Cyberspecies/Synth-Head/Software/Testing_N_Experimentation/Alpha_Release_Stack/IMPLEMENTATION_SUMMARY.md

# Project Implementation Summary

## Files Created

### Core Application Files

1. **main_new.cpp**
   - Main application entry point
   - Initializes UART and LED controllers
   - Handles data reception and LED updates
   - Manages button state transmission
   - Includes debug output

2. **include/UartController.h**
   - UART controller class header
   - Defines data structures for 196-byte LED frames
   - Button management (GPIO 5, 6, 7, 10)
   - UART configuration (GPIO 11 RX, GPIO 12 TX, 1Mbps)

3. **include/UartController.impl.hpp**
   - UART controller implementation
   - Receive buffer management for (13+13+9+14)×4 = 196 bytes
   - Button reading with debouncing
   - Button state transmission (4 bytes)
   - Data parsing by LED section

4. **LedController_new.h**
   - LED controller class header
   - Manages 4 separate LED strips (RGBW SK6812)
   - Supports 49 total LEDs (13+13+9+14)
   - Individual strip control methods

5. **LedController_new.impl.hpp**
   - LED controller implementation
   - NeoPixel strip initialization
   - RGBW data parsing and application
   - Test patterns and effects

6. **UART_LED_README.md**
   - Comprehensive documentation
   - Data protocol specification
   - Sender implementation examples (Python & Arduino)
   - Troubleshooting guide
   - Power considerations

## System Architecture

### Data Flow

```
Sender Device                     Receiver Device (This ESP32)
     |                                      |
     |  196 bytes LED data (RGBW)          |
     |------------------------------------>|
     |        UART @ 1Mbps                 |
     |                                      |
     |    4 bytes button state             |
     |<------------------------------------|
     |                                      |
```

### LED Data Structure (196 bytes total)

| Section | LEDs | Start Byte | End Byte | GPIO Pin |
|---|---|---|---|---|
| Left Fin | 13 | 0 | 51 | 18 |
| Right Fin  | 13 | 52 | 103 | 38 |
| Tongue | 9 | 104 | 139 | 8 |
| Scale | 14 | 140 | 195 | 37 |

Each LED = 4 bytes [R, G, B, W]

### Button Configuration

| Button | GPIO | Array Index |
|---|---|---|
| A | 5 | 0 |
| B | 6 | 1 |
| C | 7 | 2 |
| D | 10 | 3 |

## Coding Style Compliance

All code follows ARCOS coding style guidelines:
- ✅ 2-space indentation
- ✅ Tight brace style (no space before `{`)
- ✅ snake_case for variables
- ✅ camelCase for methods
- ✅ PascalCase for classes
- ✅ ALL_CAPS for constants
- ✅ Pointer/reference attached to type (`uint8_t*`)

## Next Steps

### To Use This Code:

1. **Rename/Replace Main File:**
   ```bash
   # Backup old main
   mv main.cpp main_old.cpp
   # Use new main
   mv main_new.cpp main.cpp
   ```

2. **Compile and Upload:**
   ```bash
   pio run --target upload
   ```

3. **Create Sender:**
   - Use Python example in UART_LED_README.md
   - Or use Arduino/ESP32 sender example
   - Connect UART pins (TX ↔ RX crossover)

4. **Test:**
   - Open serial monitor at 115200 baud
   - Send LED data from sender
   - Press buttons and verify transmission
   - Check debug output

## Key Features

- ✅ High-speed UART (1Mbps) for smooth animations
- ✅ 49 RGBW LEDs support (196 bytes/frame)
- ✅ 4-button input with state transmission
- ✅ Modular design (separate UART and LED controllers)
- ✅ Comprehensive error handling
- ✅ Debug output for monitoring
- ✅ Test patterns included

## Performance

- **Update Rate:** Up to 100 FPS theoretical (limited by UART bandwidth)
- **Recommended:** 30-60 FPS for stable operation
- **Button Polling:** 20 Hz (50ms intervals)
- **UART Bandwidth:** 1Mbps = 125 KB/s = 637 frames/second max

## Hardware Requirements

- ESP32-S3 (or compatible)
- 4× SK6812 RGBW LED strips
- 4× Push buttons
- 5V power supply (≥5A recommended)
- UART connection to sender device

---

**Status:** ✅ Ready for testing
**Date:** October 22, 2025
**ARCOS Alpha Release Stack**
