Cyberspecies/Synth-Head/Software/Testing_N_Experimentation/Alpha_Release_Stack/partitions_16mb.csv

# ESP32-S3-WROOM-1U-N16 Partition Table (16MB Flash)
# Name | Type | SubType | Offset | Size | Flags
nvs | data | nvs | 0x9000 | 0x5000
otadata | data | ota | 0xe000 | 0x2000
app0 | app | ota_0 | 0x10000 | 0x600000
app1 | app | ota_1 | 0x610000 | 0x600000
spiffs | data | spiffs | 0xC10000 | 0x3F0000
