Cyberspecies/Synth-Head/Embedded/Condensed/Substructure Power Distribution/Substructure Power Distribution.kicad_pcb

## KiCad design Embedded/Condensed/Substructure Power Distribution/Substructure Power Distribution.kicad_pcb (2025-07-12)

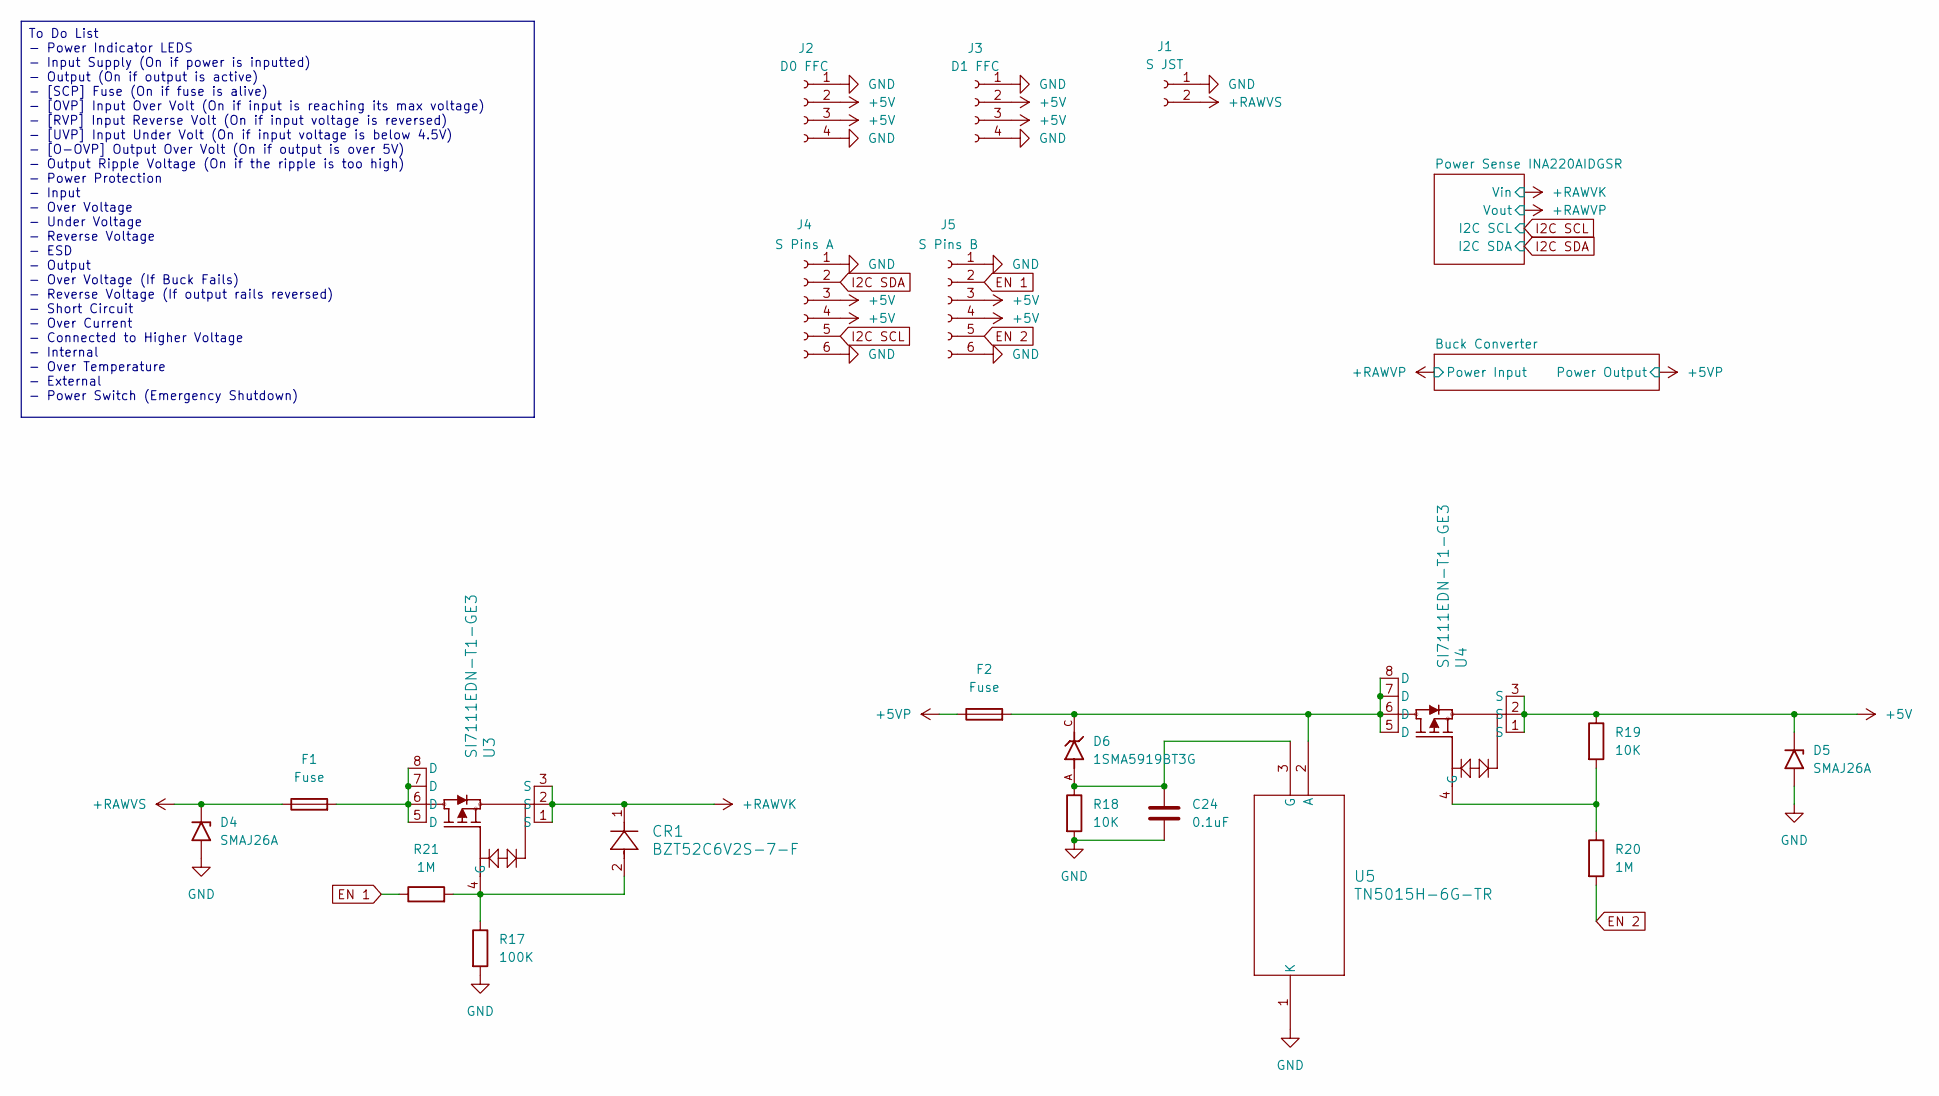
[picture p35: schematic Substructure Power Distribution.kicad_sch]

Parts:
C24: 0.1uF; C_0603_1608Metric_Pad1.08x0.95mm_HandSolder
CR1: BZT52C6V2S-7-F; SOD323_DIO
D4, D5: SMAJ26A; D_SMA
D6: 1SMA5919BT3G; DIOM5226X220N; PARTREV 10
F1, F2: Fuse; Fuse_1206_3216Metric_Pad1.42x1.75mm_HandSolder; LCSC C126815
J1: S JST; AMASS_XT30PW-M_1x02_P2.50mm_Horizontal
J2: D0 FFC; JST_XH_B4B-XH-A_1x04_P2.50mm_Vertical
J3: D1 FFC; JST_XH_B4B-XH-A_1x04_P2.50mm_Vertical
J4: S Pins A; PinHeader_1x06_P2.54mm_Vertical
J5: S Pins B; PinHeader_1x06_P2.54mm_Vertical
R17: 100K; R_0603_1608Metric_Pad0.98x0.95mm_HandSolder
R18, R19: 10K; R_0603_1608Metric_Pad0.98x0.95mm_HandSolder
R20, R21: 1M; R_0603_1608Metric_Pad0.98x0.95mm_HandSolder
U3, U4: SI7111EDN-T1-GE3; MOSFET_0DN-T1-GE3_VIS
U5: TN5015H-6G-TR; D2PAK_T2550_STM-M

Connections:
+5V: D5.1 (A1), J2.2, J2.3, J3.2, J3.3, J4.3, J4.4, J5.3, J5.4, R19.1, U4.1 (S), U4.2 (S), U4.3 (S)
+5VP: F2.1; also elsewhere on the board
+RAWVK: CR1.1, U3.1 (S), U3.2 (S), U3.3 (S); also elsewhere on the board
+RAWVS: D4.1 (A1), F1.1, J1.2
EN 1: J5.2, R21.1
EN 2: J5.5, R20.2
GND: C24.2, D4.2 (A2), D5.2 (A2), J1.1, J2.1, J2.4, J3.1, J3.4, J4.1, J4.6, J5.1, J5.6, R17.2, R18.2, U5.1 (K); also elsewhere on the board
I2C SCL: J4.5; also elsewhere on the board
I2C SDA: J4.2; also elsewhere on the board
unnamed: F1.2, U3.5 (D), U3.6 (D), U3.7 (D), U3.8 (D)
unnamed: CR1.2, R17.1, R21.2, U3.4 (G)
unnamed: R19.2, R20.1, U4.4 (G)
unnamed: D6.C, F2.2, U4.5 (D), U4.6 (D), U4.7 (D), U4.8 (D), U5.2 (A)
unnamed: C24.1, D6.A, R18.1, U5.3 (G)

Notes on the sheet:
To Do List - Power Indicator LEDS - Input Supply (On if power is inputted) - Output (On if output is active) - [SCP] Fuse (On if fuse is alive) - [OVP] Input Over Volt (On if input is reaching its max voltage) - [RVP] Input Reverse Volt (On if input voltage is reversed) - [UVP] Input Under Volt (On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

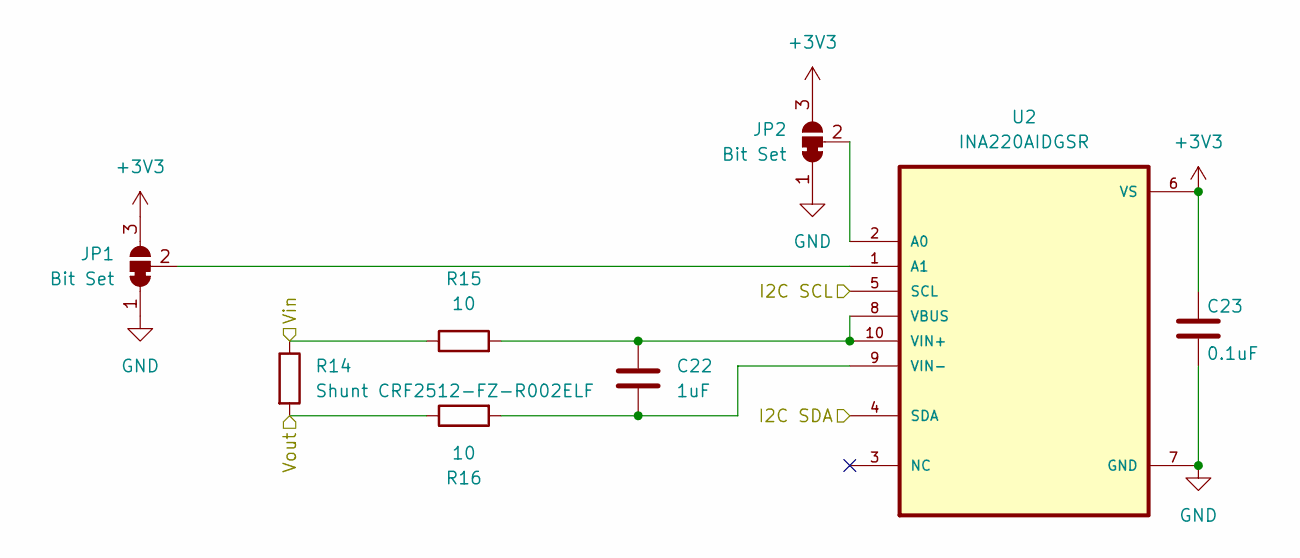
[picture p36: schematic PowerSense.kicad_sch]

Parts:
C22: 1uF; C_0402_1005Metric_Pad0.74x0.62mm_HandSolder
C23: 0.1uF; C_0402_1005Metric_Pad0.74x0.62mm_HandSolder
JP1, JP2: Bit Set; SolderJumper-3_P1.3mm_Bridged2Bar12_RoundedPad1.0x1.5mm
R14: Shunt CRF2512-FZ-R002ELF; R_2512_6332Metric_Pad1.40x3.35mm_HandSolder
R15, R16: 10; R_0402_1005Metric_Pad0.72x0.64mm_HandSolder
U2: INA220AIDGSR; SOP50P490X110-10N

Connections:
+3V3: C23.1, JP1.3 (B), JP2.3 (B), U2.6 (VS)
+RAWVK: R14.1, R15.1; also elsewhere on the board
+RAWVP: R14.2, R16.1; also elsewhere on the board
GND: C23.2, JP1.1 (A), JP2.1 (A), U2.7 (GND); also elsewhere on the board
I2C SCL: U2.5 (SCL); also elsewhere on the board
I2C SDA: U2.4 (SDA); also elsewhere on the board
unnamed: JP1.2 (C), U2.1 (A1)
unnamed: JP2.2 (C), U2.2 (A0)
unnamed: C22.1, R15.2, U2.8 (VBUS), U2.10 (VIN+)
unnamed: C22.2, R16.2, U2.9 (VIN-)

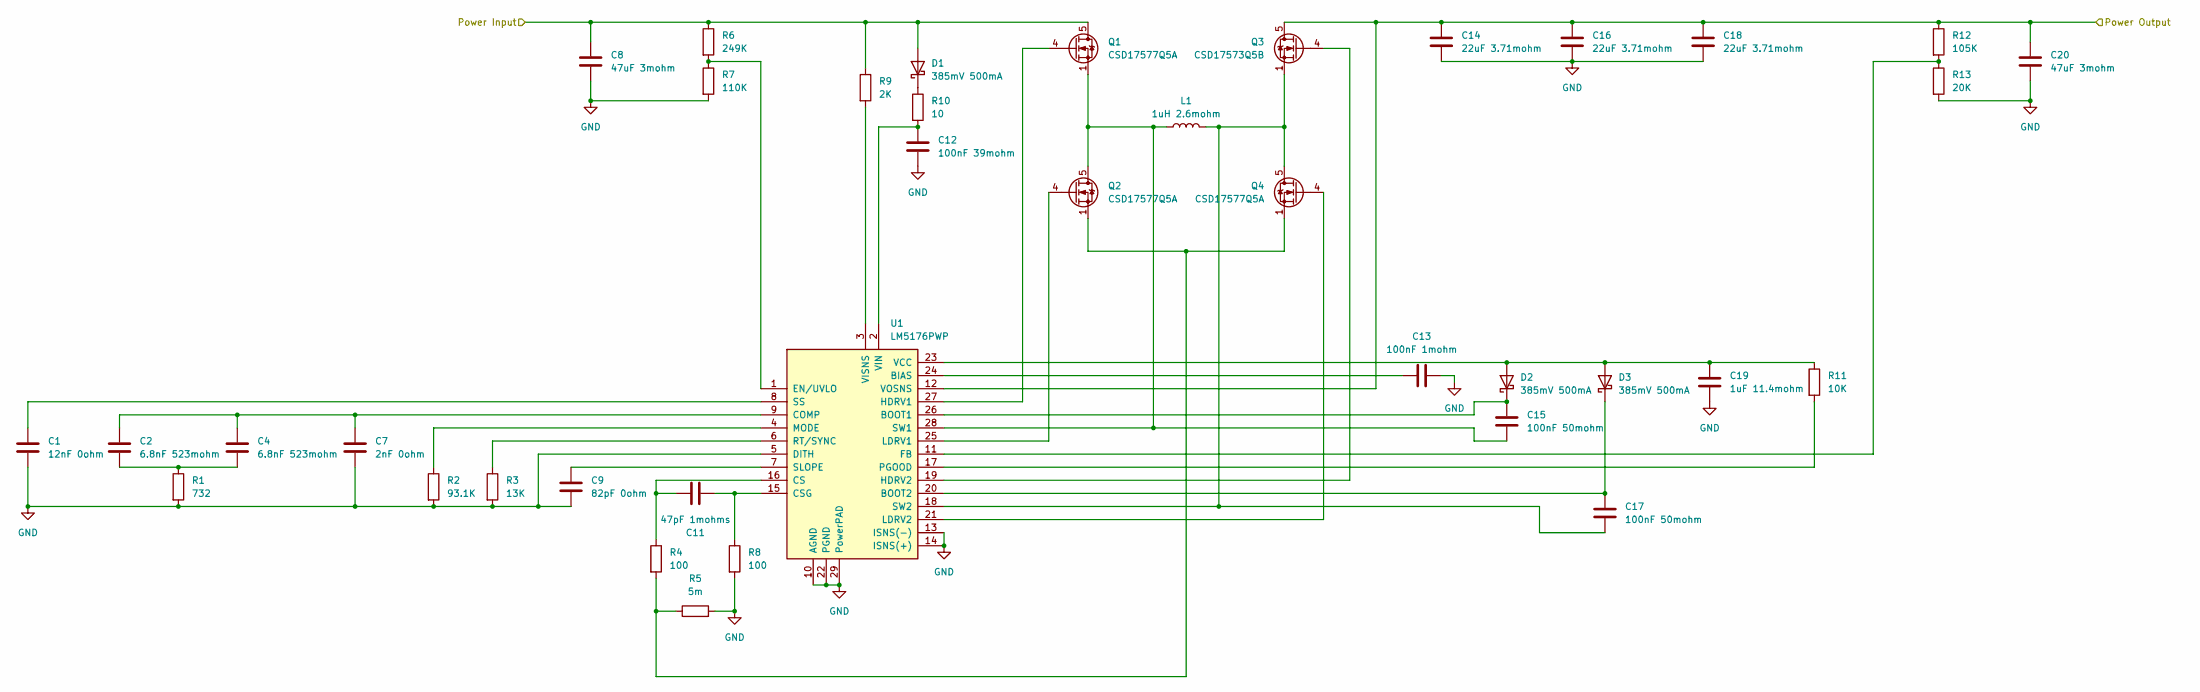
[picture p37: schematic buckconverter.kicad_sch]

Parts:
C1: 12nF 0ohm; C_0603_1608Metric_Pad1.08x0.95mm_HandSolder; LCSC C519540
C2, C4: 6.8nF 523mohm; C_0402_1005Metric_Pad0.74x0.62mm_HandSolder; LCSC C3840335
C7: 2nF 0ohm; C_0402_1005Metric_Pad0.74x0.62mm_HandSolder; LCSC C1845704
C8, C20: 47uF 3mohm; C_1210_3225Metric_Pad1.33x2.70mm_HandSolder; LCSC C77101
C9: 82pF 0ohm; C_0402_1005Metric_Pad0.74x0.62mm_HandSolder; LCSC C650992
C11: 47pF 1mohms; C_0402_1005Metric_Pad0.74x0.62mm_HandSolder; LCSC C76970
C12: 100nF 39mohm; R_0402_1005Metric_Pad0.72x0.64mm_HandSolder; LCSC C2181865
C13: 100nF 1mohm; C_0402_1005Metric_Pad0.74x0.62mm_HandSolder; LCSC C133086
C14, C16, C18: 22uF 3.71mohm; C_0603_1608Metric_Pad1.08x0.95mm_HandSolder; LCSC C86295
C15, C17: 100nF 50mohm; C_0603_1608Metric_Pad1.08x0.95mm_HandSolder; LCSC C92490
C19: 1uF 11.4mohm; C_0402_1005Metric_Pad0.74x0.62mm_HandSolder; LCSC C181015
D1: 385mV 500mA; D_SOD-123; LCSC C155367
D2, D3: 385mV 500mA; D_SOD-123; LCSC C398783
L1: 1uH 2.6mohm; XAL7070-102ME; LCSC C6609502
Q1, Q2, Q4: CSD17577Q5A; TDSON-8-1; LCSC C475504
Q3: CSD17573Q5B; TDSON-8-1; LCSC C202231
R1: 732; R_0402_1005Metric_Pad0.72x0.64mm_HandSolder; LCSC C2085222
R2: 93.1K; R_0402_1005Metric_Pad0.72x0.64mm_HandSolder; LCSC C2085865
R3: 13K; R_0402_1005Metric_Pad0.72x0.64mm_HandSolder; LCSC C294438
R4, R8: 100; R_0402_1005Metric_Pad0.72x0.64mm_HandSolder; LCSC C844713
R5: 5m; R_2512_6332Metric_Pad1.40x3.35mm_HandSolder; LCSC C22468851
R6: 249K; C_0402_1005Metric_Pad0.74x0.62mm_HandSolder; LCSC C482111
R7: 110K; C_0402_1005Metric_Pad0.74x0.62mm_HandSolder; LCSC C481928
R9: 2K; C_0402_1005Metric_Pad0.74x0.62mm_HandSolder; LCSC C482125
R10: 10; R_0402_1005Metric_Pad0.72x0.64mm_HandSolder; LCSC C481926
R11: 10K; R_0402_1005Metric_Pad0.72x0.64mm_HandSolder; LCSC C71617
R12: 105K; R_0603_1608Metric_Pad0.98x0.95mm_HandSolder; LCSC C227540
R13: 20K; R_0603_1608Metric_Pad0.98x0.95mm_HandSolder; LCSC C105575
U1: LM5176PWP; HTSSOP-28-1EP_4.4x9.7mm_P0.65mm_EP3.4x9.5mm_ThermalVias

Connections:
+5VP: C14.1, C16.1, C18.1, C20.1, Q3.5 (D), R12.1, U1.12 (VOSNS); also elsewhere on the board
+RAWVP: C8.1, D1.2 (A), Q1.5 (D), R6.1, R9.1; also elsewhere on the board
GND: C1.2, C7.2, C8.2, C9.2, C12.2, C13.2, C14.2, C16.2, C18.2, C19.2, C20.2, R1.2, R2.2, R3.2, R5.2, R7.2, R8.2, R13.2, U1.5 (DITH), U1.10 (AGND), U1.13 (ISNS(-)), U1.14 (ISNS(+)), U1.22 (PGND), U1.29 (PowerPAD); also elsewhere on the board
unnamed: C2.2, C4.2, R1.1
unnamed: D1.1 (K), R10.1
unnamed: C19.1, D2.2 (A), D3.2 (A), R11.1, U1.23 (VCC)
unnamed: C15.1, D2.1 (K), U1.26 (BOOT1)
unnamed: C17.1, D3.1 (K), U1.20 (BOOT2)
unnamed: Q1.4 (G), U1.27 (HDRV1)
unnamed: C15.2, L1.1, Q1.1 (S), Q1.2 (S), Q1.3 (S), Q2.5 (D), U1.28 (SW1)
unnamed: Q2.4 (G), U1.25 (LDRV1)
unnamed: Q2.1 (S), Q2.2 (S), Q2.3 (S), Q4.1 (S), Q4.2 (S), Q4.3 (S), R4.2, R5.1
unnamed: Q3.4 (G), U1.19 (HDRV2)
unnamed: C17.2, L1.2, Q3.1 (S), Q3.2 (S), Q3.3 (S), Q4.5 (D), U1.18 (SW2)
unnamed: Q4.4 (G), U1.21 (LDRV2)
unnamed: C13.1, U1.24 (BIAS)
unnamed: C2.1, C4.1, C7.1, U1.9 (COMP)
unnamed: C11.1, R4.1, U1.16 (CS)
unnamed: C11.2, R8.1, U1.15 (CSG)
unnamed: R6.2, R7.1, U1.1 (EN/UVLO)
unnamed: R12.2, R13.1, U1.11 (FB)
unnamed: R2.1, U1.4 (MODE)
unnamed: R11.2, U1.17 (PGOOD)
unnamed: R3.1, U1.6 (RT/SYNC)
unnamed: C9.1, U1.7 (SLOPE)
unnamed: C1.1, U1.8 (SS)
unnamed: C12.1, R10.2, U1.2 (VIN)
unnamed: R9.2, U1.3 (VISNS)

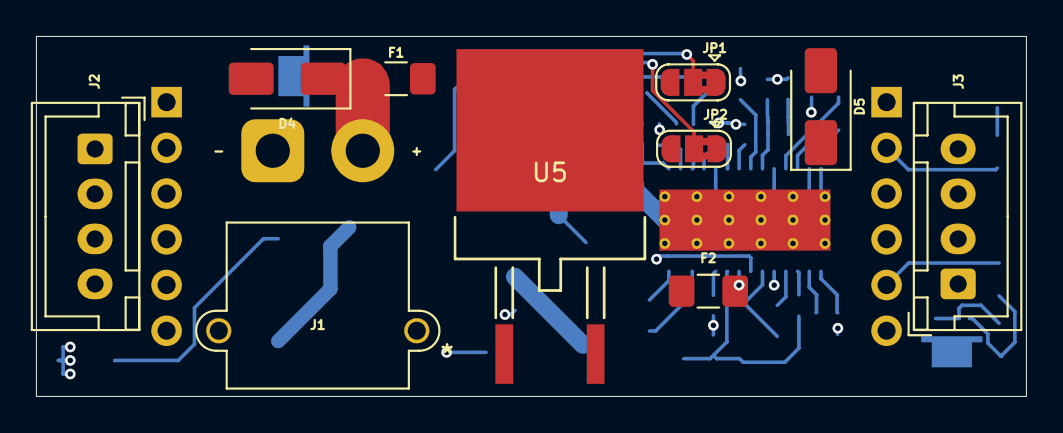
[picture p38: board Embedded/Condensed/Substructure Power Distribution/Substructure Power… from above]

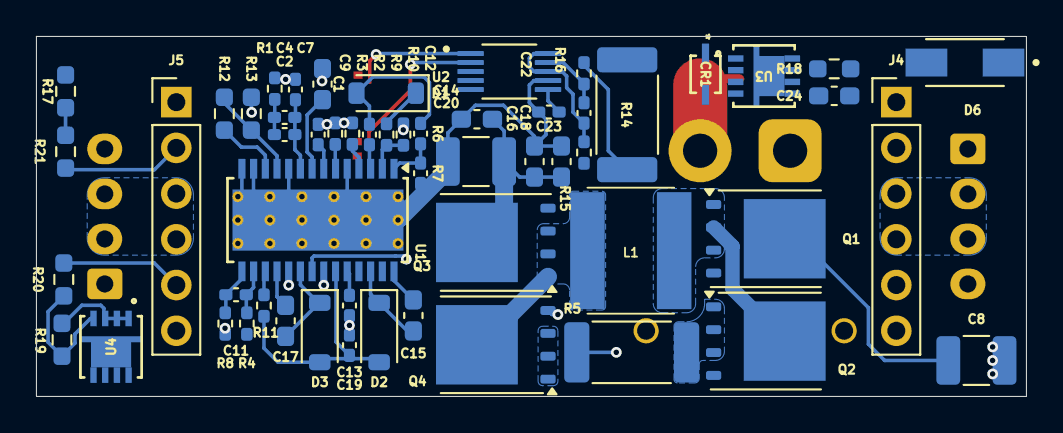
[picture p39: board Embedded/Condensed/Substructure Power Distribution/Substructure Power… from below]

Board: 4 copper layers, 55.0 x 20.0 mm, 66 parts (56 on the bottom side), 45 nets.
