Cyberspecies/Synth-Head/Embedded/Recondensed/Main Buttons/Main Buttons.kicad_pcb

## KiCad design Embedded/Recondensed/Main Buttons/Main Buttons.kicad_pcb (2025-07-26)

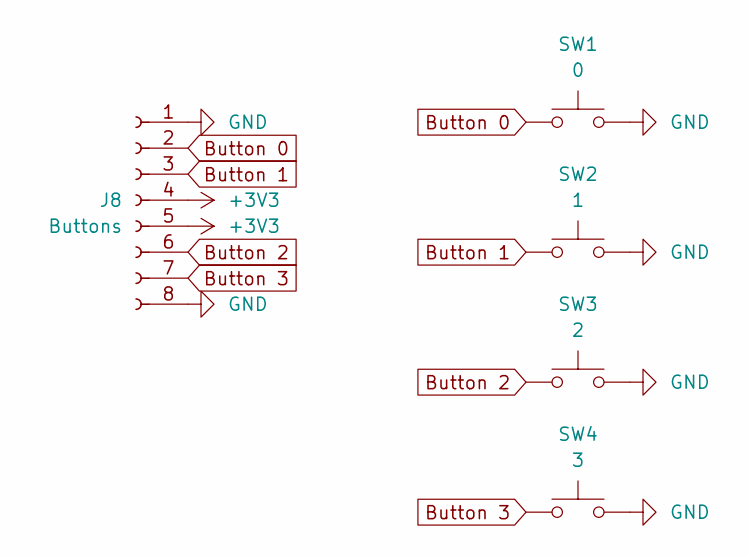
[picture p40: schematic Main Buttons.kicad_sch]

Parts:
J8: Buttons; JST_GH_SM08B-GHS-TB_1x08-1MP_P1.25mm_Horizontal
SW1: 0; SW_PUSH_6mm_H5mm
SW2: 1; SW_PUSH_6mm_H5mm
SW3: 2; SW_PUSH_6mm_H5mm
SW4: 3; SW_PUSH_6mm_H5mm

Connections:
+3V3: J8.4, J8.5
Button 0: J8.2, SW1.1
Button 1: J8.3, SW2.1
Button 2: J8.6, SW3.1
Button 3: J8.7, SW4.1
GND: J8.1, J8.8, SW1.2, SW2.2, SW3.2, SW4.2

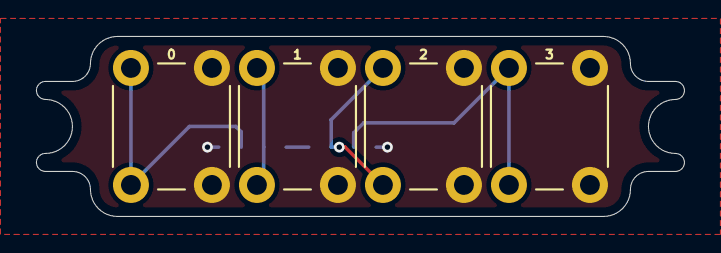
[picture p41: board Main Buttons.kicad_pcb from above]

Board: 2 copper layers, 36.0 x 10.0 mm, 5 parts (1 on the bottom side), 6 nets.
