Cyberspecies/Synth-Head/Embedded/HUB75 Display Adapter/HUB75 Display Adapter.kicad_pcb

## KiCad design Embedded/OBSOLETE DESIGNS (DO NOT USE)/Old 1/HUB75 Display Adapter/HUB75 Display Adapter.kicad_pcb (2024-12-31, an earlier design)

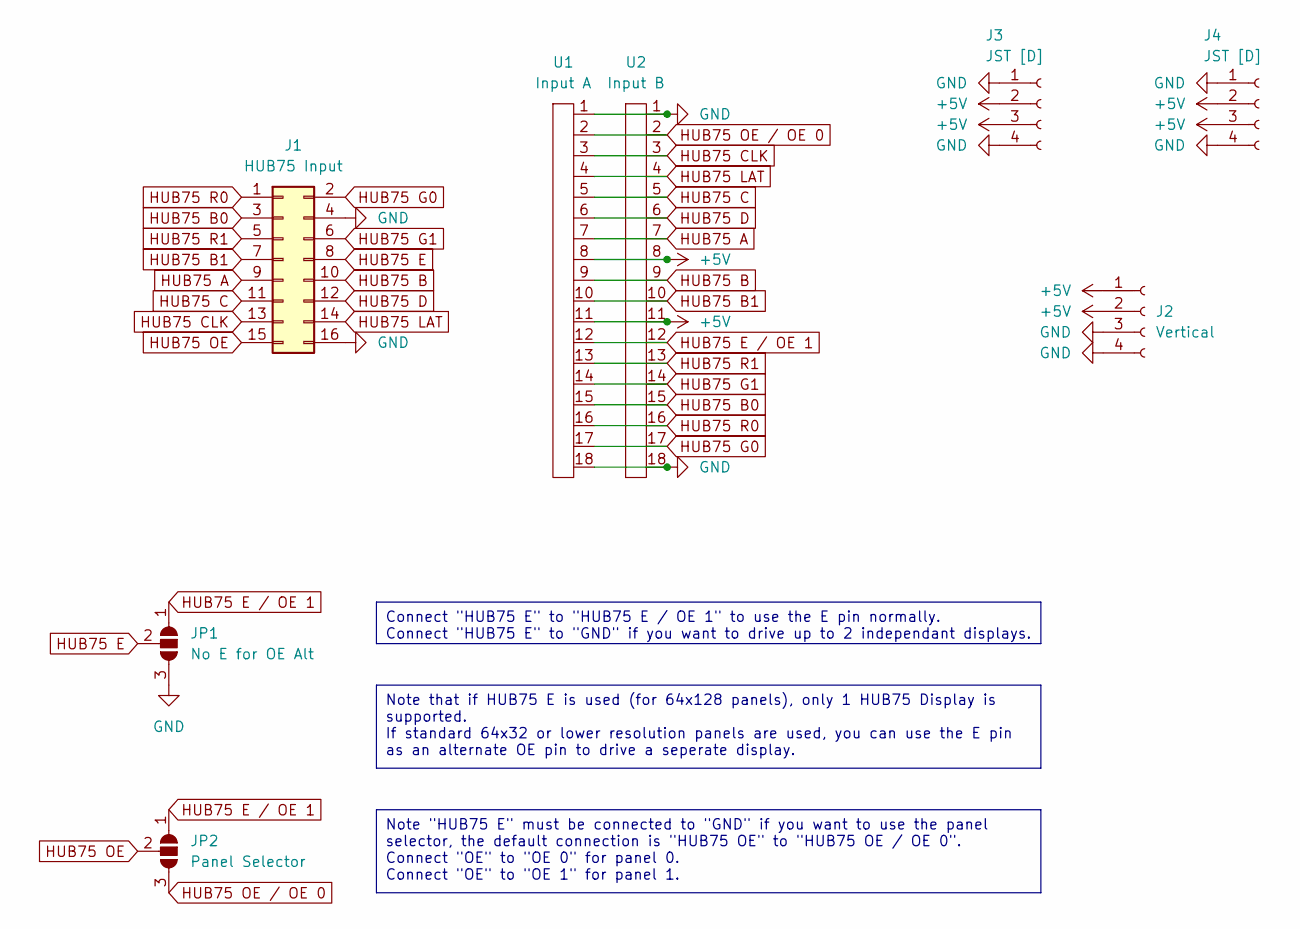
[picture p42: schematic HUB75 Display Adapter.kicad_sch]

Parts:
J1: HUB75 Input; PinHeader_2x08_P2.54mm_Vertical
J2: Vertical; Molex_KK-396_5273-04A_1x04_P3.96mm_Vertical
J3, J4: JST [D]; Molex_PicoBlade_53048-0410_1x04_P1.25mm_Horizontal
JP1: No E for OE Alt; SolderJumper-3_P1.3mm_Open_RoundedPad1.0x1.5mm_NumberLabels
JP2: Panel Selector; SolderJumper-3_P1.3mm_Open_RoundedPad1.0x1.5mm_NumberLabels
U1: Input A; FFC Aliexpress 0.5mm 18P
U2: Input B; FFC Aliexpress 0.5mm 18P

Connections:
+5V: J2.1, J2.2, J3.2, J3.3, J4.2, J4.3, U1.8, U1.11, U2.8, U2.11
GND: J1.4, J1.16, J2.3, J2.4, J3.1, J3.4, J4.1, J4.4, JP1.3 (B), U1.1, U1.18, U2.1, U2.18
HUB75 A: J1.9, U1.7, U2.7
HUB75 B: J1.10, U1.9, U2.9
HUB75 B0: J1.3, U1.15, U2.15
HUB75 B1: J1.7, U1.10, U2.10
HUB75 C: J1.11, U1.5, U2.5
HUB75 CLK: J1.13, U1.3, U2.3
HUB75 D: J1.12, U1.6, U2.6
HUB75 E: J1.8, JP1.2 (C)
HUB75 E / OE 1: JP1.1 (A), JP2.1 (A), U1.12, U2.12
HUB75 G0: J1.2, U1.17, U2.17
HUB75 G1: J1.6, U1.14, U2.14
HUB75 LAT: J1.14, U1.4, U2.4
HUB75 OE: J1.15, JP2.2 (C)
HUB75 OE / OE 0: JP2.3 (B), U1.2, U2.2
HUB75 R0: J1.1, U1.16, U2.16
HUB75 R1: J1.5, U1.13, U2.13

Notes on the sheet:
Note that if HUB75 E is used (for 64x128 panels), only 1 HUB75 Display is supported. If standard 64x32 or lower resolution panels are used, you can use the E pin as an alternate OE pin to drive a seperate display.
Connect "HUB75 E" to "HUB75 E / OE 1" to use the E pin normally. Connect "HUB75 E" to "GND" if you want to drive up to 2 independant displays.
Note "HUB75 E" must be connected to "GND" if you want to use the panel selector, the default connection is "HUB75 OE" to "HUB75 OE / OE 0". Connect "OE" to "OE 0" for panel 0. Connect "OE" to "OE 1" for panel 1.

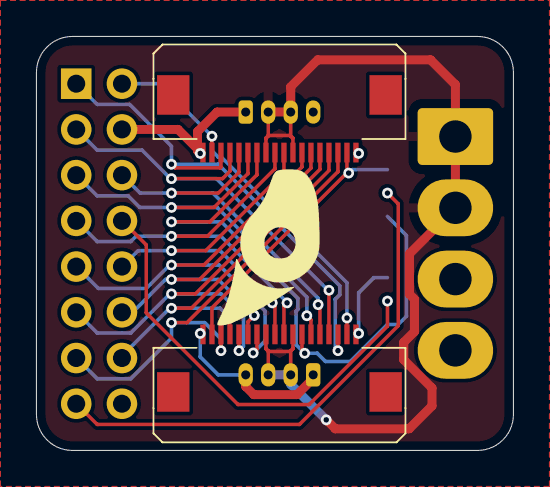
[picture p43: board HUB75 Display Adapter.kicad_pcb from above]

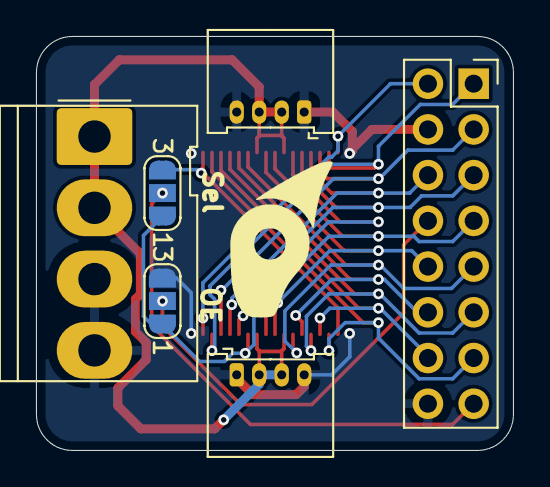
[picture p44: board HUB75 Display Adapter.kicad_pcb from below]

Board: 2 copper layers, 26.5 x 23.0 mm, 8 parts (6 on the bottom side), 18 nets.
