Cyberspecies/Synth-Head/Embedded/OBSOLETE DESIGNS (DO NOT USE)/Old 1/UI Display/UI Display.kicad_pcb

## KiCad design Embedded/OBSOLETE DESIGNS (DO NOT USE)/Old 1/UI Display/UI Display.kicad_pcb (2024-12-31, an earlier design)

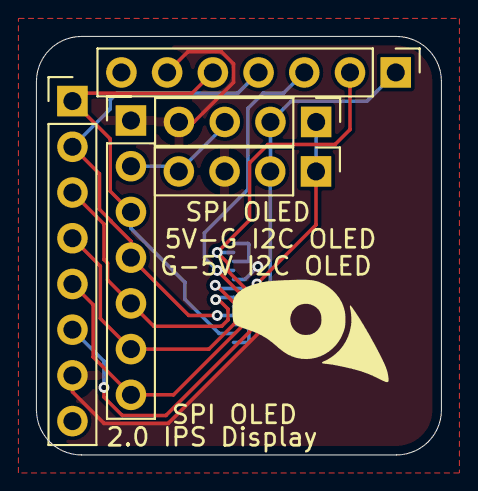
[picture p45: board UI Display.kicad_pcb from above]

Board: 2 copper layers, 22.5 x 23.2 mm, 6 parts (1 on the bottom side), 8 nets.

Parts:
J1: 2.0 IPS Display; PinHeader_1x08_P2.54mm_Vertical
J2, J5: SPI OLED; PinHeader_1x07_P2.54mm_Vertical
J3: 5V-G I2C OLED; PinHeader_1x04_P2.54mm_Vertical
J4: G-5V I2C OLED; PinHeader_1x04_P2.54mm_Vertical
U2: FFC [U]; FFC Aliexpress 0.5mm 12P

Connections:
+5V: J1.7, J2.1, J3.4, J4.3, J5.6, U2.5, U2.8
GND: J1.8, J2.2, J3.3, J4.4, J5.7, U2.1, U2.3, U2.10, U2.12
UI 0: J1.1, J2.3, J5.5, U2.2
UI 1: J1.2, J2.4, J5.4, U2.4
UI 2: J1.5, J2.7, J5.3, U2.9
UI 3: J1.6, J5.2, U2.11
UI IO 0: J1.3, J2.5, J3.2, J4.2, J5.1, U2.6
UI IO 1: J1.4, J2.6, J3.1, J4.1, U2.7
