Cyberspecies/Synth-Head/Embedded/OBSOLETE DESIGNS (DO NOT USE)/Old 1/Substructure/Substructure.kicad_pcb

## KiCad design Embedded/OBSOLETE DESIGNS (DO NOT USE)/Old 1/Substructure/Substructure.kicad_pcb (2024-12-29, an earlier design)

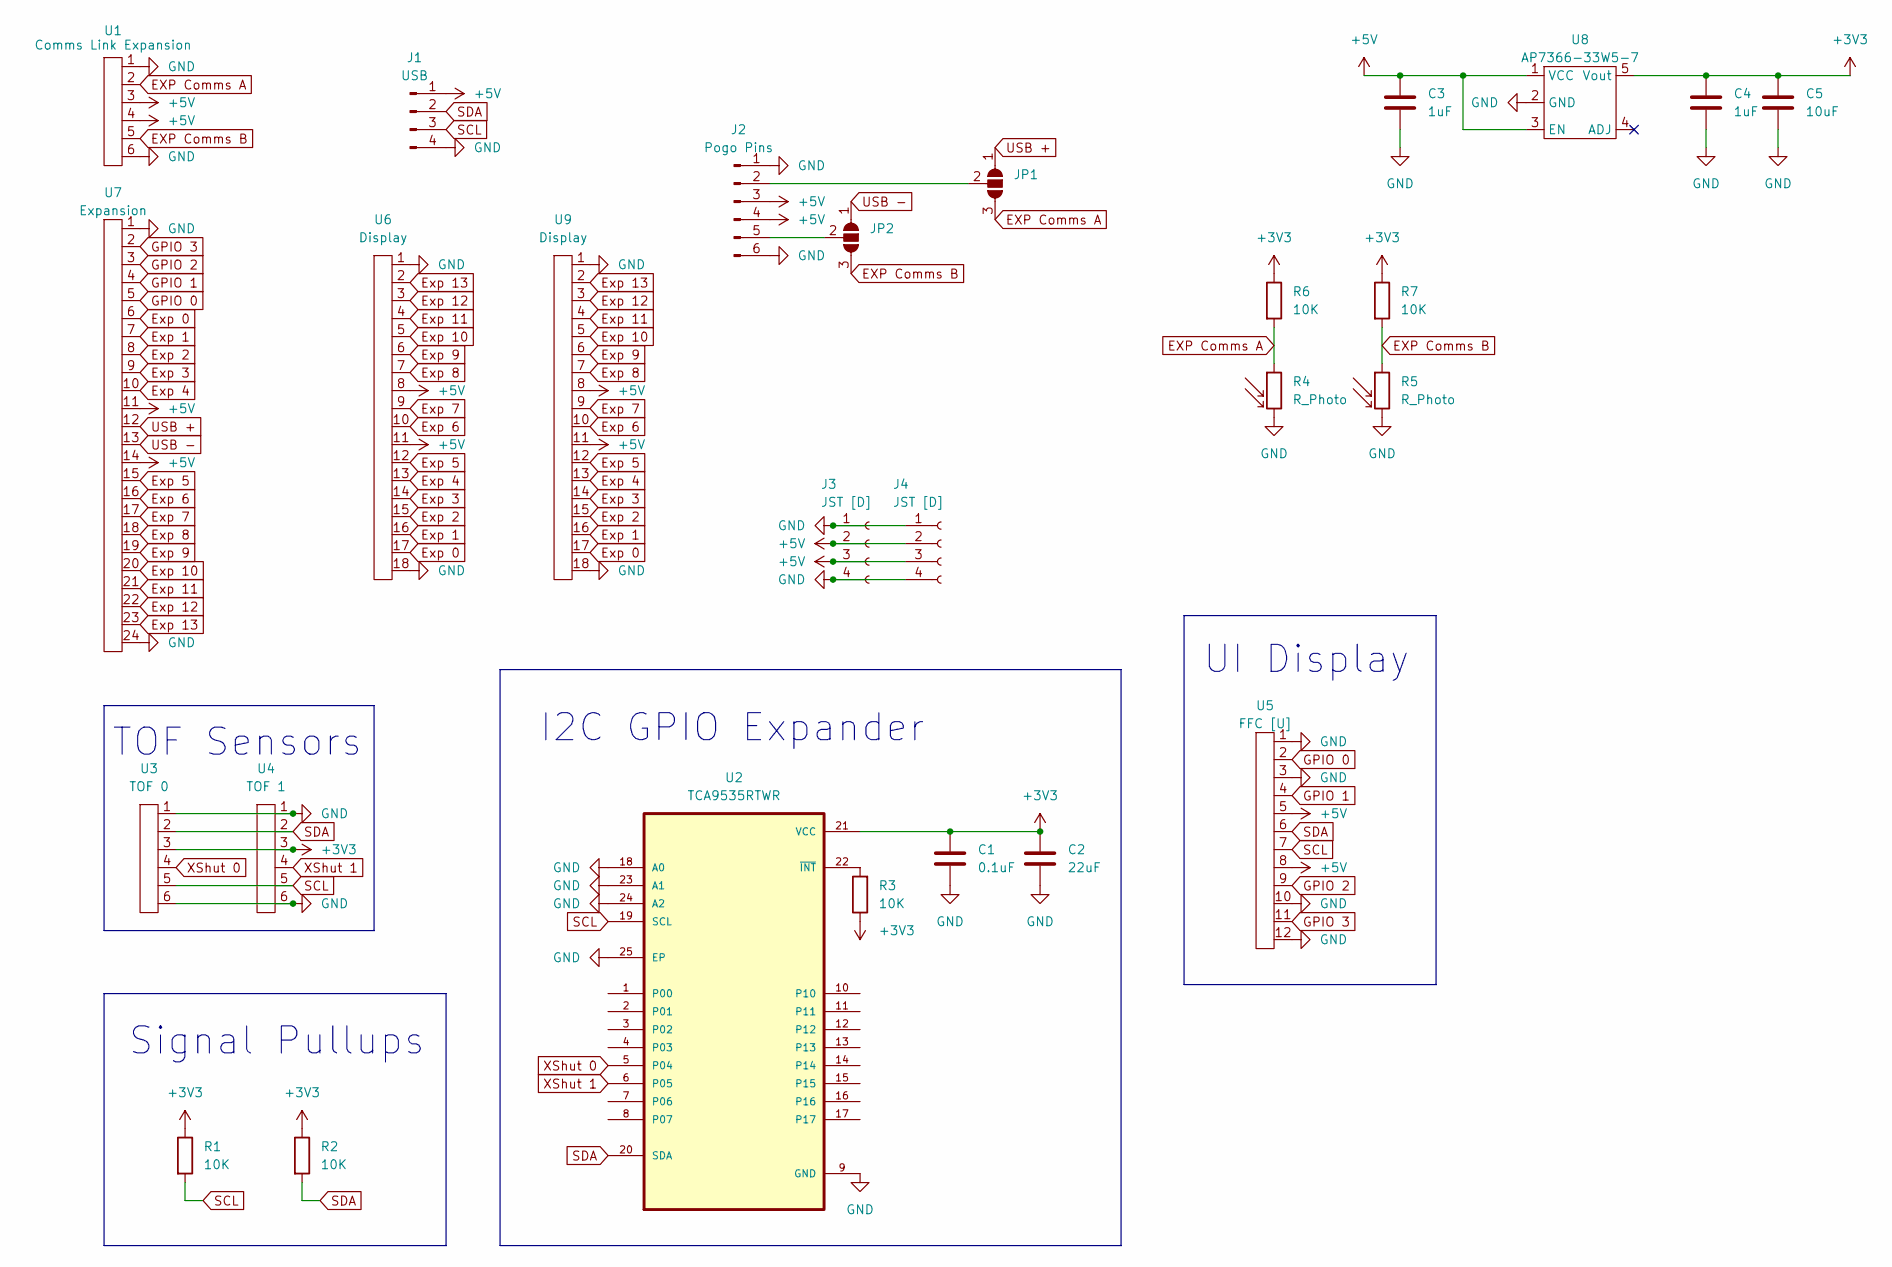
[picture p46: schematic Substructure.kicad_sch]

Parts:
C1: 0.1uF; C_0603_1608Metric
C2: 22uF; C_0603_1608Metric_Pad1.08x0.95mm_HandSolder
C3, C4: 1uF; R_0603_1608Metric
C5: 10uF; C_0603_1608Metric
J1: USB; Hirose_DF13-04P-1.25DS_1x04_P1.25mm_Horizontal
J2: Pogo Pins; PinHeader_1x06_P2.54mm_Vertical
J3, J4: JST [D]; Molex_PicoBlade_53048-0410_1x04_P1.25mm_Horizontal
JP1, JP2: SolderJumper_3_Open; SolderJumper-3_P1.3mm_Open_RoundedPad1.0x1.5mm
R1, R2, R6, R7: 10K; R_0603_1608Metric_Pad0.98x0.95mm_HandSolder
R3: 10K; R_0603_1608Metric
R4, R5: R_Photo; Photoresistor Aliexpress
U1: Comms Link Expansion; FFC Aliexpress 0.5mm 6P
U2: TCA9535RTWR; QFN50P400X400X80-25N
U3: TOF 0; Hirose_DF13-06P-1.25DS_1x06_P1.25mm_Horizontal
U4: TOF 1; Hirose_DF13-06P-1.25DS_1x06_P1.25mm_Horizontal
U5: FFC [U]; FFC Aliexpress 0.5mm 12P
U6, U9: Display; FFC Aliexpress 0.5mm 18P
U7: Expansion; FFC Aliexpress 0.5mm 24P
U8: AP7366-33W5-7; AP7366

Connections:
+3V3: C1.1, C2.1, C4.1, C5.1, R1.1, R2.1, R3.1, R6.1, R7.1, U2.21 (VCC), U3.3, U4.3, U8.5 (Vout)
+5V: C3.1, J1.1, J2.3, J2.4, J3.2, J3.3, J4.2, J4.3, U1.3, U1.4, U5.5, U5.8, U6.8, U6.11, U7.11, U7.14, U8.1 (VCC), U8.3 (EN), U9.8, U9.11
EXP Comms A: JP1.3 (B), R4.1, R6.2, U1.2
EXP Comms B: JP2.3 (B), R5.1, R7.2, U1.5
Exp 0: U6.17, U7.6, U9.17
Exp 1: U6.16, U7.7, U9.16
Exp 2: U6.15, U7.8, U9.15
Exp 3: U6.14, U7.9, U9.14
Exp 4: U6.13, U7.10, U9.13
Exp 5: U6.12, U7.15, U9.12
Exp 6: U6.10, U7.16, U9.10
Exp 7: U6.9, U7.17, U9.9
Exp 8: U6.7, U7.18, U9.7
Exp 9: U6.6, U7.19, U9.6
Exp 10: U6.5, U7.20, U9.5
Exp 11: U6.4, U7.21, U9.4
Exp 12: U6.3, U7.22, U9.3
Exp 13: U6.2, U7.23, U9.2
GND: C1.2, C2.2, C3.2, C4.2, C5.2, J1.4, J2.1, J2.6, J3.1, J3.4, J4.1, J4.4, R4.2, R5.2, U1.1, U1.6, U2.9 (GND), U2.18 (A0), U2.23 (A1), U2.24 (A2), U2.25 (EP), U3.1, U3.6, U4.1, U4.6, U5.1, U5.3, U5.10, U5.12, U6.1, U6.18, U7.1, U7.24, U8.2 (GND), U9.1, U9.18
GPIO 0: U5.2, U7.5
GPIO 1: U5.4, U7.4
GPIO 2: U5.9, U7.3
GPIO 3: U5.11, U7.2
unnamed: J2.2, JP1.2 (C)
unnamed: J2.5, JP2.2 (C)
unnamed: R3.2, U2.22 (~INT)
SCL: J1.3, R1.2, U2.19 (SCL), U3.5, U4.5, U5.7
SDA: J1.2, R2.2, U2.20 (SDA), U3.2, U4.2, U5.6
USB +: JP1.1 (A), U7.12
USB -: JP2.1 (A), U7.13
XShut 0: U2.5 (P04), U3.4
XShut 1: U2.6 (P05), U4.4

Notes on the sheet:
Signal Pullups
UI Display
I2C GPIO Expander
TOF Sensors

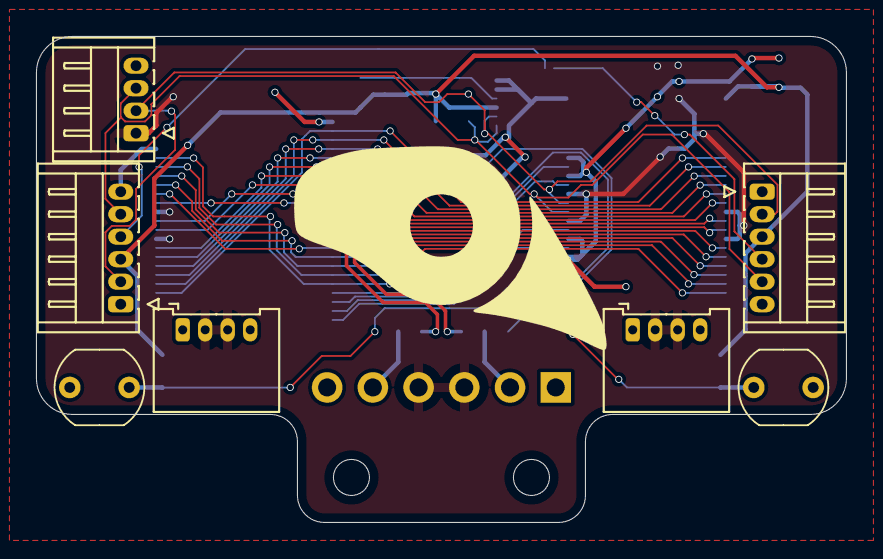
[picture p47: board Substructure.kicad_pcb from above]

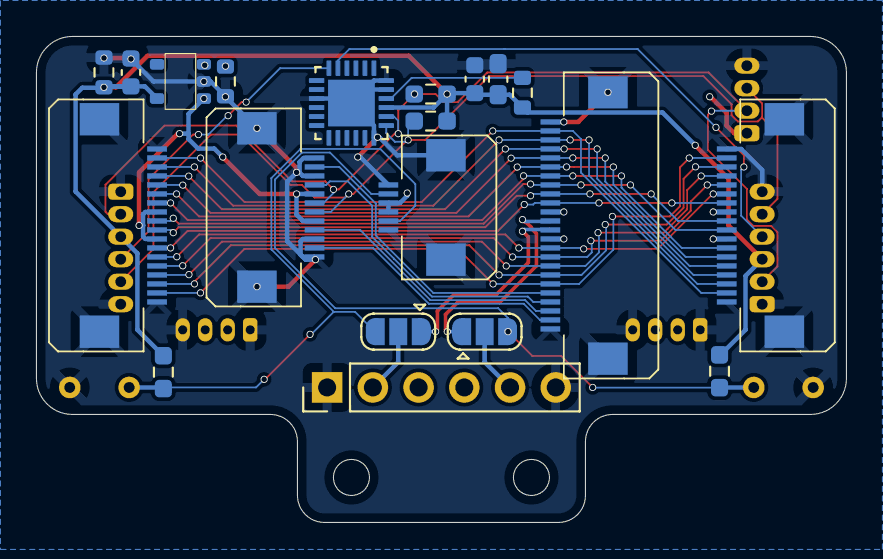
[picture p48: board Substructure.kicad_pcb from below]

Board: 2 copper layers, 45.0 x 27.0 mm, 27 parts (20 on the bottom side), 32 nets.
