Cyberspecies/Synth-Head/Embedded/OBSOLETE DESIGNS (DO NOT USE)/Old 0/Misc Circuits & Adapters/Misc Circuits & Adapters.kicad_pcb

## KiCad design Embedded/OBSOLETE DESIGNS (DO NOT USE)/Old 0/Misc Circuits & Adapters/Misc Circuits & Adapters.kicad_pcb (2024-12-26, an earlier design)

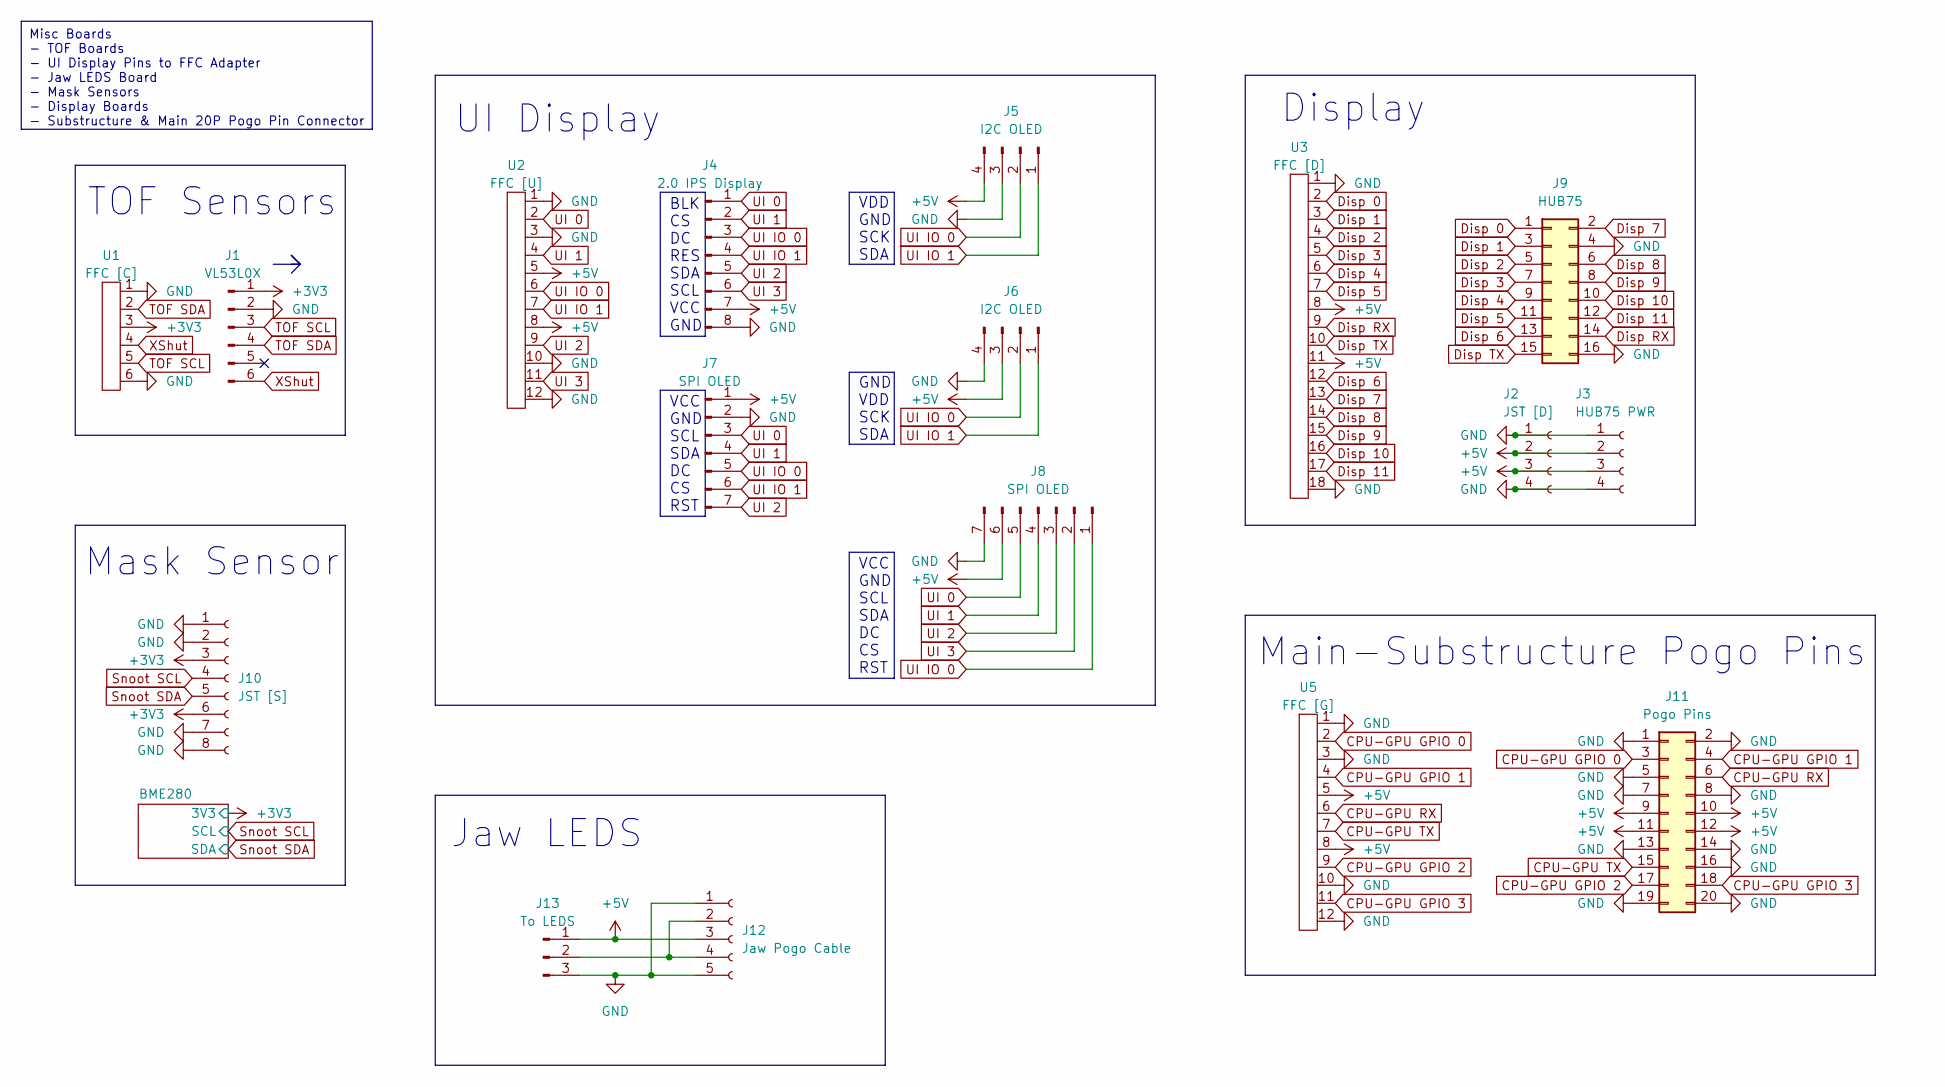
[picture p49: schematic Misc Circuits & Adapters.kicad_sch]

Parts:
J1: VL53L0X; PinHeader_1x06_P2.54mm_Vertical
J2: JST [D]; Molex_PicoBlade_53048-0410_1x04_P1.25mm_Horizontal
J3: HUB75 PWR; Molex_KK-396_A-41791-0004_1x04_P3.96mm_Vertical
J4: 2.0 IPS Display; PinHeader_1x08_P2.54mm_Vertical
J5, J6: I2C OLED; PinHeader_1x04_P2.54mm_Vertical
J7, J8: SPI OLED; PinHeader_1x07_P2.54mm_Vertical
J9: HUB75; PinHeader_2x08_P2.54mm_Vertical
J10: JST [S]; Molex_PicoBlade_53047-0810_1x08_P1.25mm_Vertical
J11: Pogo Pins; 2.2mm 20P
J12: Jaw Pogo Cable; PinHeader_1x05_P2.54mm_Vertical
J13: To LEDS; PinHeader_1x03_P2.54mm_Vertical
U1: FFC [C]; FFC Aliexpress 0.5mm 6P
U2: FFC [U]; FFC Aliexpress 0.5mm 12P
U3: FFC [D]; FFC Aliexpress 0.5mm 18P
U5: FFC [G]; FFC Aliexpress 0.5mm 12P

Connections:
+3V3: J1.1, J10.3, J10.6, U1.3; also elsewhere on the board
+5V: J2.2, J2.3, J3.2, J3.3, J4.7, J5.4, J6.3, J7.1, J8.6, J11.9, J11.10, J11.11, J11.12, J12.3, J13.1, U2.5, U2.8, U3.8, U3.11, U5.5, U5.8
CPU-GPU GPIO 0: J11.3, U5.2
CPU-GPU GPIO 1: J11.4, U5.4
CPU-GPU GPIO 2: J11.17, U5.9
CPU-GPU GPIO 3: J11.18, U5.11
CPU-GPU RX: J11.6, U5.6
CPU-GPU TX: J11.15, U5.7
Disp 0: J9.1, U3.2
Disp 1: J9.3, U3.3
Disp 2: J9.5, U3.4
Disp 3: J9.7, U3.5
Disp 4: J9.9, U3.6
Disp 5: J9.11, U3.7
Disp 6: J9.13, U3.12
Disp 7: J9.2, U3.13
Disp 8: J9.6, U3.14
Disp 9: J9.8, U3.15
Disp 10: J9.10, U3.16
Disp 11: J9.12, U3.17
Disp RX: J9.14, U3.9
Disp TX: J9.15, U3.10
GND: J1.2, J2.1, J2.4, J3.1, J3.4, J4.8, J5.3, J6.4, J7.2, J8.7, J9.4, J9.16, J10.1, J10.2, J10.7, J10.8, J11.1, J11.2, J11.5, J11.7, J11.8, J11.13, J11.14, J11.16, J11.19, J11.20, J12.1, J12.5, J13.3, U1.1, U1.6, U2.1, U2.3, U2.10, U2.12, U3.1, U3.18, U5.1, U5.3, U5.10, U5.12; also elsewhere on the board
unnamed: J12.2, J12.4, J13.2
Snoot SCL: J10.4; also elsewhere on the board
Snoot SDA: J10.5; also elsewhere on the board
TOF SCL: J1.3, U1.5
TOF SDA: J1.4, U1.2
UI 0: J4.1, J7.3, J8.5, U2.2
UI 1: J4.2, J7.4, J8.4, U2.4
UI 2: J4.5, J7.7, J8.3, U2.9
UI 3: J4.6, J8.2, U2.11
UI IO 0: J4.3, J5.2, J6.2, J7.5, J8.1, U2.6
UI IO 1: J4.4, J5.1, J6.1, J7.6, U2.7
XShut: J1.6, U1.4

Notes on the sheet:
VDD GND SCK SDA
VCC GND SCL SDA DC CS RST
BLK CS DC RES SDA SCL VCC GND
GND VDD SCK SDA
Misc Boards - TOF Boards - UI Display Pins to FFC Adapter - Jaw LEDS Board - Mask Sensors - Display Boards - Substructure & Main 20P Pogo Pin Connector
Display
Main-Substructure Pogo Pins
UI Display
TOF Sensors
Mask Sensor
Jaw LEDS

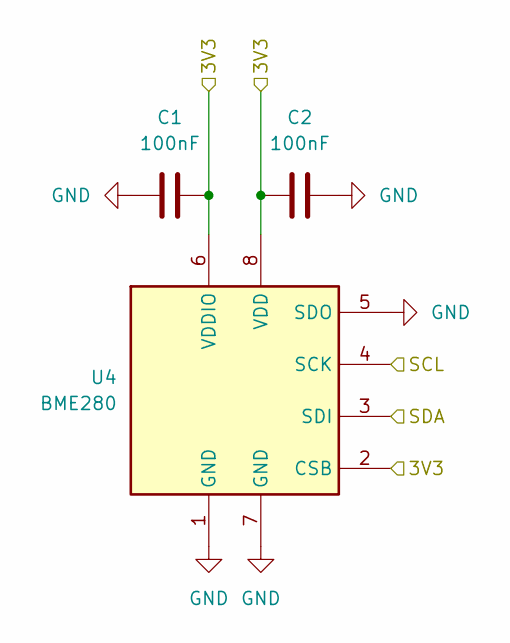
[picture p50: schematic BME280.kicad_sch]

Parts:
C1, C2: 100nF; C_0603_1608Metric_Pad1.08x0.95mm_HandSolder
U4: BME280; Bosch_LGA-8_2.5x2.5mm_P0.65mm_ClockwisePinNumbering

Connections:
+3V3: C1.2, C2.1, U4.2 (CSB), U4.6 (VDDIO), U4.8 (VDD); also elsewhere on the board
GND: C1.1, C2.2, U4.1 (GND), U4.5 (SDO), U4.7 (GND); also elsewhere on the board
Snoot SCL: U4.4 (SCK); also elsewhere on the board
Snoot SDA: U4.3 (SDI); also elsewhere on the board

Board: 2 copper layers, 20 parts (0 on the bottom side), 35 nets, no tracks yet.
