Cyberspecies/Synth-Head/Embedded/OBSOLETE DESIGNS (DO NOT USE)/Old 0/Synth Head Mask/Synth Head Mask.kicad_pcb

## KiCad design Embedded/OBSOLETE DESIGNS (DO NOT USE)/Old 0/Synth Head Mask/Synth Head Mask.kicad_pcb (2024-12-26, an earlier design)

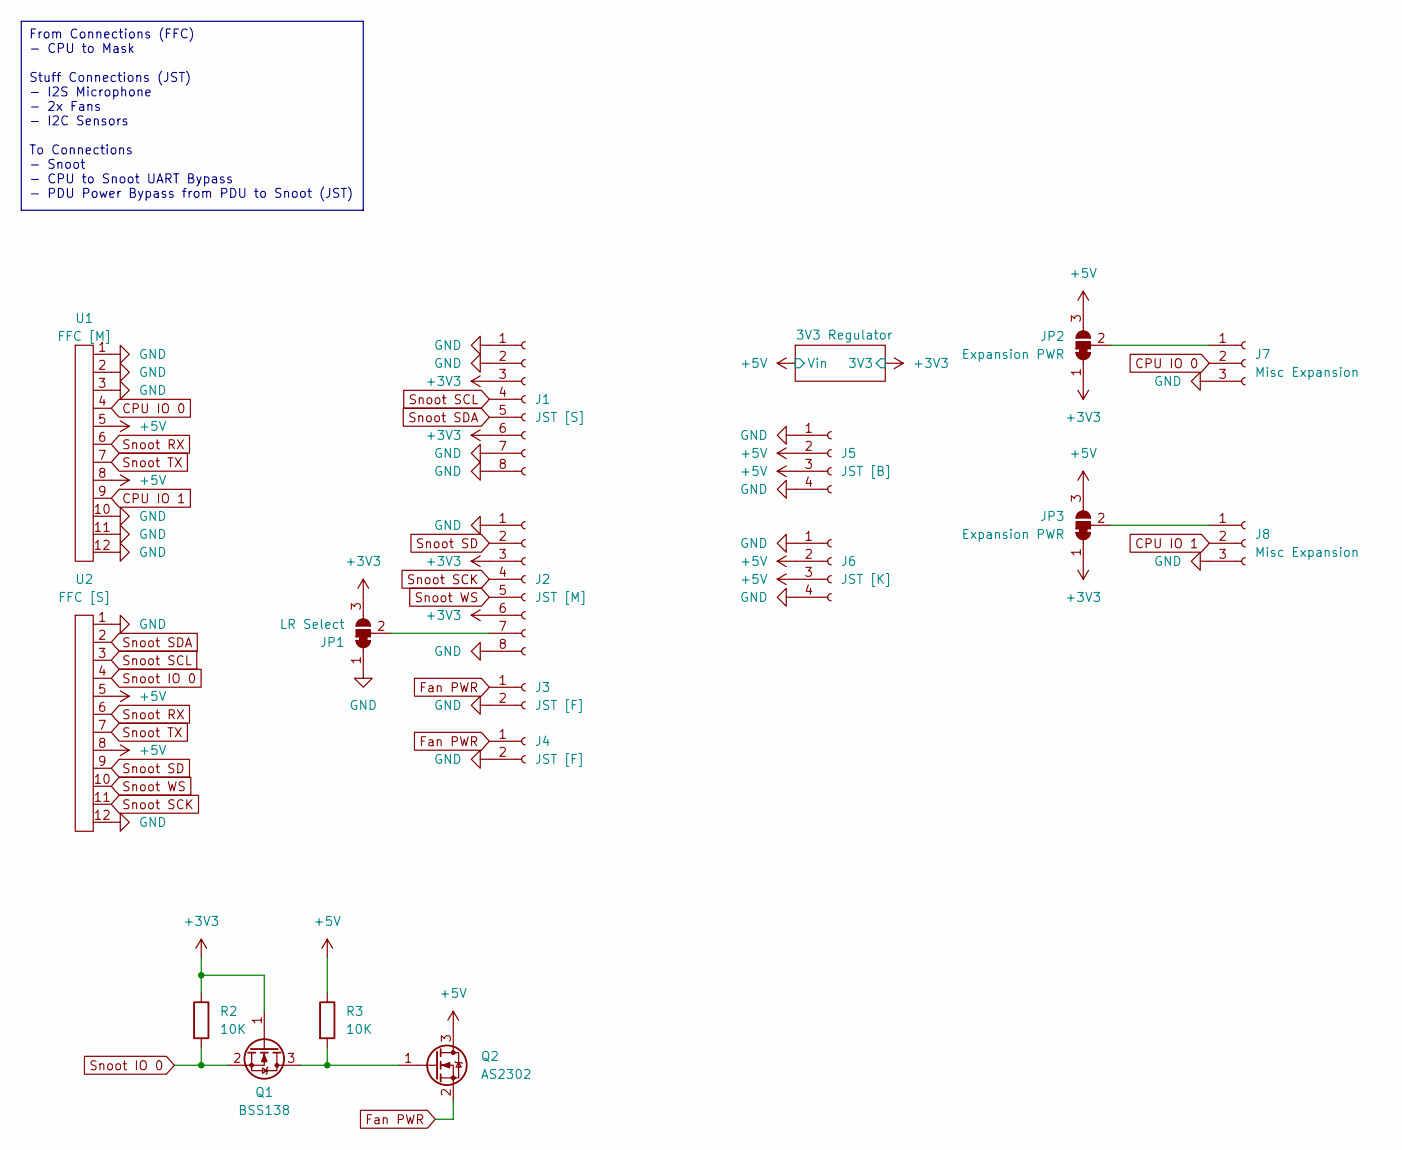
[picture p51: schematic Synth Head Mask.kicad_sch]

Parts:
J1: JST [S]; Molex_PicoBlade_53047-0810_1x08_P1.25mm_Vertical
J2: JST [M]; Molex_PicoBlade_53047-0810_1x08_P1.25mm_Vertical
J3, J4: JST [F]; Molex_PicoBlade_53047-0210_1x02_P1.25mm_Vertical
J5: JST [B]; Molex_PicoBlade_53047-0410_1x04_P1.25mm_Vertical
J6: JST [K]; Molex_PicoBlade_53047-0410_1x04_P1.25mm_Vertical
J7, J8: Misc Expansion; PinHeader_1x03_P2.54mm_Vertical
JP1: LR Select; SolderJumper-3_P1.3mm_Bridged12_RoundedPad1.0x1.5mm
JP2, JP3: Expansion PWR; SolderJumper-3_P1.3mm_Bridged2Bar12_Pad1.0x1.5mm
Q1: BSS138; SOT-23
Q2: AS2302; SOT-23
R2, R3: 10K; R_0603_1608Metric_Pad0.98x0.95mm_HandSolder
U1: FFC [M]; FFC Aliexpress 0.5mm 12P
U2: FFC [S]; FFC Aliexpress 0.5mm 12P

Connections:
+3V3: J1.3, J1.6, J2.3, J2.6, JP1.3 (B), JP2.1 (A), JP3.1 (A), Q1.1 (G), R2.1; also elsewhere on the board
+5V: J5.2, J5.3, J6.2, J6.3, JP2.3 (B), JP3.3 (B), Q2.3 (D), R3.1, U1.5, U1.8, U2.5, U2.8; also elsewhere on the board
CPU IO 0: J7.2, U1.4
CPU IO 1: J8.2, U1.9
Fan PWR: J3.1, J4.1, Q2.2 (S)
GND: J1.1, J1.2, J1.7, J1.8, J2.1, J2.8, J3.2, J4.2, J5.1, J5.4, J6.1, J6.4, J7.3, J8.3, JP1.1 (A), U1.1, U1.2, U1.3, U1.10, U1.11, U1.12, U2.1, U2.12; also elsewhere on the board
unnamed: J2.7, JP1.2 (C)
unnamed: J7.1, JP2.2 (C)
unnamed: J8.1, JP3.2 (C)
unnamed: Q1.3 (D), Q2.1 (G), R3.2
Snoot IO 0: Q1.2 (S), R2.2, U2.4
Snoot RX: U1.6, U2.6
Snoot SCK: J2.4, U2.11
Snoot SCL: J1.4, U2.3
Snoot SD: J2.2, U2.9
Snoot SDA: J1.5, U2.2
Snoot TX: U1.7, U2.7
Snoot WS: J2.5, U2.10

Notes on the sheet:
From Connections (FFC) - CPU to Mask Stuff Connections (JST) - I2S Microphone - 2x Fans - I2C Sensors To Connections - Snoot - CPU to Snoot UART Bypass - PDU Power Bypass from PDU to Snoot (JST)

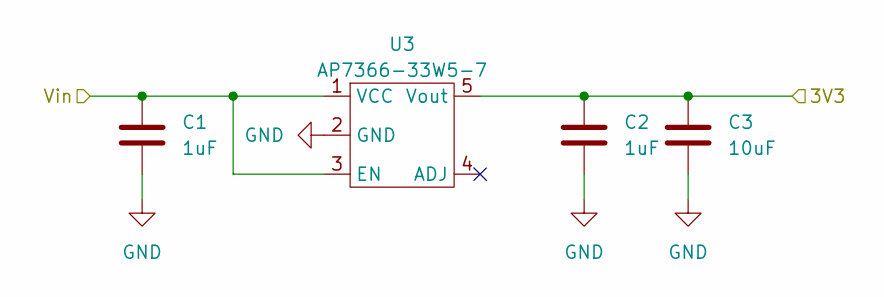
[picture p52: schematic 3V3 Reg.kicad_sch]

Parts:
C1, C2: 1uF; R_0603_1608Metric
C3: 10uF; C_0603_1608Metric
U3: AP7366-33W5-7; AP7366

Connections:
+3V3: C2.1, C3.1, U3.5 (Vout); also elsewhere on the board
+5V: C1.1, U3.1 (VCC), U3.3 (EN); also elsewhere on the board
GND: C1.2, C2.2, C3.2, U3.2 (GND); also elsewhere on the board

Board: 2 copper layers, 21 parts (0 on the bottom side), 18 nets, no tracks yet.
