Cyberspecies/Synth-Head/Embedded/OBSOLETE DESIGNS (DO NOT USE)/Old 0/Synth Head Snoot/Synth Head Snoot.kicad_pcb

## KiCad design Embedded/OBSOLETE DESIGNS (DO NOT USE)/Old 0/Synth Head Snoot/Synth Head Snoot.kicad_pcb (2024-12-26, an earlier design)

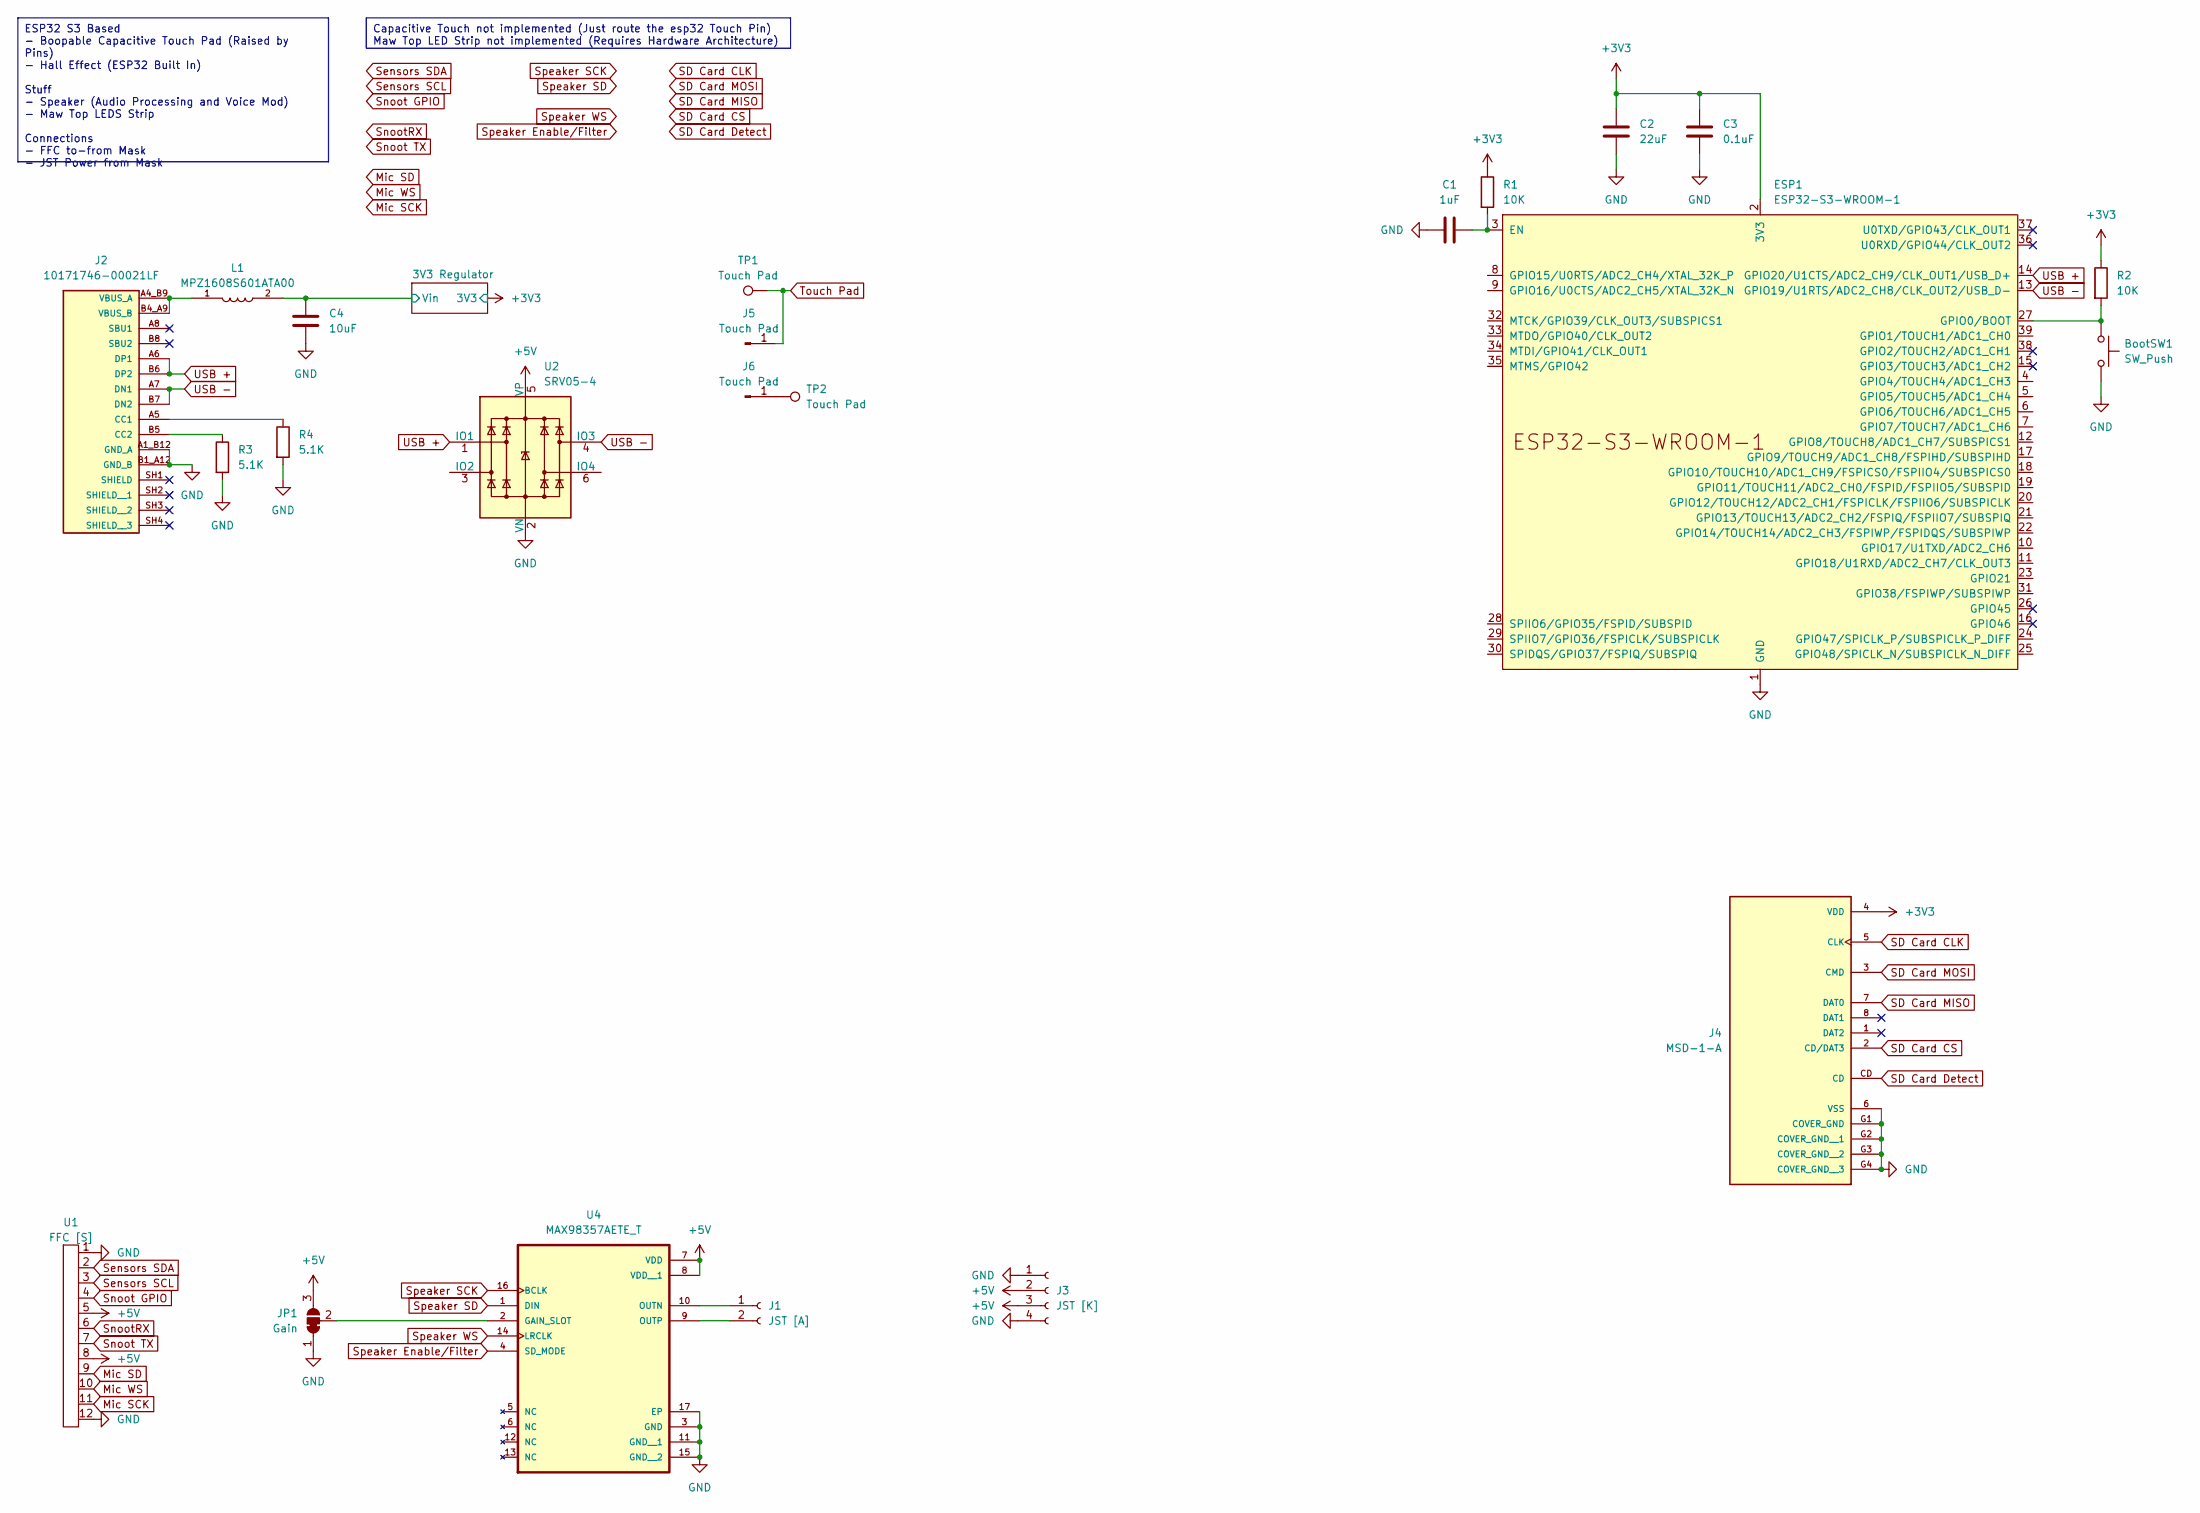
[picture p53: schematic Synth Head Snoot.kicad_sch]

Parts:
BootSW1: SW_Push; Button-R-667843
C1: 1uF; C_0603_1608Metric
C2: 22uF; C_0603_1608Metric_Pad1.08x0.95mm_HandSolder
C3: 0.1uF; C_0603_1608Metric_Pad1.08x0.95mm_HandSolder
C4: 10uF; C_0603_1608Metric
ESP1: ESP32-S3-WROOM-1; ESP32-S3-WROOM-1U
J1: JST [A]; Molex_PicoBlade_53048-0210_1x02_P1.25mm_Horizontal
J2: 10171746-00021LF; AMPHENOL_10171746-00021LF; PARTREV A
J3: JST [K]; Molex_PicoBlade_53048-0410_1x04_P1.25mm_Horizontal
J4: MSD-1-A; CUI_MSD-1-A; PARTREV 1.0
J5, J6: Touch Pad; PinHeader_1x01_P2.54mm_Vertical
JP1: Gain; SolderJumper-3_P1.3mm_Bridged12_Pad1.0x1.5mm_NumberLabels
L1: MPZ1608S601ATA00; INDC1608X95N
R1, R2: 10K; R_0603_1608Metric
R3, R4: 5.1K; R_0603_1608Metric
TP1, TP2: Touch Pad; TestPoint_Pad_D2.0mm
U1: FFC [S]; FFC Aliexpress 0.5mm 12P
U2: SRV05-4; SOT-23-6
U4: MAX98357AETE_T; QFN50P300X300X80-17N

Connections:
+3V3: C2.1, C3.1, ESP1.2 (3V3), J4.4 (VDD), R1.1, R2.1; also elsewhere on the board
+5V: J3.2, J3.3, JP1.3 (B), U1.5, U1.8, U2.5 (VP), U4.7 (VDD), U4.8 (VDD__1)
/3V3 Regulator/Vin: C4.1, L1.2; also elsewhere on the board
GND: BootSW1.2, C1.1, C2.2, C3.2, C4.2, ESP1.1 (GND), ESP1.40 (GND), ESP1.41 (GND), J2.A1_B12 (GND_A), J2.B1_A12 (GND_B), J3.1, J3.4, J4.6 (VSS), J4.G1 (COVER_GND), J4.G2 (COVER_GND__1), J4.G3 (COVER_GND__2), J4.G4 (COVER_GND__3), JP1.1 (A), R3.2, R4.2, U1.1, U1.12, U2.2 (VN), U4.3 (GND), U4.11 (GND__1), U4.15 (GND__2), U4.17 (EP); also elsewhere on the board
Mic SCK: U1.11
Mic SD: U1.9
Mic WS: U1.10
unnamed: C1.2, ESP1.3 (EN), R1.2
unnamed: BootSW1.1, ESP1.27 (GPIO0/BOOT), R2.2
unnamed: J1.1, U4.10 (OUTN)
unnamed: J1.2, U4.9 (OUTP)
unnamed: J2.A5 (CC1), R4.1
unnamed: J2.B5 (CC2), R3.1
unnamed: J2.A4_B9 (VBUS_A), J2.B4_A9 (VBUS_B), L1.1
unnamed: J6.1, TP2.1
unnamed: JP1.2 (C), U4.2 (GAIN_SLOT)
SD Card CLK: J4.5 (CLK)
SD Card CS: J4.2 (CD/DAT3)
SD Card Detect: J4.CD
SD Card MISO: J4.7 (DAT0)
SD Card MOSI: J4.3 (CMD)
Sensors SCL: U1.3
Sensors SDA: U1.2
Snoot GPIO: U1.4
Snoot TX: U1.7
SnootRX: U1.6
Speaker Enable/Filter: U4.4 (SD_MODE)
Speaker SCK: U4.16 (BCLK)
Speaker SD: U4.1 (DIN)
Speaker WS: U4.14 (LRCLK)
Touch Pad: J5.1, TP1.1
USB +: ESP1.14 (GPIO20/U1CTS/ADC2_CH9/CLK_OUT1/USB_D+), J2.A6 (DP1), J2.B6 (DP2), U2.1 (IO1)
USB -: ESP1.13 (GPIO19/U1RTS/ADC2_CH8/CLK_OUT2/USB_D-), J2.A7 (DN1), J2.B7 (DN2), U2.4 (IO3)

Notes on the sheet:
Capacitive Touch not implemented (Just route the esp32 Touch Pin) Maw Top LED Strip not implemented (Requires Hardware Architecture)
ESP32 S3 Based - Boopable Capacitive Touch Pad (Raised by Pins) - Hall Effect (ESP32 Built In) Stuff - Speaker (Audio Processing and Voice Mod) - Maw Top LEDS Strip Connections - FFC to-from Mask - JST Power from Mask

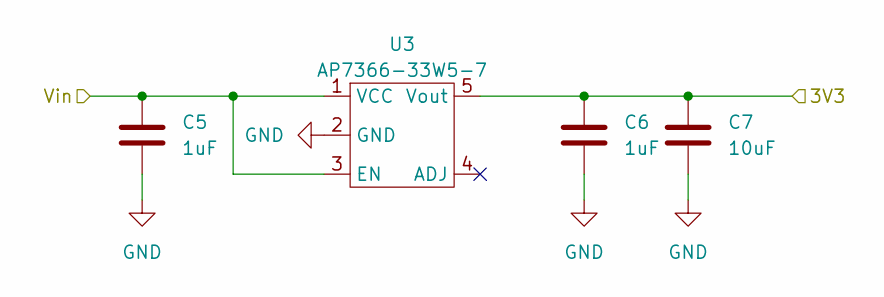
[picture p54: schematic 3V3 Reg.kicad_sch]

Parts:
C5, C6: 1uF; R_0603_1608Metric
C7: 10uF; C_0603_1608Metric
U3: AP7366-33W5-7; AP7366

Connections:
+3V3: C6.1, C7.1, U3.5 (Vout); also elsewhere on the board
/3V3 Regulator/Vin: C5.1, U3.1 (VCC), U3.3 (EN); also elsewhere on the board
GND: C5.2, C6.2, C7.2, U3.2 (GND); also elsewhere on the board

Board: 2 copper layers, 27 parts (3 on the bottom side), 16 nets, no tracks yet.
