Cyberspecies/Synth-Head/Embedded/OBSOLETE DESIGNS (DO NOT USE)/Old 0/Synth Head PDU/Synth Head PDU.kicad_pcb

## KiCad design Embedded/OBSOLETE DESIGNS (DO NOT USE)/Old 0/Synth Head PDU/Synth Head PDU.kicad_pcb (2024-12-26, an earlier design)

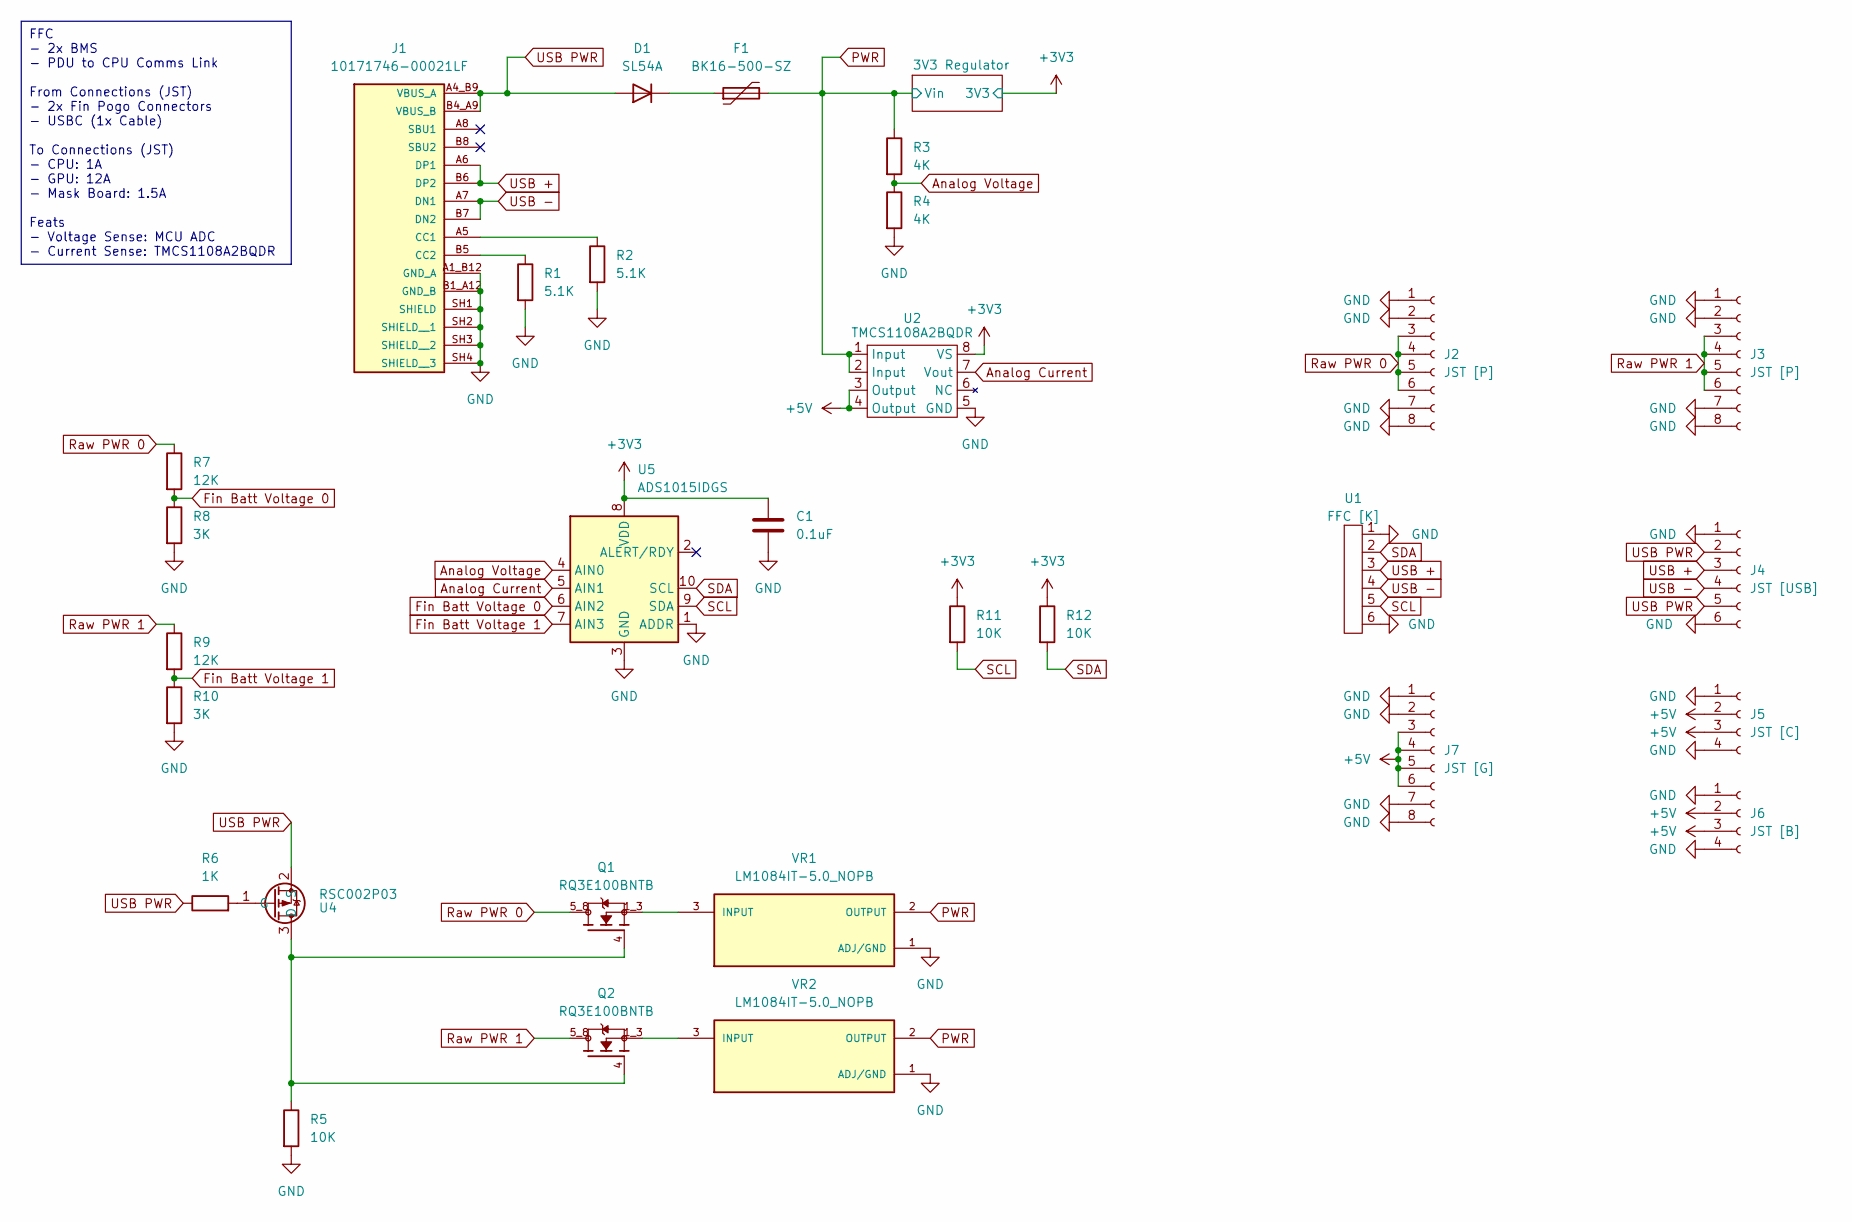
[picture p55: schematic Synth Head PDU.kicad_sch]

Parts:
C1: 0.1uF; C_0603_1608Metric_Pad1.08x0.95mm_HandSolder
D1: SL54A; D_SMA-SMB_Universal_Handsoldering
F1: BK16-500-SZ; Fuse_Bourns_MF-RHT500
J1: 10171746-00021LF; AMPHENOL_10171746-00021LF; PARTREV A
J2, J3: JST [P]; PinHeader_1x08_P2.54mm_Vertical
J4: JST [USB]; PinHeader_1x06_P1.27mm_Vertical
J5: JST [C]; Molex_PicoBlade_53048-0410_1x04_P1.25mm_Horizontal
J6: JST [B]; Molex_PicoBlade_53048-0410_1x04_P1.25mm_Horizontal
J7: JST [G]; PinHeader_1x08_P2.54mm_Vertical
Q1, Q2: RQ3E100BNTB; TRANS_RQ3E100BNTB; PARTREV B
R1, R2: 5.1K; R_0603_1608Metric
R3, R4: 4K; R_0603_1608Metric_Pad0.98x0.95mm_HandSolder
R5: 10K; R_0603_1608Metric
R6: 1K; R_0603_1608Metric_Pad0.98x0.95mm_HandSolder
R7, R9: 12K; C_0603_1608Metric_Pad1.08x0.95mm_HandSolder
R8, R10: 3K; C_0603_1608Metric_Pad1.08x0.95mm_HandSolder
R11, R12: 10K; R_0603_1608Metric_Pad0.98x0.95mm_HandSolder
U1: FFC [K]; FFC Aliexpress 0.5mm 6P
U2: TMCS1108A2BQDR; SOIC-8_3.9x4.9mm_P1.27mm
U4: RSC002P03
U5: ADS1015IDGS; TSSOP-10_3x3mm_P0.5mm
VR1, VR2: LM1084IT-5.0_NOPB; TO254P1054X470X1955-3; PARTREV G

Connections:
+3V3: C1.1, R11.1, R12.1, U2.8 (VS), U5.8 (VDD); also elsewhere on the board
+5V: J5.2, J5.3, J6.2, J6.3, J7.3, J7.4, J7.5, J7.6, U2.3 (Output), U2.4 (Output)
Analog Current: U2.7 (Vout), U5.5 (AIN1)
Analog Voltage: R3.2, R4.1, U5.4 (AIN0)
Fin Batt Voltage 0: R7.2, R8.1, U5.6 (AIN2)
Fin Batt Voltage 1: R9.2, R10.1, U5.7 (AIN3)
GND: C1.2, J1.A1_B12 (GND_A), J1.B1_A12 (GND_B), J1.SH1 (SHIELD), J1.SH2 (SHIELD__1), J1.SH3 (SHIELD__2), J1.SH4 (SHIELD__3), J2.1, J2.2, J2.7, J2.8, J3.1, J3.2, J3.7, J3.8, J4.1, J4.6, J5.1, J5.4, J6.1, J6.4, J7.1, J7.2, J7.7, J7.8, R1.2, R2.2, R4.2, R5.2, R8.2, R10.2, U1.1, U1.6, U2.5 (GND), U5.1 (ADDR), U5.3 (GND), VR1.1 (ADJ/GND), VR2.1 (ADJ/GND); also elsewhere on the board
unnamed: D1.1 (K), F1.1
unnamed: J1.A5 (CC1), R2.1
unnamed: J1.B5 (CC2), R1.1
unnamed: Q1.4, Q2.4, R5.1, U4.3 (D)
unnamed: R6.2, U4.1 (G)
unnamed: Q1.1_3, VR1.3 (INPUT)
unnamed: Q2.1_3, VR2.3 (INPUT)
PWR: F1.2, R3.1, U2.1 (Input), U2.2 (Input), VR1.2 (OUTPUT), VR2.2 (OUTPUT); also elsewhere on the board
Raw PWR 0: J2.3, J2.4, J2.5, J2.6, Q1.5_8, R7.1
Raw PWR 1: J3.3, J3.4, J3.5, J3.6, Q2.5_8, R9.1
SCL: R11.2, U1.5, U5.9 (SDA)
SDA: R12.2, U1.2, U5.10 (SCL)
USB +: J1.A6 (DP1), J1.B6 (DP2), J4.3, U1.3
USB -: J1.A7 (DN1), J1.B7 (DN2), J4.4, U1.4
USB PWR: D1.2 (A), J1.A4_B9 (VBUS_A), J1.B4_A9 (VBUS_B), J4.2, J4.5, R6.1, U4.2 (S)

Notes on the sheet:
FFC - 2x BMS - PDU to CPU Comms Link From Connections (JST) - 2x Fin Pogo Connectors - USBC (1x Cable) To Connections (JST) - CPU: 1A - GPU: 12A - Mask Board: 1.5A Feats - Voltage Sense: MCU ADC - Current Sense: TMCS1108A2BQDR

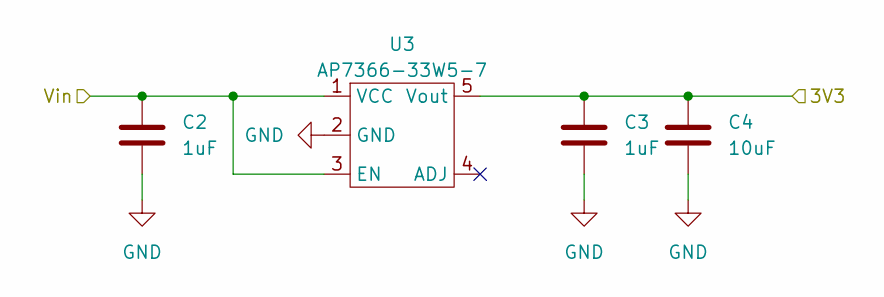
[picture p56: schematic 3V3 Reg.kicad_sch]

Parts:
C2, C3: 1uF; R_0603_1608Metric
C4: 10uF; C_0603_1608Metric
U3: AP7366-33W5-7; AP7366

Connections:
+3V3: C3.1, C4.1, U3.5 (Vout); also elsewhere on the board
GND: C2.2, C3.2, C4.2, U3.2 (GND); also elsewhere on the board
PWR: C2.1, U3.1 (VCC), U3.3 (EN); also elsewhere on the board

Board: 2 copper layers, 34 parts (4 on the bottom side), 22 nets, no tracks yet.
