Cyberspecies/Synth-Head/Embedded/OBSOLETE DESIGNS (DO NOT USE)/Old 0/Synth Head CPU/Synth Head CPU.kicad_pcb

## KiCad design Embedded/OBSOLETE DESIGNS (DO NOT USE)/Old 0/Synth Head CPU/Synth Head CPU.kicad_pcb (2024-12-26, an earlier design)

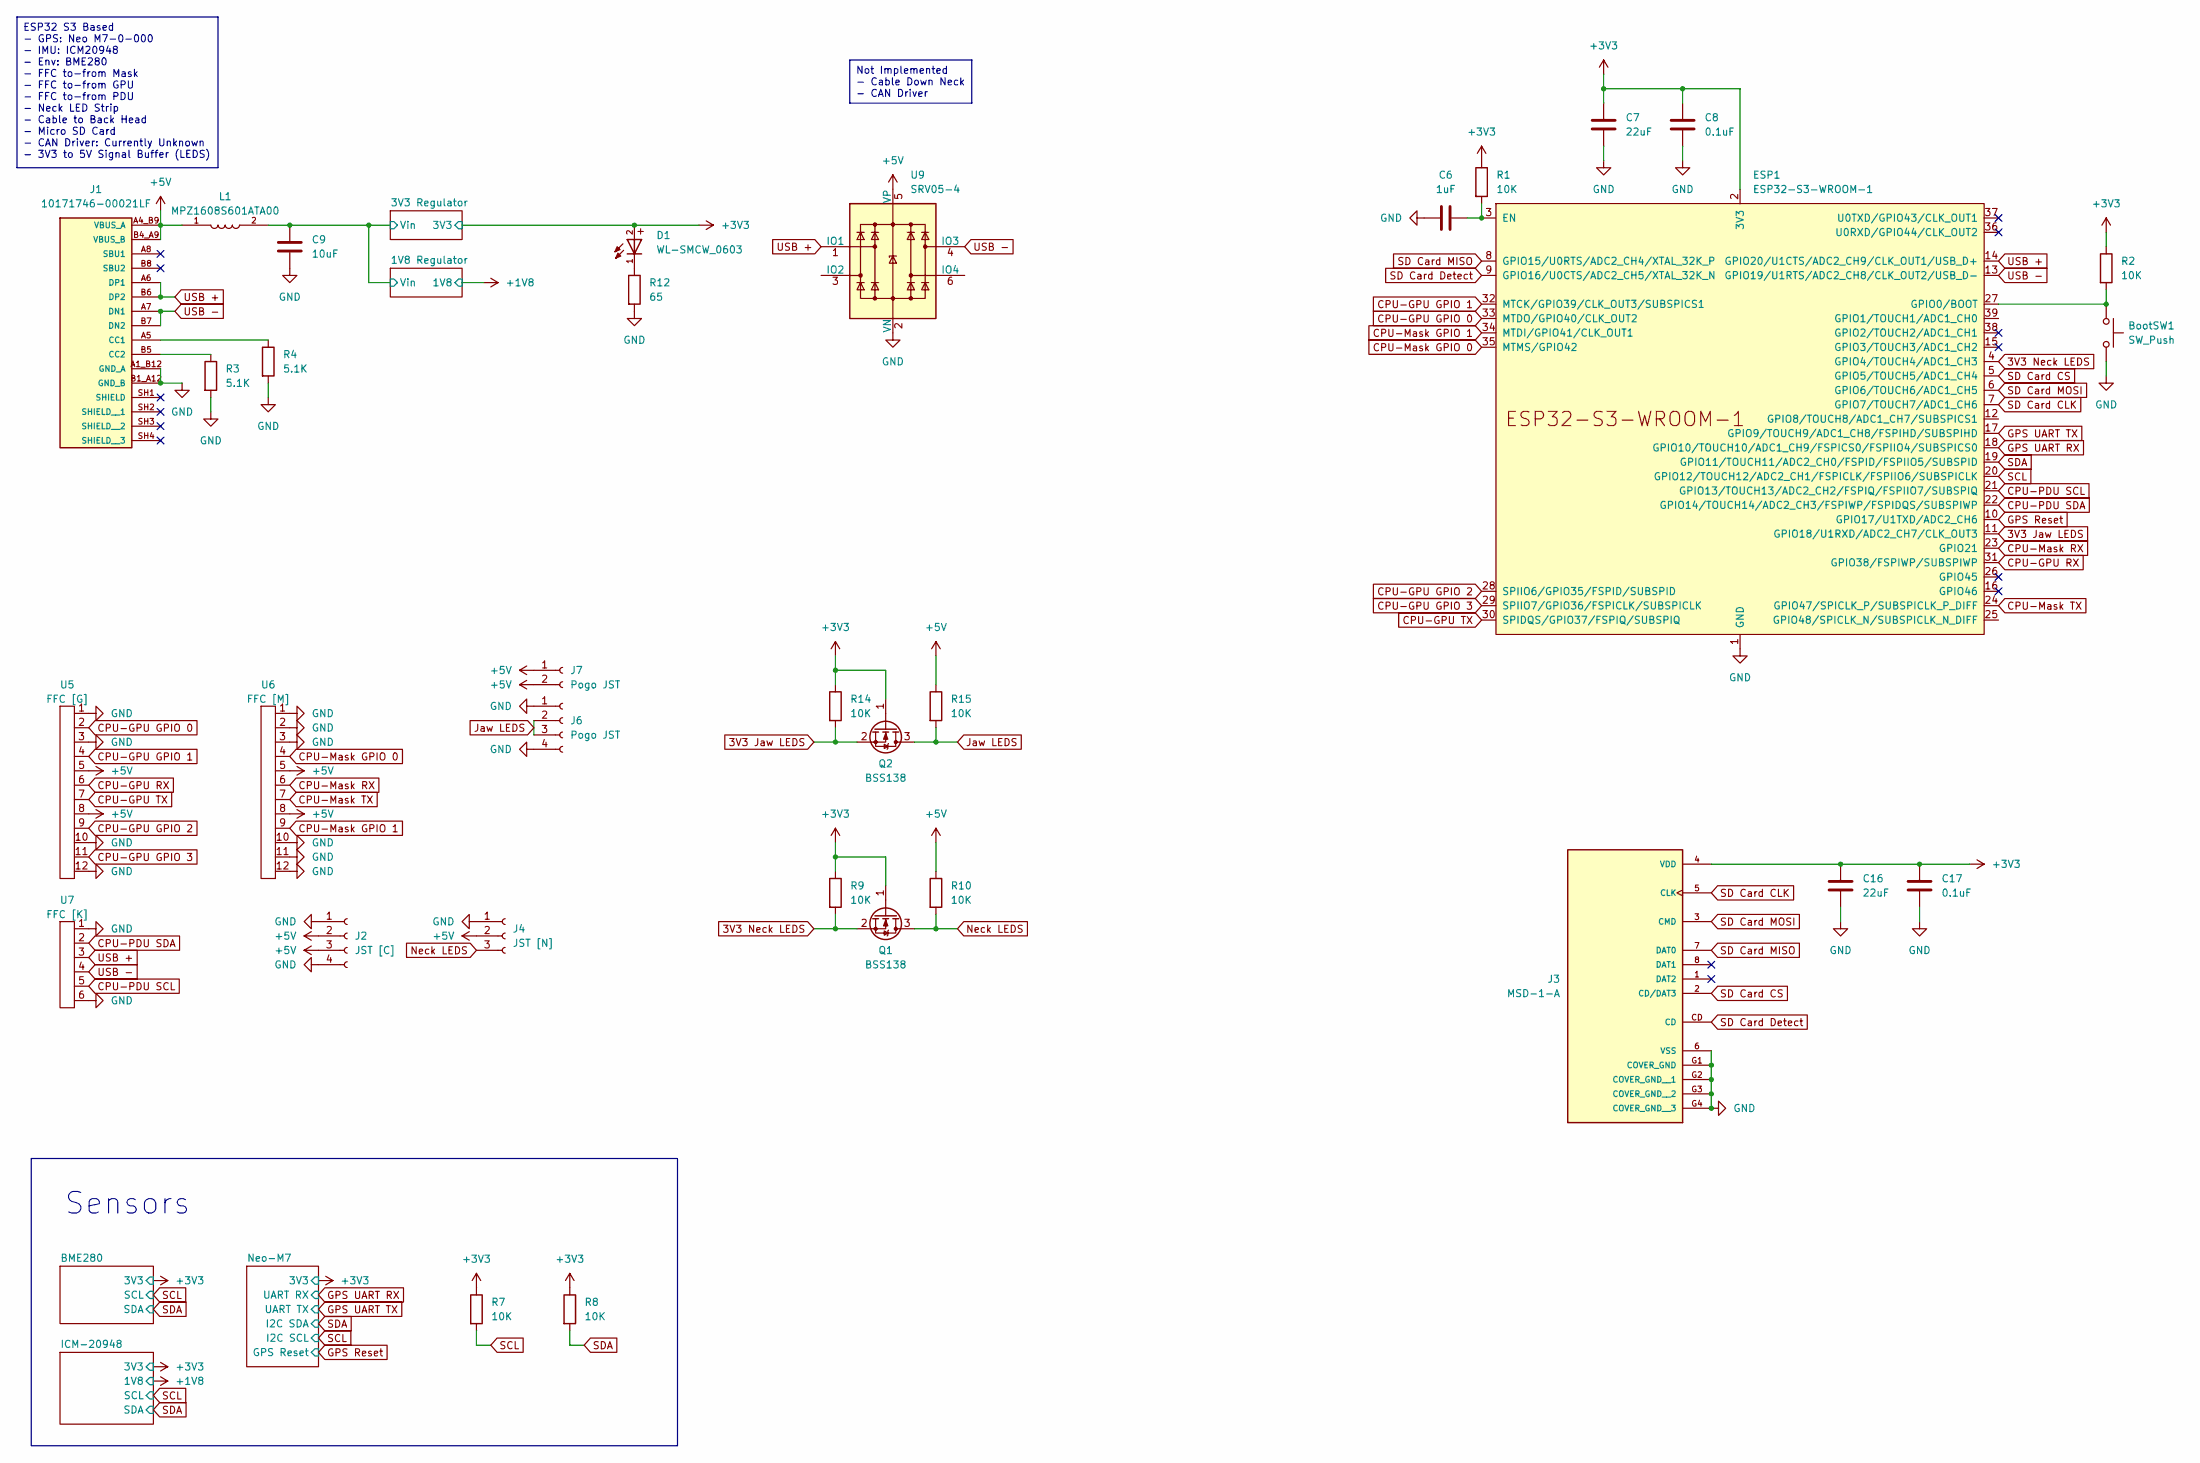
[picture p57: schematic Synth Head CPU.kicad_sch]

Parts:
BootSW1: SW_Push; Button-R-667843
C6: 1uF; C_0603_1608Metric
C7, C16: 22uF; C_0603_1608Metric_Pad1.08x0.95mm_HandSolder
C8, C17: 0.1uF; C_0603_1608Metric_Pad1.08x0.95mm_HandSolder
C9: 10uF; C_0603_1608Metric
D1: WL-SMCW_0603
ESP1: ESP32-S3-WROOM-1
J1: 10171746-00021LF; AMPHENOL_10171746-00021LF; PARTREV A
J2: JST [C]; Molex_PicoBlade_53048-0410_1x04_P1.25mm_Horizontal
J3: MSD-1-A; CUI_MSD-1-A; PARTREV 1.0
J4: JST [N]; Molex_PicoBlade_53048-0310_1x03_P1.25mm_Horizontal
J6: Pogo JST; Molex_PicoBlade_53048-0410_1x04_P1.25mm_Horizontal
J7: Pogo JST; Molex_PicoBlade_53048-0210_1x02_P1.25mm_Horizontal
L1: MPZ1608S601ATA00; INDC1608X95N
Q1, Q2: BSS138; SOT-23
R1, R2: 10K; R_0603_1608Metric
R3, R4: 5.1K; R_0603_1608Metric
R7, R8, R9, R10, R14, R15: 10K; R_0603_1608Metric_Pad0.98x0.95mm_HandSolder
R12: 65; R_0603_1608Metric_Pad0.98x0.95mm_HandSolder
U5: FFC [G]; FFC Aliexpress 0.5mm 12P
U6: FFC [M]; FFC Aliexpress 0.5mm 12P
U7: FFC [K]; FFC Aliexpress 0.5mm 6P
U9: SRV05-4; SOT-23-6

Connections:
3V3 Jaw LEDS: ESP1.11 (GPIO18/U1RXD/ADC2_CH7/CLK_OUT3), Q2.2 (S), R14.2
3V3 Neck LEDS: ESP1.4 (GPIO4/TOUCH4/ADC1_CH3), Q1.2 (S), R9.2
+3V3: C7.1, C8.1, C16.1, C17.1, D1.2, ESP1.2 (3V3), J3.4 (VDD), Q1.1 (G), Q2.1 (G), R1.1, R2.1, R7.1, R8.1, R9.1, R14.1; also elsewhere on the board
+5V: J1.A4_B9 (VBUS_A), J1.B4_A9 (VBUS_B), J2.2, J2.3, J4.2, J7.1, J7.2, L1.1, R10.1, R15.1, U5.5, U5.8, U6.5, U6.8, U9.5 (VP)
/1V8 Regulator/Vin: C9.1, L1.2; also elsewhere on the board
CPU-GPU GPIO 0: ESP1.33 (MTDO/GPIO40/CLK_OUT2), U5.2
CPU-GPU GPIO 1: ESP1.32 (MTCK/GPIO39/CLK_OUT3/SUBSPICS1), U5.4
CPU-GPU GPIO 2: ESP1.28 (SPIIO6/GPIO35/FSPID/SUBSPID), U5.9
CPU-GPU GPIO 3: ESP1.29 (SPIIO7/GPIO36/FSPICLK/SUBSPICLK), U5.11
CPU-GPU RX: ESP1.31 (GPIO38/FSPIWP/SUBSPIWP), U5.6
CPU-GPU TX: ESP1.30 (SPIDQS/GPIO37/FSPIQ/SUBSPIQ), U5.7
CPU-Mask GPIO 0: ESP1.35 (MTMS/GPIO42), U6.4
CPU-Mask GPIO 1: ESP1.34 (MTDI/GPIO41/CLK_OUT1), U6.9
CPU-Mask RX: ESP1.23 (GPIO21), U6.6
CPU-Mask TX: ESP1.24 (GPIO47/SPICLK_P/SUBSPICLK_P_DIFF), U6.7
CPU-PDU SCL: ESP1.21 (GPIO13/TOUCH13/ADC2_CH2/FSPIQ/FSPIIO7/S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), U7.5
CPU-PDU SDA: ESP1.22 (GPIO14/TOUCH14/ADC2_CH3/FSPIWP/FSPIDQS/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), U7.2
GND: BootSW1.2, C6.1, C7.2, C8.2, C9.2, C16.2, C17.2, ESP1.1 (GND), ESP1.40 (GND), ESP1.41 (GND), J1.A1_B12 (GND_A), J1.B1_A12 (GND_B), J2.1, J2.4, J3.6 (VSS), J3.G1 (COVER_GND), J3.G2 (COVER_GND__1), J3.G3 (COVER_GND__2), J3.G4 (COVER_GND__3), J4.1, J6.1, J6.4, R3.2, R4.2, R12.2, U5.1, U5.3, U5.10, U5.12, U6.1, U6.2, U6.3, U6.10, U6.11, U6.12, U7.1, U7.6, U9.2 (VN); also elsewhere on the board
GPS Reset: ESP1.10 (GPIO17/U1TXD/ADC2_CH6); also elsewhere on the board
GPS UART RX: ESP1.18 (GPIO10/TOUCH10/ADC1_CH9/FSPICS0/FSPIIO4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); also elsewhere on the board
GPS UART TX: ESP1.17 (GPIO9/TOUCH9/ADC1_CH8/FSPIHD/SUBSPIHD); also elsewhere on the board
Jaw LEDS: J6.2, J6.3, Q2.3 (D), R15.2
Neck LEDS: J4.3, Q1.3 (D), R10.2
unnamed: D1.1, R12.1
unnamed: C6.2, ESP1.3 (EN), R1.2
unnamed: BootSW1.1, ESP1.27 (GPIO0/BOOT), R2.2
unnamed: J1.A5 (CC1), R4.1
unnamed: J1.B5 (CC2), R3.1
SCL: ESP1.20 (GPIO12/TOUCH12/ADC2_CH1/FSPICLK/FSPIIO6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), R7.2; also elsewhere on the board
SD Card CLK: ESP1.7 (GPIO7/TOUCH7/ADC1_CH6), J3.5 (CLK)
SD Card CS: ESP1.5 (GPIO5/TOUCH5/ADC1_CH4), J3.2 (CD/DAT3)
SD Card Detect: ESP1.9 (GPIO16/U0CTS/ADC2_CH5/XTAL_32K_N), J3.CD
SD Card MISO: ESP1.8 (GPIO15/U0RTS/ADC2_CH4/XTAL_32K_P), J3.7 (DAT0)
SD Card MOSI: ESP1.6 (GPIO6/TOUCH6/ADC1_CH5), J3.3 (CMD)
SDA: ESP1.19 (GPIO11/TOUCH11/ADC2_CH0/FSPID/FSPIIO5/S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), R8.2; also elsewhere on the board
USB +: ESP1.14 (GPIO20/U1CTS/ADC2_CH9/CLK_OUT1/USB_D+), J1.A6 (DP1), J1.B6 (DP2), U7.3, U9.1 (IO1)
USB -: ESP1.13 (GPIO19/U1RTS/ADC2_CH8/CLK_OUT2/USB_D-), J1.A7 (DN1), J1.B7 (DN2), U7.4, U9.4 (IO3)

Notes on the sheet:
Not Implemented - Cable Down Neck - CAN Driver
ESP32 S3 Based - GPS: Neo M7-0-000 - IMU: ICM20948 - Env: BME280 - FFC to-from Mask - FFC to-from GPU - FFC to-from PDU - Neck LED Strip - Cable to Back Head - Micro SD Card - CAN Driver: Currently Unknown - 3V3 to 5V Signal Buffer (LEDS)
Sensors

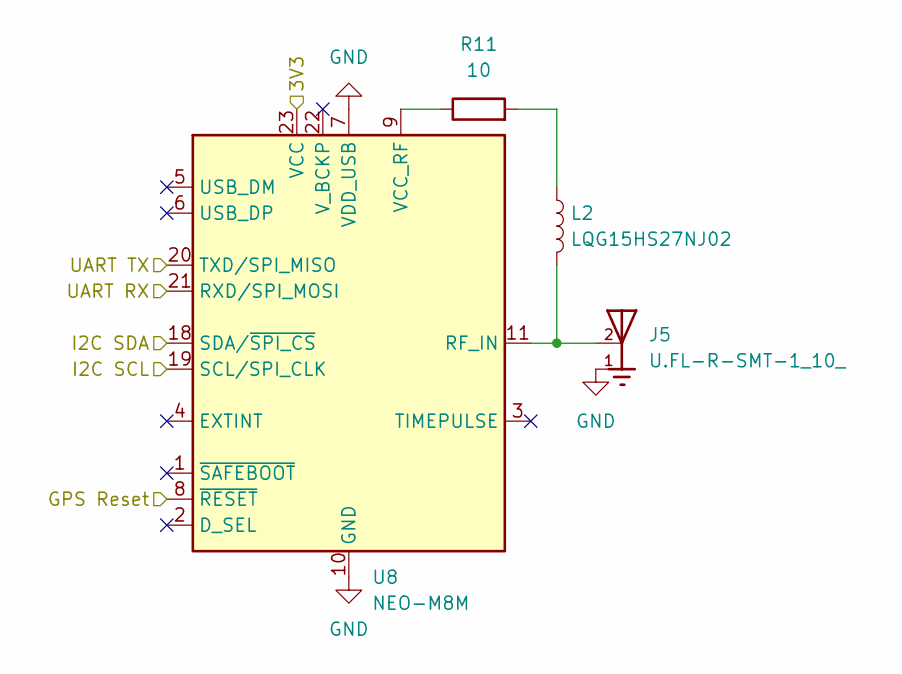
[picture p58: schematic Neo-M7.kicad_sch]

Parts:
J5: U.FL-R-SMT-1_10_; HRS_U.FL-R-SMT-1_10_
L2: LQG15HS27NJ02; L_0402_1005Metric_Pad0.77x0.64mm_HandSolder
R11: 10; C_0603_1608Metric_Pad1.08x0.95mm_HandSolder
U8: NEO-M8M; ublox_NEO

Connections:
+3V3: U8.23 (VCC); also elsewhere on the board
GND: J5.1, U8.7 (VDD_USB), U8.10 (GND), U8.12 (GND), U8.13 (GND), U8.24 (GND); also elsewhere on the board
GPS Reset: U8.8 (~RESET); also elsewhere on the board
GPS UART RX: U8.21 (RXD/SPI_MOSI); also elsewhere on the board
GPS UART TX: U8.20 (TXD/SPI_MISO); also elsewhere on the board
unnamed: L2.1, R11.2
unnamed: J5.2, L2.2, U8.11 (RF_IN)
unnamed: R11.1, U8.9 (VCC_RF)
SCL: U8.19 (SCL/SPI_CLK); also elsewhere on the board
SDA: U8.18 (SDA/~SPI_CS); also elsewhere on the board

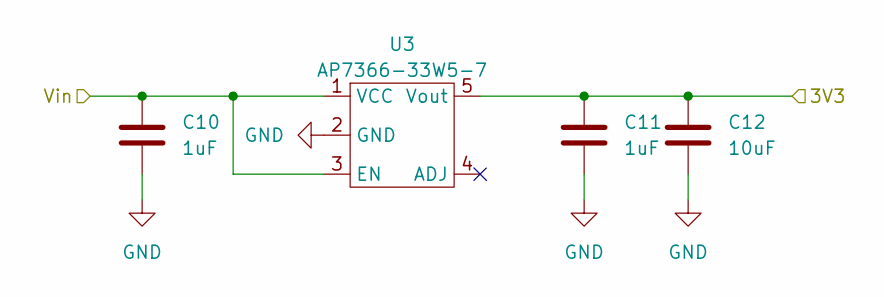
[picture p59: schematic 3V3 Reg.kicad_sch]

Parts:
C10, C11: 1uF; R_0603_1608Metric
C12: 10uF; C_0603_1608Metric
U3: AP7366-33W5-7; AP7366

Connections:
+3V3: C11.1, C12.1, U3.5 (Vout); also elsewhere on the board
/1V8 Regulator/Vin: C10.1, U3.1 (VCC), U3.3 (EN); also elsewhere on the board
GND: C10.2, C11.2, C12.2, U3.2 (GND); also elsewhere on the board

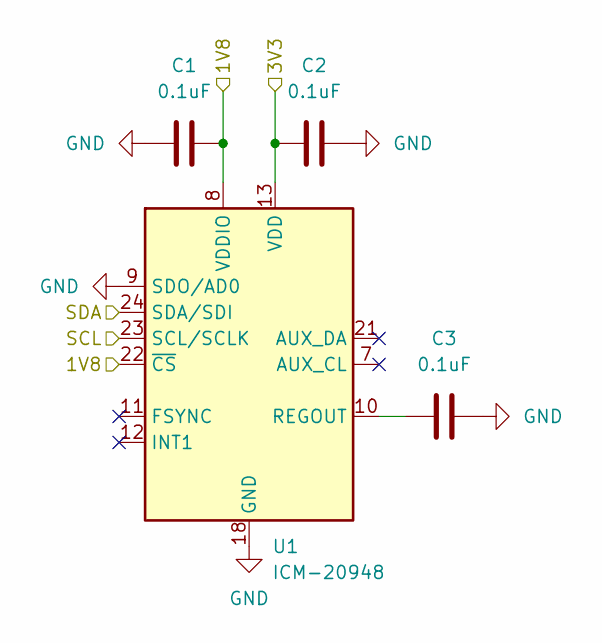
[picture p60: schematic ICM20948.kicad_sch]

Parts:
C1, C2, C3: 0.1uF; C_0603_1608Metric_Pad1.08x0.95mm_HandSolder
U1: ICM-20948; InvenSense_QFN-24_3x3mm_P0.4mm

Connections:
+1V8: C1.2, U1.8 (VDDIO), U1.22 (~CS); also elsewhere on the board
+3V3: C2.1, U1.13 (VDD); also elsewhere on the board
GND: C1.1, C2.2, C3.2, U1.9 (SDO/AD0), U1.18 (GND), U1.20 (GND); also elsewhere on the board
unnamed: C3.1, U1.10 (REGOUT)
SCL: U1.23 (SCL/SCLK); also elsewhere on the board
SDA: U1.24 (SDA/SDI); also elsewhere on the board

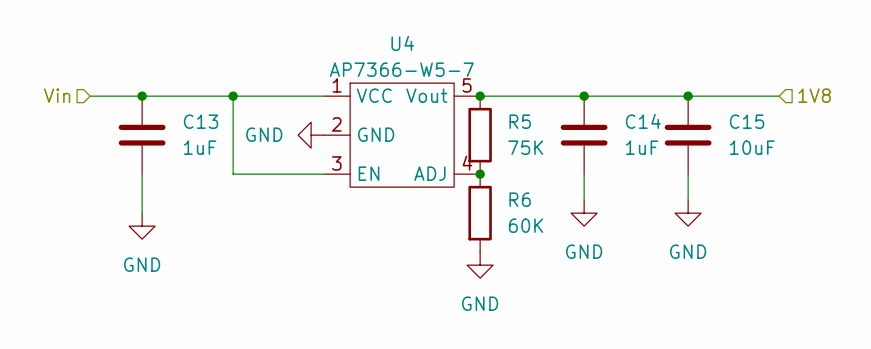
[picture p61: schematic 1V8 Reg.kicad_sch]

Parts:
C13, C14: 1uF; R_0603_1608Metric
C15: 10uF; C_0603_1608Metric
R5: 75K; R_0603_1608Metric
R6: 60K; R_0603_1608Metric
U4: AP7366-W5-7; AP7366

Connections:
+1V8: C14.1, C15.1, R5.1, U4.5 (Vout); also elsewhere on the board
/1V8 Regulator/Vin: C13.1, U4.1 (VCC), U4.3 (EN); also elsewhere on the board
GND: C13.2, C14.2, C15.2, R6.2, U4.2 (GND); also elsewhere on the board
unnamed: R5.2, R6.1, U4.4 (ADJ)

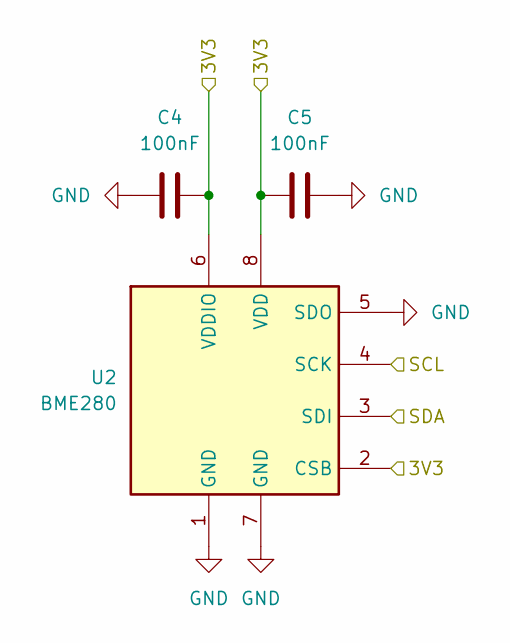
[picture p62: schematic BME280.kicad_sch]

Parts:
C4, C5: 100nF; C_0603_1608Metric_Pad1.08x0.95mm_HandSolder
U2: BME280; Bosch_LGA-8_2.5x2.5mm_P0.65mm_ClockwisePinNumbering

Connections:
+3V3: C4.2, C5.1, U2.2 (CSB), U2.6 (VDDIO), U2.8 (VDD); also elsewhere on the board
GND: C4.1, C5.2, U2.1 (GND), U2.5 (SDO), U2.7 (GND); also elsewhere on the board
SCL: U2.4 (SCK); also elsewhere on the board
SDA: U2.3 (SDI); also elsewhere on the board

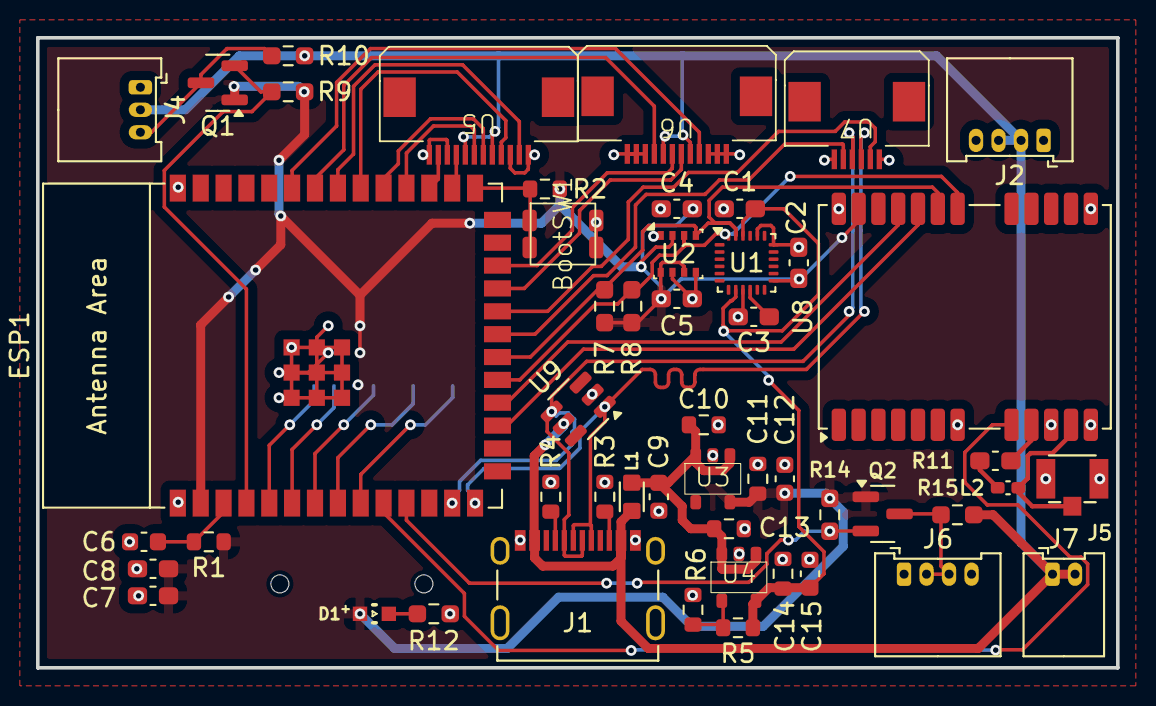
[picture p63: board Synth Head CPU.kicad_pcb from above]

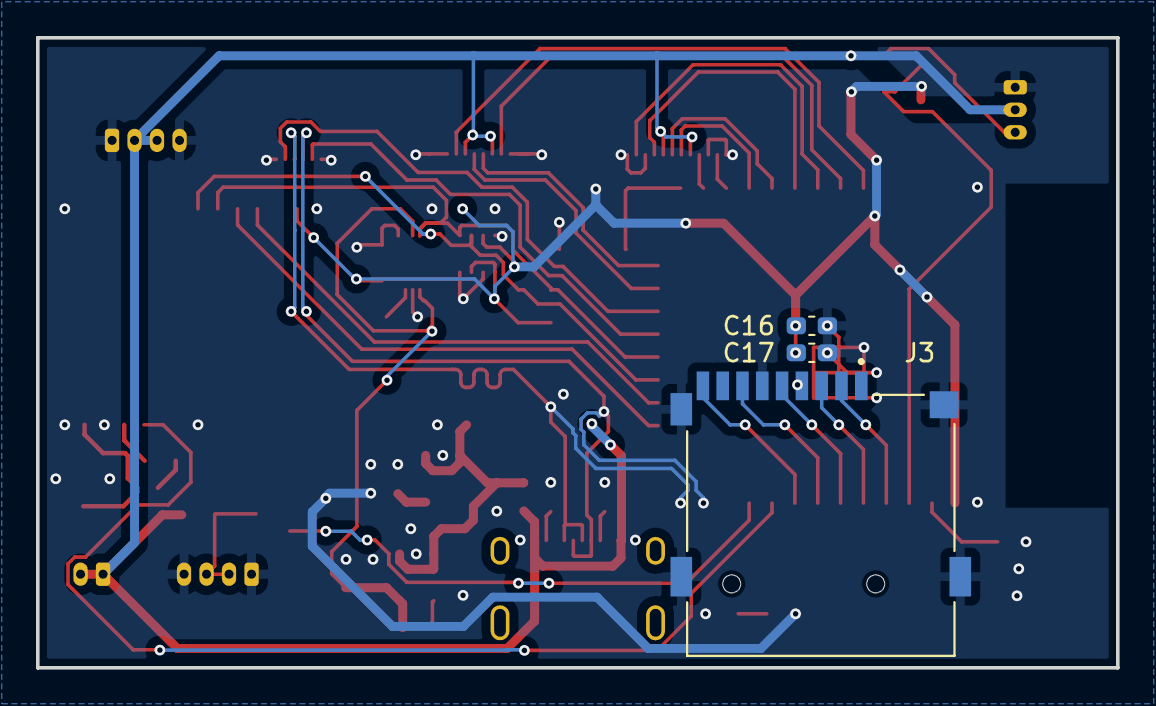
[picture p64: board Synth Head CPU.kicad_pcb from below]

Board: 2 copper layers, 60.0 x 35.0 mm, 54 parts (3 on the bottom side), 43 nets.
