Cyberspecies/Synth-Head/Embedded/OBSOLETE DESIGNS (DO NOT USE)/Old 0/Synth Head GPU/Synth Head GPU.kicad_pcb

## KiCad design Embedded/OBSOLETE DESIGNS (DO NOT USE)/Old 0/Synth Head GPU/Synth Head GPU.kicad_pcb (2024-12-26, an earlier design)

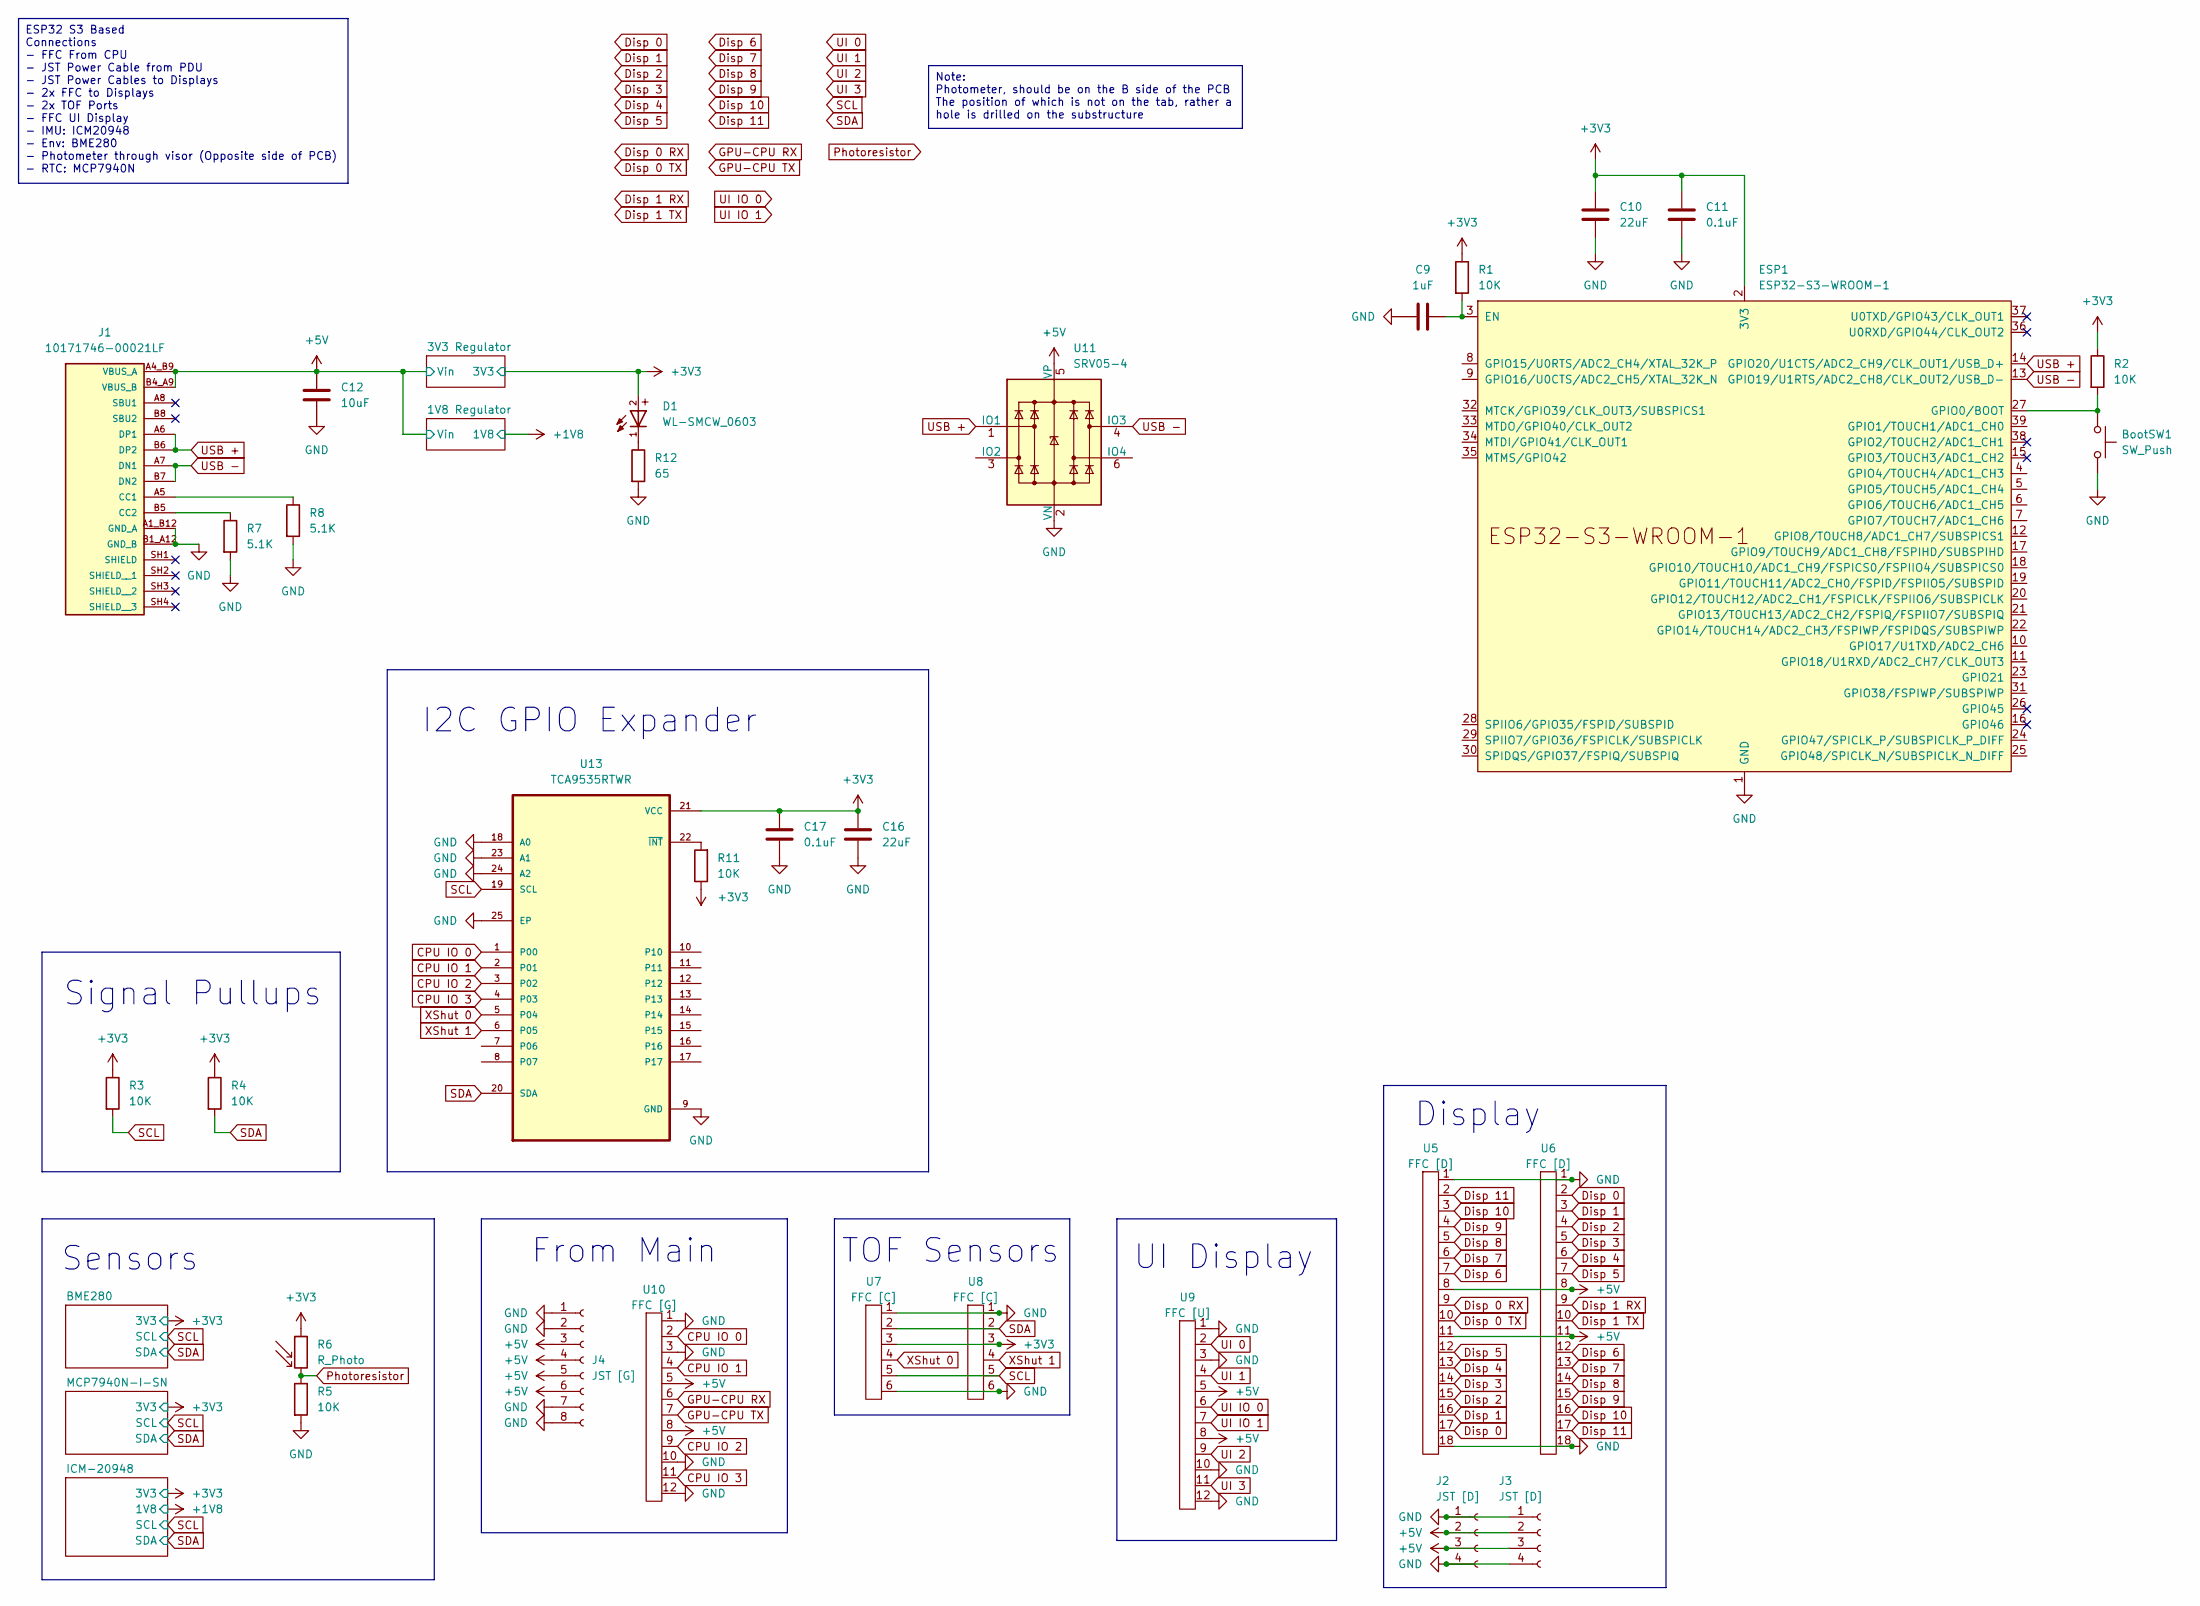
[picture p65: schematic Synth Head GPU.kicad_sch]

Parts:
BootSW1: SW_Push; Button-R-667843
C9: 1uF; C_0603_1608Metric
C10, C16: 22uF; C_0603_1608Metric_Pad1.08x0.95mm_HandSolder
C11, C17: 0.1uF; C_0603_1608Metric
C12: 10uF; C_0603_1608Metric
D1: WL-SMCW_0603
ESP1: ESP32-S3-WROOM-1; ESP32-S3-WROOM-1U
J1: 10171746-00021LF; AMPHENOL_10171746-00021LF; PARTREV A
J2, J3: JST [D]; Molex_PicoBlade_53048-0410_1x04_P1.25mm_Horizontal
J4: JST [G]; PinHeader_1x08_P2.54mm_Horizontal
R1, R2, R11: 10K; R_0603_1608Metric
R3, R4, R5: 10K; R_0603_1608Metric_Pad0.98x0.95mm_HandSolder
R6: R_Photo; Photoresistor Aliexpress
R7, R8: 5.1K; R_0603_1608Metric
R12: 65; R_0603_1608Metric_Pad0.98x0.95mm_HandSolder
U5, U6: FFC [D]; FFC Aliexpress 0.5mm 18P
U7, U8: FFC [C]; FFC Aliexpress 0.5mm 6P
U9: FFC [U]; FFC Aliexpress 0.5mm 12P
U10: FFC [G]; FFC Aliexpress 0.5mm 12P
U11: SRV05-4; SOT-23-6
U13: TCA9535RTWR; QFN50P400X400X80-25N

Connections:
+3V3: C10.1, C11.1, C16.1, C17.1, D1.2, ESP1.2 (3V3), R1.1, R2.1, R3.1, R4.1, R6.1, R11.1, U7.3, U8.3, U13.21 (VCC); also elsewhere on the board
+5V: C12.1, J1.A4_B9 (VBUS_A), J1.B4_A9 (VBUS_B), J2.2, J2.3, J3.2, J3.3, J4.3, J4.4, J4.5, J4.6, U5.8, U5.11, U6.8, U6.11, U9.5, U9.8, U10.5, U10.8, U11.5 (VP); also elsewhere on the board
CPU IO 0: U10.2, U13.1 (P00)
CPU IO 1: U10.4, U13.2 (P01)
CPU IO 2: U10.9, U13.3 (P02)
CPU IO 3: U10.11, U13.4 (P03)
Disp 0: U5.17, U6.2
Disp 0 RX: U5.9
Disp 0 TX: U5.10
Disp 1: U5.16, U6.3
Disp 1 RX: U6.9
Disp 1 TX: U6.10
Disp 2: U5.15, U6.4
Disp 3: U5.14, U6.5
Disp 4: U5.13, U6.6
Disp 5: U5.12, U6.7
Disp 6: U5.7, U6.12
Disp 7: U5.6, U6.13
Disp 8: U5.5, U6.14
Disp 9: U5.4, U6.15
Disp 10: U5.3, U6.16
Disp 11: U5.2, U6.17
GND: BootSW1.2, C9.1, C10.2, C11.2, C12.2, C16.2, C17.2, ESP1.1 (GND), ESP1.40 (GND), ESP1.41 (GND), J1.A1_B12 (GND_A), J1.B1_A12 (GND_B), J2.1, J2.4, J3.1, J3.4, J4.1, J4.2, J4.7, J4.8, R5.2, R7.2, R8.2, R12.2, U5.1, U5.18, U6.1, U6.18, U7.1, U7.6, U8.1, U8.6, U9.1, U9.3, U9.10, U9.12, U10.1, U10.3, U10.10, U10.12, U11.2 (VN), U13.9 (GND), U13.18 (A0), U13.23 (A1), U13.24 (A2), U13.25 (EP); also elsewhere on the board
GPU-CPU RX: U10.6
GPU-CPU TX: U10.7
unnamed: D1.1, R12.1
unnamed: C9.2, ESP1.3 (EN), R1.2
unnamed: BootSW1.1, ESP1.27 (GPIO0/BOOT), R2.2
unnamed: J1.A5 (CC1), R8.1
unnamed: J1.B5 (CC2), R7.1
unnamed: R11.2, U13.22 (~INT)
Photoresistor: R5.1, R6.2
SCL: R3.2, U7.5, U8.5, U13.19 (SCL); also elsewhere on the board
SDA: R4.2, U7.2, U8.2, U13.20 (SDA); also elsewhere on the board
UI 0: U9.2
UI 1: U9.4
UI 2: U9.9
UI 3: U9.11
UI IO 0: U9.6
UI IO 1: U9.7
USB +: ESP1.14 (GPIO20/U1CTS/ADC2_CH9/CLK_OUT1/USB_D+), J1.A6 (DP1), J1.B6 (DP2), U11.1 (IO1)
USB -: ESP1.13 (GPIO19/U1RTS/ADC2_CH8/CLK_OUT2/USB_D-), J1.A7 (DN1), J1.B7 (DN2), U11.4 (IO3)
XShut 0: U7.4, U13.5 (P04)
XShut 1: U8.4, U13.6 (P05)

Notes on the sheet:
ESP32 S3 Based Connections - FFC From CPU - JST Power Cable from PDU - JST Power Cables to Displays - 2x FFC to Displays - 2x TOF Ports - FFC UI Display - IMU: ICM20948 - Env: BME280 - Photometer through visor (Opposite side of PCB) - RTC: MCP7940N
Note: Photometer, should be on the B side of the PCB The position of which is not on the tab, rather a hole is drilled on the substructure
Signal Pullups
I2C GPIO Expander
TOF Sensors
From Main
Display
UI Display
Sensors

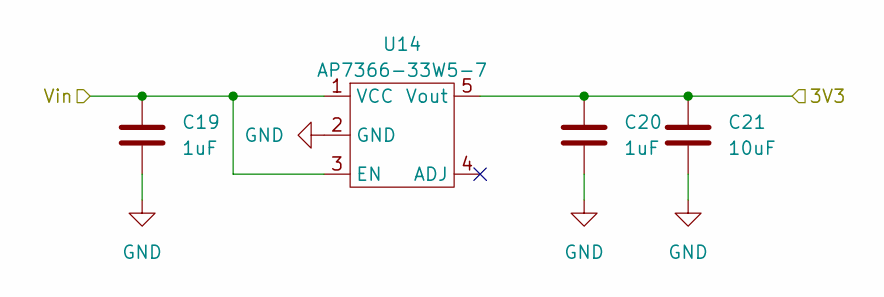
[picture p66: schematic 3V3 Reg.kicad_sch]

Parts:
C19, C20: 1uF; R_0603_1608Metric
C21: 10uF; C_0603_1608Metric
U14: AP7366-33W5-7; AP7366

Connections:
+3V3: C20.1, C21.1, U14.5 (Vout); also elsewhere on the board
+5V: C19.1, U14.1 (VCC), U14.3 (EN); also elsewhere on the board
GND: C19.2, C20.2, C21.2, U14.2 (GND); also elsewhere on the board


Parts:
C4, C5: 100nF; C_0603_1608Metric_Pad1.08x0.95mm_HandSolder
U2: BME280; Bosch_LGA-8_2.5x2.5mm_P0.65mm_ClockwisePinNumbering

Connections:
+3V3: C4.2, C5.1, U2.2 (CSB), U2.6 (VDDIO), U2.8 (VDD); also elsewhere on the board
GND: C4.1, C5.2, U2.1 (GND), U2.5 (SDO), U2.7 (GND); also elsewhere on the board
SCL: U2.4 (SCK); also elsewhere on the board
SDA: U2.3 (SDI); also elsewhere on the board

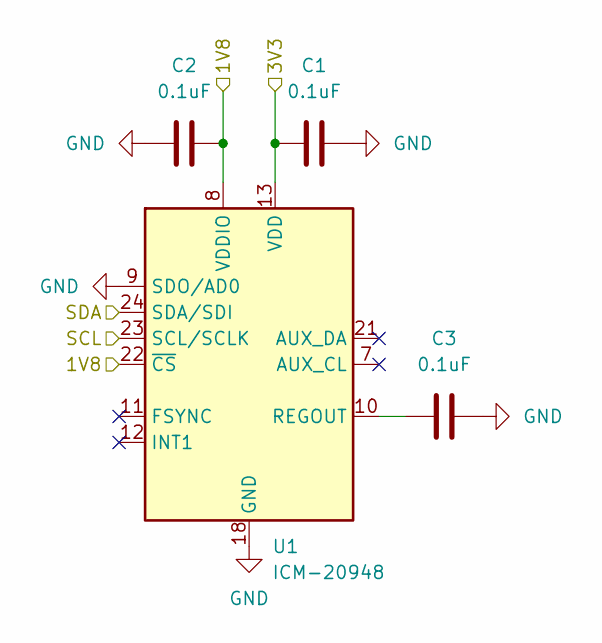
[picture p67: schematic ICM20948.kicad_sch]

Parts:
C1, C2, C3: 0.1uF; C_0603_1608Metric_Pad1.08x0.95mm_HandSolder
U1: ICM-20948; InvenSense_QFN-24_3x3mm_P0.4mm

Connections:
+1V8: C2.2, U1.8 (VDDIO), U1.22 (~CS); also elsewhere on the board
+3V3: C1.1, U1.13 (VDD); also elsewhere on the board
GND: C1.2, C2.1, C3.2, U1.9 (SDO/AD0), U1.18 (GND), U1.20 (GND); also elsewhere on the board
unnamed: C3.1, U1.10 (REGOUT)
SCL: U1.23 (SCL/SCLK); also elsewhere on the board
SDA: U1.24 (SDA/SDI); also elsewhere on the board

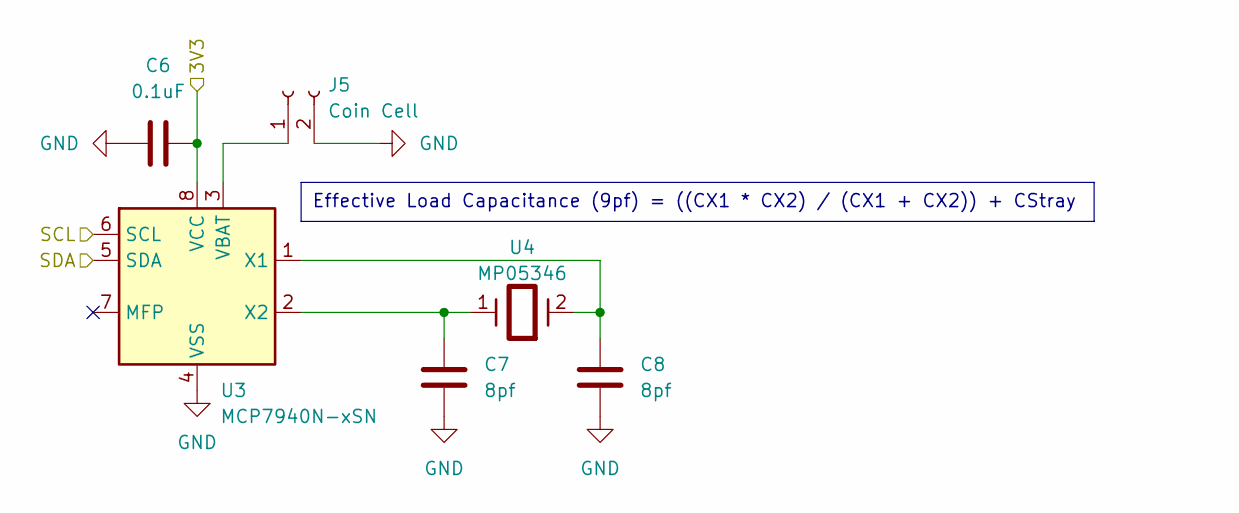
[picture p68: schematic MCP7940N-SN.kicad_sch]

Parts:
C6: 0.1uF; C_0603_1608Metric_Pad1.08x0.95mm_HandSolder
C7, C8: 8pf; C_0603_1608Metric_Pad1.08x0.95mm_HandSolder
J5: Coin Cell; PinHeader_1x02_P2.54mm_Vertical
U3: MCP7940N-xSN; SOIC-8_3.9x4.9mm_P1.27mm
U4: MP05346

Connections:
+3V3: C6.2, U3.8 (VCC); also elsewhere on the board
GND: C6.1, C7.2, C8.2, J5.2, U3.4 (VSS); also elsewhere on the board
unnamed: J5.1, U3.3 (VBAT)
unnamed: C8.1, U3.1 (X1), U4.2
unnamed: C7.1, U3.2 (X2), U4.1
SCL: U3.6 (SCL); also elsewhere on the board
SDA: U3.5 (SDA); also elsewhere on the board

Notes on the sheet:
Effective Load Capacitance (9pf) = ((CX1 * CX2) / (CX1 + CX2)) + CStray

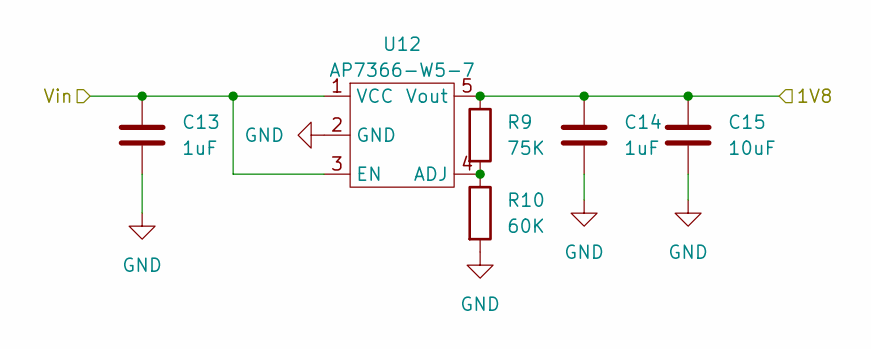
[picture p69: schematic 1V8 Reg.kicad_sch]

Parts:
C13, C14: 1uF; R_0603_1608Metric
C15: 10uF; C_0603_1608Metric
R9: 75K; R_0603_1608Metric
R10: 60K; R_0603_1608Metric
U12: AP7366-W5-7; AP7366

Connections:
+1V8: C14.1, C15.1, R9.1, U12.5 (Vout); also elsewhere on the board
+5V: C13.1, U12.1 (VCC), U12.3 (EN); also elsewhere on the board
GND: C13.2, C14.2, C15.2, R10.2, U12.2 (GND); also elsewhere on the board
unnamed: R9.2, R10.1, U12.4 (ADJ)

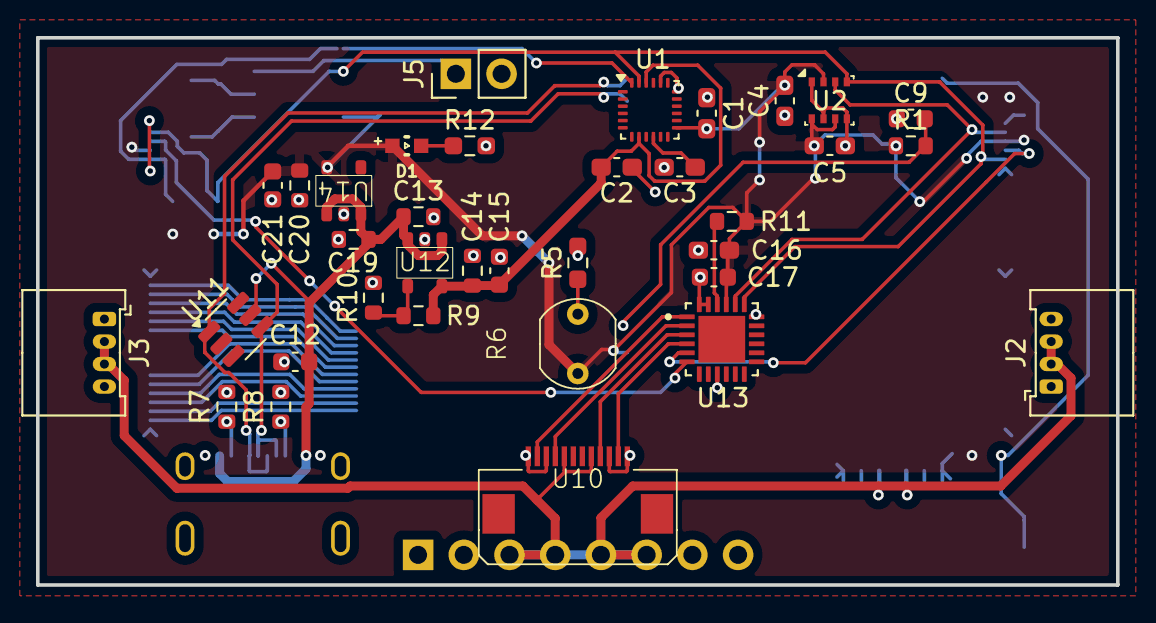
[picture p70: board Synth Head GPU.kicad_pcb from above]

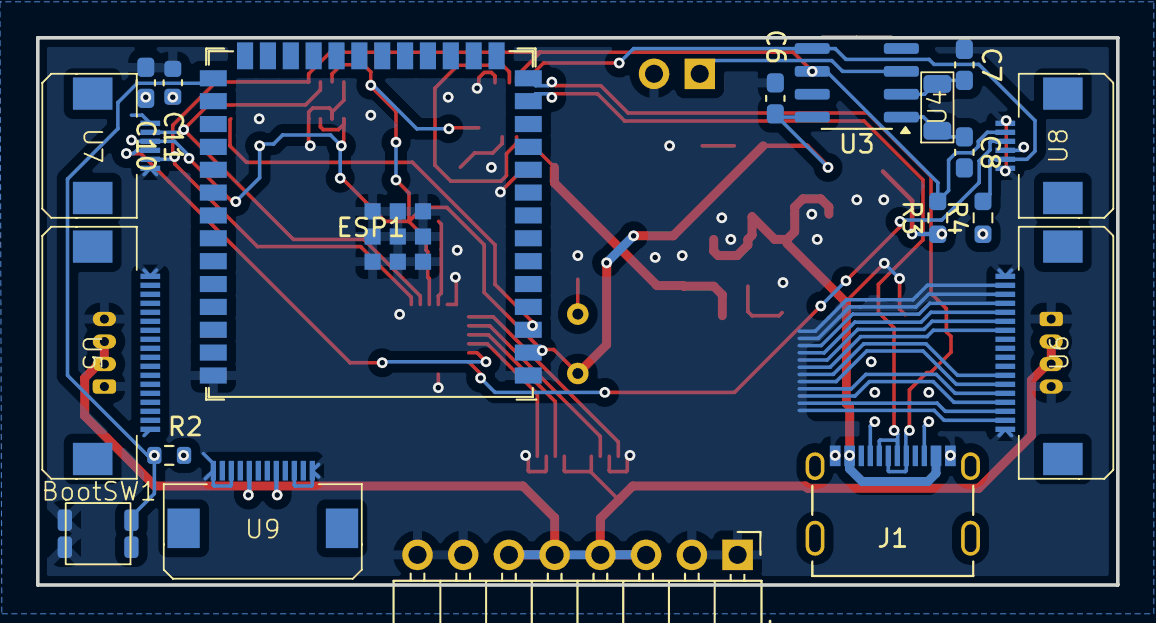
[picture p71: board Synth Head GPU.kicad_pcb from below]

Board: 2 copper layers, 60.0 x 30.4 mm, 54 parts (19 on the bottom side), 38 nets.
