Cyberspecies/Synth-Head/Software/Testing_N_Experimentation/Alpha_Release_Stack/src/GPU_Programmable.cpp

/**
 * @file GPU_Programmable.cpp
 * @brief Fully Programmable GPU - No hardcoded effects
 * 
 * Architecture:
 * - Shader slots: CPU uploads bytecode programs
 * - Sprite bank: CPU uploads bitmap sprites  
 * - Variables: CPU sets values, shaders read them
 * - Registers: Runtime computation in shaders
 * - Framebuffers: HUB75 (128x32 RGB) + OLED (128x128 mono)
 * 
 * The GPU starts EMPTY - all effects come from CPU-uploaded shaders
 */

#include <cstdio>
#include <cstdint>
#include <cstring>
#include <cmath>
#include <atomic>
#include "freertos/FreeRTOS.h"
#include "freertos/task.h"
#include "freertos/semphr.h"
#include "driver/uart.h"
#include "driver/gpio.h"
#include "esp_log.h"
#include "esp_timer.h"
#include "esp_heap_caps.h"

// ARCOS HUB75 driver
#include "abstraction/hal.hpp"
#include "abstraction/drivers/components/HUB75/driver_hub75_simple.hpp"

// OLED driver
#include "abstraction/drivers/components/OLED/driver_oled_sh1107.hpp"

// Import types from ARCOS namespaces
using namespace arcos::abstraction::drivers;
using namespace arcos::abstraction;

static const char* TAG = "GPU_PROG";

// Debug counters (atomics for cross-core visibility)
static std::atomic<uint32_t> dbg_hub75_presents{0};
static std::atomic<uint32_t> dbg_oled_presents{0};
static std::atomic<uint32_t> dbg_oled_updates{0};
static std::atomic<uint32_t> dbg_cmd_count{0};
static std::atomic<uint32_t> dbg_oled_cmd_count{0};
static std::atomic<int64_t> dbg_last_hub75_present{0};
static std::atomic<int64_t> dbg_last_oled_present{0};

// Frame rate limiter - prevent overwhelming the display hardware
static int64_t lastPresentTime = 0;
static const int64_t MIN_PRESENT_INTERVAL_US = 8000;  // 8ms = 120 FPS max
static uint32_t droppedFrames = 0;

// ============================================================
// GPU Alert/Feedback System
// ============================================================
// Alert severity levels
enum class AlertLevel : uint8_t {
  INFO = 0,      // Informational
  WARNING = 1,   // Recoverable issue
  ERROR = 2,     // Serious problem
  CRITICAL = 3,  // System failing
};

// Alert types
enum class AlertType : uint8_t {
  NONE = 0x00,
  BUFFER_WARNING = 0x01,    // RX buffer filling up (>50%)
  BUFFER_CRITICAL = 0x02,   // RX buffer almost full (>75%)
  BUFFER_OVERFLOW = 0x03,   // RX buffer overflowed, data lost
  FRAME_DROP = 0x10,        // Frames being dropped
  FRAME_DROP_SEVERE = 0x11, // Many frames dropped (>10/sec)
  HEAP_LOW = 0x20,          // Heap memory low (<50KB)
  HEAP_CRITICAL = 0x21,     // Heap memory critical (<20KB)
  HUB75_ERROR = 0x30,       // HUB75 display error
  OLED_ERROR = 0x31,        // OLED display error
  UART_ERROR = 0x40,        // UART communication error
  PARSER_ERROR = 0x41,      // Command parser error
  RECOVERED = 0xF0,         // Previously reported issue resolved
};

// Alert tracking state
static uint32_t alertsSent = 0;
static int64_t lastAlertTime = 0;
static constexpr int64_t MIN_ALERT_INTERVAL_US = 100000;  // 100ms between alerts
static AlertType lastAlertType = AlertType::NONE;
static uint32_t bufferWarningCount = 0;
static uint32_t bufferOverflowTotal = 0;
static uint32_t parserErrorCount = 0;
static uint32_t frameDropsThisSecond = 0;
static int64_t lastFrameDropReset = 0;
static bool bufferWarningActive = false;
static bool heapWarningActive = false;

// ============================================================
// Hardware Configuration
// ============================================================
constexpr int PANEL_WIDTH = 64;
constexpr int PANEL_HEIGHT = 32;
constexpr int NUM_PANELS = 2;
constexpr int TOTAL_WIDTH = PANEL_WIDTH * NUM_PANELS;  // 128
constexpr int TOTAL_HEIGHT = PANEL_HEIGHT;              // 32

constexpr int OLED_WIDTH = 128;
constexpr int OLED_HEIGHT = 128;

// UART
constexpr uart_port_t UART_PORT = UART_NUM_1;
constexpr int UART_RX_PIN = 13;
constexpr int UART_TX_PIN = 12;
constexpr int UART_BAUD = 921600;  // Lowered for reliability testing

// ============================================================
// GPU Memory Limits
// ============================================================
constexpr int MAX_SHADERS = 8;
constexpr int MAX_SHADER_SIZE = 1024;      // 1KB bytecode per shader
constexpr int MAX_SPRITES = 16;
constexpr int MAX_SPRITE_SIZE = 16384;     // 16KB per sprite (supports up to 128x32 RGB or 73x73 RGB)
constexpr int MAX_VARIABLES = 256;
constexpr int MAX_REGISTERS = 16;
constexpr int MAX_STACK = 16;              // Loop stack depth

// ============================================================
// Lookup Tables (256 entries, 0-255 output)
// ============================================================
static uint8_t SIN_LUT[256];
static uint8_t COS_LUT[256];
static uint8_t SQRT_LUT[256];

static void initLUTs() {
  for (int i = 0; i < 256; i++) {
    float angle = (i / 256.0f) * 2.0f * M_PI;
    SIN_LUT[i] = (uint8_t)(127.5f + 127.5f * sinf(angle));
    COS_LUT[i] = (uint8_t)(127.5f + 127.5f * cosf(angle));
    SQRT_LUT[i] = (uint8_t)(sqrtf(i / 255.0f) * 255.0f);
  }
}

// ============================================================
// Shader Bytecode Opcodes
// ============================================================
enum class Op : uint8_t {
  NOP = 0x00,
  HALT = 0x01,
  
  // Register operations
  SET = 0x10,      // SET Rd, imm16
  MOV = 0x11,      // MOV Rd, Rs
  LOAD = 0x12,     // LOAD Rd, var_id
  STORE = 0x13,    // STORE var_id, Rs
  
  // Arithmetic (all operate on 16-bit signed)
  ADD = 0x20,      // ADD Rd, Ra, Rb
  SUB = 0x21,      // SUB Rd, Ra, Rb
  MUL = 0x22,      // MUL Rd, Ra, Rb (result >> 8 for fixed-point)
  DIV = 0x23,      // DIV Rd, Ra, Rb
  MOD = 0x24,      // MOD Rd, Ra, Rb
  NEG = 0x25,      // NEG Rd, Rs
  ABS = 0x26,      // ABS Rd, Rs
  MIN = 0x27,      // MIN Rd, Ra, Rb
  MAX = 0x28,      // MAX Rd, Ra, Rb
  
  // Bitwise
  AND = 0x30,      // AND Rd, Ra, Rb
  OR = 0x31,       // OR Rd, Ra, Rb
  XOR = 0x32,      // XOR Rd, Ra, Rb
  NOT = 0x33,      // NOT Rd, Rs
  SHL = 0x34,      // SHL Rd, Rs, imm
  SHR = 0x35,      // SHR Rd, Rs, imm
  
  // LUT functions
  SIN = 0x40,      // SIN Rd, Rs (index into SIN_LUT)
  COS = 0x41,      // COS Rd, Rs
  SQRT = 0x42,     // SQRT Rd, Rs
  
  // Drawing (immediate values or registers)
  SETPX = 0x50,    // SETPX x, y, r, g, b
  GETPX = 0x51,    // GETPX Rd, x, y
  FILL = 0x52,     // FILL x, y, w, h, r, g, b
  LINE = 0x53,     // LINE x1, y1, x2, y2, r, g, b
  RECT = 0x54,     // RECT x, y, w, h, r, g, b (outline)
  CIRCLE = 0x55,   // CIRCLE cx, cy, r, r, g, b
  POLY = 0x56,     // POLY n_verts, vert_var_start, r, g, b
  SPRITE = 0x57,   // SPRITE id, x, y
  CLEAR = 0x58,    // CLEAR r, g, b
  
  // Control flow
  LOOP = 0x60,     // LOOP count_reg - begin loop
  ENDL = 0x61,     // ENDL - end loop
  JMP = 0x62,      // JMP offset (signed 16-bit)
  JZ = 0x63,       // JZ Rs, offset
  JNZ = 0x64,      // JNZ Rs, offset
  JGT = 0x65,      // JGT Rs, offset (if Rs > 0)
  JLT = 0x66,      // JLT Rs, offset (if Rs < 0)
  
  // Special
  GETX = 0x70,     // GETX Rd - get current pixel X (in pixel shader)
  GETY = 0x71,     // GETY Rd - get current pixel Y
  GETW = 0x72,     // GETW Rd - get framebuffer width
  GETH = 0x73,     // GETH Rd - get framebuffer height
  TIME = 0x74,     // TIME Rd - get milliseconds
  RAND = 0x75,     // RAND Rd - pseudo-random value
};

// ============================================================
// Shader Structure
// ============================================================
struct Shader {
  uint8_t bytecode[MAX_SHADER_SIZE];
  uint16_t length;
  bool valid;
};

// ============================================================
// Sprite Structure
// ============================================================
struct Sprite {
  uint8_t* data;      // RGB888 or 1-bit depending on target
  uint8_t width;
  uint8_t height;
  uint8_t format;     // 0=RGB888, 1=mono
  bool valid;
};

// ============================================================
// GPU State
// ============================================================
struct GPUState {
  // Shader slots
  Shader shaders[MAX_SHADERS];
  
  // Sprite bank
  Sprite sprites[MAX_SPRITES];
  
  // Variables (CPU-writable, shader-readable)
  int16_t variables[MAX_VARIABLES];
  
  // Runtime registers (shader-local)
  int16_t regs[MAX_REGISTERS];
  
  // Loop stack
  struct LoopFrame {
    uint16_t pc;      // Return address
    int16_t counter;  // Remaining iterations
  };
  LoopFrame loopStack[MAX_STACK];
  int loopSP;
  
  // Current pixel position (for pixel shaders)
  int16_t px, py;
  
  // Target framebuffer (0=HUB75, 1=OLED)
  uint8_t target;
  
  // Time
  uint32_t startTime;
  uint32_t frameCount;
  
  // Random seed
  uint32_t randSeed;
};

static GPUState gpu;

// ============================================================
// Framebuffers
// ============================================================
static uint8_t* hub75_buffer = nullptr;  // TOTAL_WIDTH * TOTAL_HEIGHT * 3

constexpr int HUB75_BUFFER_SIZE = TOTAL_WIDTH * TOTAL_HEIGHT * 3;
constexpr int OLED_BUFFER_SIZE = OLED_WIDTH * OLED_HEIGHT / 8;

// ============================================================
// Hardware Instances
// ============================================================
using namespace arcos::abstraction::drivers;
using namespace arcos::abstraction;

static SimpleHUB75Display* hub75 = nullptr;
static bool hub75_ok = false;

static DRIVER_OLED_SH1107* oled = nullptr;
static bool oled_ok = false;

// OLED retained-mode rendering with TRUE triple buffering:
// - oled_back_buffer: CPU draws here (never displayed directly)
// - oled_front_buffer: Staged for next display update (swapped on OLED_PRESENT)
// - oled_display_buffer: Currently being sent to I2C (safe to read during transfer)
// Flow: CPU draws to back -> PRESENT copies back->front -> oledTask copies front->display -> I2C
static volatile bool oled_update_pending = false;
static uint8_t* oled_back_buffer = nullptr;     // Back buffer - CPU draws here
static uint8_t* oled_front_buffer = nullptr;    // Front buffer - staged for display
static uint8_t* oled_display_buffer = nullptr;  // Display buffer - being sent to I2C
static uint8_t* oled_buffer = nullptr;          // Alias for oled_back_buffer (legacy)
static uint8_t* oled_update_buffer = nullptr;   // Alias for front buffer (legacy compatibility)
static SemaphoreHandle_t oled_buffer_mutex = nullptr;  // Protects front buffer access

// Helper to safely present OLED buffer (copies back->front with mutex)
static void presentOLEDBuffer() {
  if (oled_ok && oled_buffer_mutex) {
    if (xSemaphoreTake(oled_buffer_mutex, pdMS_TO_TICKS(5)) == pdTRUE) {
      memcpy(oled_front_buffer, oled_back_buffer, OLED_BUFFER_SIZE);
      oled_update_pending = true;
      xSemaphoreGive(oled_buffer_mutex);
    }
  }
}

// Anti-aliasing enabled by default
static bool aa_enabled = true;  // Re-enabled with panel boundary fix

// OLED orientation mode (0-7) - controlled by CPU
// 0 = No transform, 1 = Rotate 180, 2 = Mirror X, 3 = Mirror Y
// 4 = Mirror X+Y, 5 = Rotate 90 CW, 6 = Rotate 90 CCW, 7 = Rot90 + Mirror X
static int oled_orientation = 0;  // CPU-controlled orientation (default: no additional transform)

// Base orientation for physical mounting compensation (always applied AFTER cpu orientation)
// Set to 1 (180° rotation) because display is physically mounted upside down
static const int BASE_OLED_ORIENTATION = 1;

// ============================================================
// GPU Stats (for REQUEST_STATS response)
// ============================================================
static float current_fps = 0.0f;           // Updated every 2 seconds in main loop
static uint32_t current_free_heap = 0;     // Free heap bytes
static uint32_t current_min_heap = 0;      // Minimum free heap seen
static uint8_t gpu_load_percent = 0;       // Estimated GPU load (0-100)
static uint32_t total_frames = 0;          // Total frames rendered since boot

// ============================================================
// Sprite Shader Configuration
// ============================================================
enum class ShaderType : uint8_t {
  NONE = 0,           // No shader - render sprite as-is
  COLOR_OVERRIDE = 1, // Replace all non-transparent pixels with a specific color
  HUE_CYCLE = 2,      // Cycle through a palette of colors smoothly
  GRADIENT_CYCLE = 3, // Gradient colors across canvas that scroll
  GLITCH = 4          // Glitch effect with displacement and chromatic aberration
};

static ShaderType g_shaderType = ShaderType::NONE;
static bool g_shaderInvertColors = false;
static bool g_shaderMaskEnabled = true;    // Default: mask is enabled (black is transparent)
static uint8_t g_shaderMaskR = 0;          // Default mask color: black
static uint8_t g_shaderMaskG = 0;
static uint8_t g_shaderMaskB = 0;
static uint8_t g_shaderParam1 = 255;       // For COLOR_OVERRIDE: override R, For HUE_CYCLE/GRADIENT: speed low byte
static uint8_t g_shaderParam2 = 255;       // For COLOR_OVERRIDE: override G, For HUE_CYCLE/GRADIENT: speed high byte
static uint8_t g_shaderParam3 = 255;       // For COLOR_OVERRIDE: override B

// Hue/Gradient cycle shader palette (up to 32 colors)
static const uint8_t MAX_PALETTE_COLORS = 32;
static uint8_t g_huePaletteCount = 5;      // Default: 5 colors
static uint8_t g_huePalette[MAX_PALETTE_COLORS * 3];  // Will be initialized in init
static uint32_t g_hueCycleStartTime = 0;   // Time when hue cycle started

// Gradient cycle specific params
static uint16_t g_gradientDistance = 20;   // Pixels between color bands
static int16_t g_gradientAngle = 0;        // Angle in degrees (-180 to 180)
static bool g_gradientMirror = false;      // Mirror gradient on right panel

// Glitch effect params (now an overlay that works on top of any shader)
static bool g_glitchOverlayEnabled = false; // Master toggle for glitch overlay
static uint8_t g_glitchSpeed = 128;        // Speed of glitch changes (0-255)
static uint8_t g_glitchIntensity = 64;     // Intensity of displacement (0-255)
static uint8_t g_glitchChromatic = 32;     // Chromatic aberration intensity (0-255)
static uint8_t g_glitchQuantity = 50;      // Quantity/density of glitch bands (0-100)
static uint32_t g_glitchSeed = 12345;      // Random seed for glitch
static uint32_t g_lastGlitchTime = 0;      // Last time glitch state changed
static int16_t g_glitchRowOffsets[32];     // Per-row horizontal displacement (32 rows max)
static bool g_glitchActive = false;        // Whether glitch effect is currently active

// Simple fast pseudo-random generator for glitch
static inline uint32_t glitchRandom() {
  g_glitchSeed = g_glitchSeed * 1103515245 + 12345;
  return (g_glitchSeed >> 16) & 0x7FFF;
}

// Update glitch state - generates per-row displacement pattern
// Called each frame when glitch overlay is enabled
static void updateGlitchState() {
  // Glitch is now an overlay - check the overlay enable flag, not shader type
  if (!g_glitchOverlayEnabled) {
    // Glitch overlay not enabled - ensure all glitch state is cleared
    if (g_glitchActive) {
      g_glitchActive = false;
      for (int i = 0; i < 32; i++) {
        g_glitchRowOffsets[i] = 0;
      }
    }
    return;
  }
  
  uint32_t now = (uint32_t)(esp_timer_get_time() / 1000);
  
  // Speed determines how often glitch pattern changes
  // speed 0 = 150ms interval, speed 100 = 15ms interval (much faster overall)
  uint32_t interval = 150 - (g_glitchSpeed * 135 / 100);
  if (interval < 15) interval = 15;
  
  if (now - g_lastGlitchTime < interval) {
    return;  // Not time to update yet
  }
  g_lastGlitchTime = now;
  
  // Reset all row offsets to 0
  for (int i = 0; i < 32; i++) {
    g_glitchRowOffsets[i] = 0;
  }
  
  // Randomly decide glitch intensity this frame
  // Higher chance of "no glitch" makes it snappier - glitches appear and disappear quickly
  uint32_t chance = glitchRandom() % 100;
  if (chance < 55) {
    // 55% chance: no glitch this frame (snappy on/off behavior)
    g_glitchActive = false;
    return;
  }
  
  g_glitchActive = true;
  
  // Max displacement based on intensity (0-100 maps to 0-24 pixels)
  int16_t maxDisp = 2 + (g_glitchIntensity * 22 / 100);
  
  // Generate random glitch bands - quantity controls max bands (1 to 8)
  int maxBands = 1 + (g_glitchQuantity * 7 / 100);  // quantity 0=1 band, 100=8 bands
  int numBands = 1 + (glitchRandom() % maxBands);
  
  for (int band = 0; band < numBands; band++) {
    int startRow = glitchRandom() % PANEL_HEIGHT;
    int bandHeight = 1 + (glitchRandom() % 4);  // 1-4 rows tall (slightly smaller bands)
    int16_t offset = (int16_t)((glitchRandom() % (maxDisp * 2 + 1))) - maxDisp;
    
    // Apply offset to rows in this band
    for (int row = startRow; row < startRow + bandHeight && row < PANEL_HEIGHT; row++) {
      g_glitchRowOffsets[row] = offset;
    }
  }
  
  // Occasionally add scattered single-row glitches - chance and count based on quantity
  int scatterChance = 20 + (g_glitchQuantity * 40 / 100);  // 20-60% chance
  if (glitchRandom() % 100 < (uint32_t)scatterChance) {
    int maxLines = 1 + (g_glitchQuantity * 5 / 100);  // 1-6 lines
    int numLines = 1 + (glitchRandom() % maxLines);
    for (int i = 0; i < numLines; i++) {
      int row = glitchRandom() % PANEL_HEIGHT;
      g_glitchRowOffsets[row] = (int16_t)((glitchRandom() % (maxDisp * 2 + 1))) - maxDisp;
    }
  }
}

// Initialize default palette
static void initDefaultPalette() {
  // Default 5 colors: Red, Yellow, Green, Blue, Purple
  uint8_t defaults[] = {
    255, 0, 0,       // Red
    255, 255, 0,     // Yellow
    0, 255, 0,       // Green
    0, 0, 255,       // Blue
    128, 0, 255      // Purple
  };
  memcpy(g_huePalette, defaults, sizeof(defaults));
  // Fill rest with red as padding
  for (int i = 5; i < MAX_PALETTE_COLORS; i++) {
    g_huePalette[i * 3 + 0] = 255;
    g_huePalette[i * 3 + 1] = 0;
    g_huePalette[i * 3 + 2] = 0;
  }
}

// Lerp between two uint8_t values
static inline uint8_t lerpU8(uint8_t a, uint8_t b, float t) {
  return (uint8_t)(a + (b - a) * t);
}

// Cached hue cycle color (same for all pixels in a frame, computed once per frame)
static uint8_t g_cachedHueR = 255, g_cachedHueG = 0, g_cachedHueB = 0;
static uint32_t g_cachedHueFrame = 0xFFFFFFFF;  // Last frame this was computed
static uint32_t g_currentFrameId = 0;  // Incremented each frame

// Update cached hue cycle color (call once per frame before rendering)
static void updateCachedHueCycleColor() {
  if (g_huePaletteCount == 0) {
    g_cachedHueR = g_cachedHueG = g_cachedHueB = 255;
    return;
  }
  
  // Get speed in ms (stored as 16-bit in param1,param2)
  uint16_t speedMs = g_shaderParam1 | (g_shaderParam2 << 8);
  if (speedMs == 0) speedMs = 1000;  // Default 1 second
  
  // Total cycle time
  uint32_t totalCycleMs = (uint32_t)speedMs * g_huePaletteCount;
  
  // Current time in cycle
  uint32_t now = (uint32_t)(esp_timer_get_time() / 1000);  // Convert to ms
  uint32_t elapsed = (now - g_hueCycleStartTime) % totalCycleMs;
  
  // Which color segment are we in?
  uint32_t segmentIndex = elapsed / speedMs;
  float segmentProgress = (float)(elapsed % speedMs) / (float)speedMs;
  
  // Get the two colors to interpolate between
  uint8_t idx1 = segmentIndex % g_huePaletteCount;
  uint8_t idx2 = (segmentIndex + 1) % g_huePaletteCount;
  
  // Interpolate and cache
  g_cachedHueR = lerpU8(g_huePalette[idx1 * 3 + 0], g_huePalette[idx2 * 3 + 0], segmentProgress);
  g_cachedHueG = lerpU8(g_huePalette[idx1 * 3 + 1], g_huePalette[idx2 * 3 + 1], segmentProgress);
  g_cachedHueB = lerpU8(g_huePalette[idx1 * 3 + 2], g_huePalette[idx2 * 3 + 2], segmentProgress);
}

// Get current hue cycle color (uses cached value, very fast)
static inline void getHueCycleColor(uint8_t& r, uint8_t& g, uint8_t& b) {
  r = g_cachedHueR;
  g = g_cachedHueG;
  b = g_cachedHueB;
}

// Cached gradient cycle values (updated once per frame)
static float g_cachedGradientDirX = 1.0f, g_cachedGradientDirY = 0.0f;
static float g_cachedGradientDirXMirror = -1.0f;  // For mirrored right panel
static float g_cachedGradientScrollOffset = 0.0f;
static float g_cachedGradientTotalLength = 64.0f;
static float g_cachedGradientInvDistance = 1.0f / 64.0f;

// Update cached gradient values (call once per frame before rendering)
static void updateCachedGradientValues() {
  if (g_huePaletteCount == 0) return;
  
  // Get speed in ms (stored as 16-bit in param1,param2)
  uint16_t speedMs = g_shaderParam1 | (g_shaderParam2 << 8);
  if (speedMs == 0) speedMs = 1000;  // Default 1 second
  
  // Pre-compute angle direction
  float angleRad = (float)g_gradientAngle * 3.14159265f / 180.0f;
  g_cachedGradientDirX = cosf(angleRad);
  g_cachedGradientDirY = sinf(angleRad);
  g_cachedGradientDirXMirror = cosf(-angleRad);  // For mirrored panels
  
  // Pre-compute time-based scroll offset
  uint32_t now = (uint32_t)(esp_timer_get_time() / 1000);
  uint32_t elapsed = now - g_hueCycleStartTime;
  float pixelsPerMs = (float)g_gradientDistance / (float)speedMs;
  g_cachedGradientScrollOffset = (float)elapsed * pixelsPerMs;
  
  // Pre-compute total gradient length and inverse distance for division
  g_cachedGradientTotalLength = (float)g_gradientDistance * (float)g_huePaletteCount;
  g_cachedGradientInvDistance = 1.0f / (float)g_gradientDistance;
}

// Get gradient cycle color based on position (uses cached frame values)
// Projects pixel position onto angle direction and calculates color from gradient
static inline void getGradientCycleColor(int16_t pixelX, int16_t pixelY, uint8_t& r, uint8_t& g, uint8_t& b) {
  if (g_huePaletteCount == 0) {
    r = g = b = 255;
    return;
  }
  
  // Calculate effective position for gradient calculation
  int16_t effectiveX = pixelX;
  float dirX = g_cachedGradientDirX;
  bool isRightPanel = (pixelX >= PANEL_WIDTH);
  
  if (g_gradientMirror && isRightPanel) {
    // Mirror effect: transform right panel coordinates to mirror left panel
    effectiveX = TOTAL_WIDTH - 1 - pixelX;
    dirX = g_cachedGradientDirXMirror;
  }
  
  // Project pixel position onto direction vector to get position along gradient
  float projectedPos = (float)effectiveX * dirX + (float)pixelY * g_cachedGradientDirY;
  
  // Add scroll offset to position and wrap
  float gradientPos = projectedPos + g_cachedGradientScrollOffset;
  
  // Wrap to total gradient length (handle negatives)
  gradientPos = fmodf(gradientPos, g_cachedGradientTotalLength);
  if (gradientPos < 0) gradientPos += g_cachedGradientTotalLength;
  
  // Calculate which color segment we're in (use cached inverse for faster division)
  float segmentFloat = gradientPos * g_cachedGradientInvDistance;
  int segmentIndex = (int)segmentFloat;
  float segmentProgress = segmentFloat - (float)segmentIndex;
  
  // Clamp segment index
  segmentIndex = segmentIndex % g_huePaletteCount;
  int nextIndex = (segmentIndex + 1) % g_huePaletteCount;
  
  // Interpolate between colors
  r = lerpU8(g_huePalette[segmentIndex * 3 + 0], g_huePalette[nextIndex * 3 + 0], segmentProgress);
  g = lerpU8(g_huePalette[segmentIndex * 3 + 1], g_huePalette[nextIndex * 3 + 1], segmentProgress);
  b = lerpU8(g_huePalette[segmentIndex * 3 + 2], g_huePalette[nextIndex * 3 + 2], segmentProgress);
}

// Apply shader processing to a pixel color
// Order: 1) Invert, 2) Check mask (return transparent), 3) Apply shader effect
// Returns true if pixel should be rendered, false if transparent
// Note: pixelX/Y used for GRADIENT_CYCLE and GLITCH shaders
static inline bool applyShaderToPixel(uint8_t& r, uint8_t& g, uint8_t& b, uint8_t alpha, int16_t pixelX = 0, int16_t pixelY = 0) {
    // Step 1: Invert colors if enabled
    if (g_shaderInvertColors) {
        r = 255 - r;
        g = 255 - g;
        b = 255 - b;
    }
    
    // Step 2: Check color mask - if pixel matches mask color, make it transparent
    if (g_shaderMaskEnabled) {
        if (r == g_shaderMaskR && g == g_shaderMaskG && b == g_shaderMaskB) {
            return false;  // Transparent
        }
    }
    
    // Step 3: Apply shader effect
    switch (g_shaderType) {
        case ShaderType::COLOR_OVERRIDE:
            // Replace color with override color (keep alpha)
            r = g_shaderParam1;
            g = g_shaderParam2;
            b = g_shaderParam3;
            break;
        case ShaderType::HUE_CYCLE:
            // Replace color with cycling hue color
            getHueCycleColor(r, g, b);
            break;
        case ShaderType::GRADIENT_CYCLE:
            // Replace color with gradient based on position
            getGradientCycleColor(pixelX, pixelY, r, g, b);
            break;
        case ShaderType::GLITCH:
            // Glitch effect is applied as post-process in presentHUB75Buffer
            // Keep original color here - the displacement happens during present
            break;
        case ShaderType::NONE:
        default:
            // No effect - keep original color
            break;
    }
    
    return true;  // Render the pixel
}

// ============================================================
// Boot Animation & No Signal State
// ============================================================
enum class BootState {
  FADE_IN,       // Fading in the logo
  HOLD,          // Waiting for CPU connection
  FADE_OUT,      // Fading out the logo
  RUNNING,       // Normal operation
  NO_SIGNAL      // CPU disconnected - show no signal animation
};

static BootState bootState = BootState::FADE_IN;
static int64_t bootStartTime = 0;
static int64_t lastCpuCommandTime = 0;      // Any command (for cpuConnected)
static int64_t lastDisplayCommandTime = 0;   // Only display commands (for NO_SIGNAL timeout)
static int64_t fadeOutStartTime = 0;
static bool cpuConnected = false;
static const int64_t FADE_DURATION_US = 1500000;  // 1.5 seconds
static const int64_t NO_SIGNAL_TIMEOUT_US = 3000000;  // 3 seconds

// Logo vertices (scaled from 445x308 SVG)
// Circle: center (216, 114), radius 39.5
// Main outline path - exact coordinates from SVG path
static const int16_t LOGO_OUTLINE[] = {
  // Path: M238 3 L221.5 0.5 H161 L142 1.5 L106 4.5 L89 6 L72.5 10.5 L58.5 16 L48.5 21 L35.5 30.5
  // L27 39 L20 47.5 L14 57.5 L7 75 L1 98.5 L0.5 109 V116 L2 122 L5 126 L8.5 128.5 L21.5 132.5
  // L38 137.5 L58.5 144.5 L75 151 L90 159 L101.5 167 L117 177.5 L131 189 L139.5 197.5 L149 205.5
  // L158.5 212 L170.5 218 L186 223.5 L201 226.5 L216 227.5 L230 226.5 L242 223.5 L258.5 218.5
  // L278.5 208.5 L292 198.5 L302 188.5 L312 176 L319 163.5 L323 153.5 L327 138.5 L328.5 122
  // V106 L326.5 89 L321.5 72.5 L316.5 61 L310.5 51 L303.5 42.5 L293.5 31.5 L281 22.5 L267.5 14.5
  // L255.5 9 L238 3 Z
  238, 3,  222, 1,  161, 1,  142, 2,  106, 5,  89, 6,  73, 11,  59, 16,
  49, 21,  36, 31,  27, 39,  20, 48,  14, 58,  7, 75,  1, 99,  1, 109,
  1, 116,  2, 122,  5, 126,  9, 129,  22, 133,  38, 138,  59, 145,  75, 151,
  90, 159,  102, 167,  117, 178,  131, 189,  140, 198,  149, 206,
  159, 212,  171, 218,  186, 224,  201, 227,  216, 228,  230, 227,  242, 224,  259, 219,
  279, 209,  292, 199,  302, 189,  312, 176,  319, 164,  323, 154,  327, 139,
  329, 122,  329, 106,  327, 89,  322, 73,  317, 61,  311, 51,  304, 43,
  294, 32,  281, 23,  268, 15,  256, 9,  238, 3
};
static const int LOGO_OUTLINE_COUNT = sizeof(LOGO_OUTLINE) / (2 * sizeof(int16_t));

// Right decorative path - exact coordinates from SVG path
static const int16_t LOGO_RIGHT[] = {
  // Path: M384.5 130.5 L347.5 77.5 L346 76 L343.5 76.5 L342 78 V81 L343.5 88 L345.5 99.5 V112
  // L345 127 L342.5 140 L338.5 156 L332 171 L322.5 188.5 L311.5 203.5 L297.5 216.5 L285.5 225
  // L284 230 L285 235.5 L289 240 L302 242 L320 245 L339 251 L355 257.5 L372 266.5 L404.5 287.5
  // L433 305 L439.5 307.5 H442.5 L444 305.5 V290 L441.5 272 L434 240 L419.5 198.5 L405 166
  // L384.5 130.5 Z
  385, 131,  348, 78,  346, 76,  344, 77,  342, 78,  342, 81,  344, 88,  346, 100,  346, 112,
  345, 127,  343, 140,  339, 156,  332, 171,  323, 189,  312, 204,  298, 217,
  286, 225,  284, 230,  285, 236,  289, 240,  302, 242,  320, 245,  339, 251,
  355, 258,  372, 267,  405, 288,  433, 305,  440, 308,  443, 308,  444, 306,
  444, 290,  442, 272,  434, 240,  420, 199,  405, 166,  385, 131
};
static const int LOGO_RIGHT_COUNT = sizeof(LOGO_RIGHT) / (2 * sizeof(int16_t));

// Circle parameters
static const float LOGO_CIRCLE_X = 216.0f;
static const float LOGO_CIRCLE_Y = 114.0f;
static const float LOGO_CIRCLE_R = 39.5f;
static const float LOGO_WIDTH = 445.0f;
static const float LOGO_HEIGHT = 308.0f;

// ============================================================
// Pixel Operations
// ============================================================

// Alpha-blend a pixel (for anti-aliasing)
// alpha: 0-255, where 255 = fully opaque
static inline void blendPixelHUB75(int x, int y, uint8_t r, uint8_t g, uint8_t b, uint8_t alpha) {
  if (x < 0 || x >= TOTAL_WIDTH || y < 0 || y >= TOTAL_HEIGHT) return;
  if (alpha == 0) return;
  // Write directly to buffer - transforms applied in presentHUB75Buffer (consistent with setPixelHUB75)
  int idx = (y * TOTAL_WIDTH + x) * 3;
  if (alpha == 255) {
    hub75_buffer[idx + 0] = r;
    hub75_buffer[idx + 1] = g;
    hub75_buffer[idx + 2] = b;
  } else {
    // Linear blend: out = bg * (1 - a) + fg * a
    uint8_t inv_alpha = 255 - alpha;
    hub75_buffer[idx + 0] = (hub75_buffer[idx + 0] * inv_alpha + r * alpha) >> 8;
    hub75_buffer[idx + 1] = (hub75_buffer[idx + 1] * inv_alpha + g * alpha) >> 8;
    hub75_buffer[idx + 2] = (hub75_buffer[idx + 2] * inv_alpha + b * alpha) >> 8;
  }
}

static inline void setPixelHUB75(int x, int y, uint8_t r, uint8_t g, uint8_t b) {
  if (x < 0 || x >= TOTAL_WIDTH || y < 0 || y >= TOTAL_HEIGHT) return;
  // Write directly to buffer - transforms applied in presentHUB75Buffer
  int idx = (y * TOTAL_WIDTH + x) * 3;
  hub75_buffer[idx + 0] = r;
  hub75_buffer[idx + 1] = g;
  hub75_buffer[idx + 2] = b;
}

static inline void getPixelHUB75(int x, int y, uint8_t& r, uint8_t& g, uint8_t& b) {
  if (x < 0 || x >= TOTAL_WIDTH || y < 0 || y >= TOTAL_HEIGHT) {
    r = g = b = 0;
    return;
  }
  // Read directly from buffer (matches setPixelHUB75)
  int idx = (y * TOTAL_WIDTH + x) * 3;
  r = hub75_buffer[idx + 0];
  g = hub75_buffer[idx + 1];
  b = hub75_buffer[idx + 2];
}

// Transform coordinates based on a single orientation mode
static inline void applyOLEDTransform(int& x, int& y, int mode) {
  int tx, ty;
  switch (mode) {
    case 0:  // No transform
      break;
    case 1:  // Rotate 180° (mirror X and Y)
      x = (OLED_WIDTH - 1) - x;
      y = (OLED_HEIGHT - 1) - y;
      break;
    case 2:  // Mirror X only (horizontal flip)
      x = (OLED_WIDTH - 1) - x;
      break;
    case 3:  // Mirror Y only (vertical flip)
      y = (OLED_HEIGHT - 1) - y;
      break;
    case 4:  // Mirror X + Y (same as 180° rotate)
      x = (OLED_WIDTH - 1) - x;
      y = (OLED_HEIGHT - 1) - y;
      break;
    case 5:  // Rotate 90° CW
      tx = (OLED_HEIGHT - 1) - y;
      ty = x;
      x = tx;
      y = ty;
      break;
    case 6:  // Rotate 90° CCW
      tx = y;
      ty = (OLED_WIDTH - 1) - x;
      x = tx;
      y = ty;
      break;
    case 7:  // Rotate 90° CW + Mirror X
      tx = y;
      ty = x;
      x = tx;
      y = ty;
      break;
    default:
      break;
  }
}

// Transform coordinates: apply CPU orientation first, then base orientation for physical mounting
static inline void transformOLEDCoords(int& x, int& y) {
  // First apply CPU-requested orientation
  applyOLEDTransform(x, y, oled_orientation);
  // Then apply base orientation for physical mounting compensation
  applyOLEDTransform(x, y, BASE_OLED_ORIENTATION);
}

// Transform for internal GPU drawing (No Signal, etc.) - only base orientation
static inline void transformOLEDCoordsInternal(int& x, int& y) {
  applyOLEDTransform(x, y, BASE_OLED_ORIENTATION);
}

// setPixelOLED: For CPU commands - applies CPU orientation + base orientation
static inline void setPixelOLED(int x, int y, bool on) {
  if (x < 0 || x >= OLED_WIDTH || y < 0 || y >= OLED_HEIGHT) return;
  
  // Apply CPU orientation + base orientation
  transformOLEDCoords(x, y);
  
  // Bounds check after transform
  if (x < 0 || x >= OLED_WIDTH || y < 0 || y >= OLED_HEIGHT) return;
  
  int byte_idx = (y / 8) * OLED_WIDTH + x;
  int bit = y % 8;
  if (on) {
    oled_back_buffer[byte_idx] |= (1 << bit);
  } else {
    oled_back_buffer[byte_idx] &= ~(1 << bit);
  }
}

// setPixelOLEDInternal: For GPU internal drawing (No Signal, boot animation)
// Only applies base orientation for physical mounting, ignores CPU orientation
static inline void setPixelOLEDInternal(int x, int y, bool on) {
  if (x < 0 || x >= OLED_WIDTH || y < 0 || y >= OLED_HEIGHT) return;
  
  // Only apply base orientation for physical mounting
  transformOLEDCoordsInternal(x, y);
  
  // Bounds check after transform
  if (x < 0 || x >= OLED_WIDTH || y < 0 || y >= OLED_HEIGHT) return;
  
  int byte_idx = (y / 8) * OLED_WIDTH + x;
  int bit = y % 8;
  if (on) {
    oled_back_buffer[byte_idx] |= (1 << bit);
  } else {
    oled_back_buffer[byte_idx] &= ~(1 << bit);
  }
}

static inline bool getPixelOLED(int x, int y) {
  if (x < 0 || x >= OLED_WIDTH || y < 0 || y >= OLED_HEIGHT) return false;
  
  // Apply orientation transform
  transformOLEDCoords(x, y);
  
  // Bounds check after transform
  if (x < 0 || x >= OLED_WIDTH || y < 0 || y >= OLED_HEIGHT) return false;
  
  int byte_idx = (y / 8) * OLED_WIDTH + x;
  int bit = y % 8;
  return (oled_back_buffer[byte_idx] >> bit) & 1;
}

// Unified pixel set based on target
static inline void setPixel(int x, int y, uint8_t r, uint8_t g, uint8_t b) {
  if (gpu.target == 0) {
    setPixelHUB75(x, y, r, g, b);
  } else {
    // Convert to mono: simple threshold
    bool on = (r + g + b) > 384;
    setPixelOLED(x, y, on);
  }
}

static inline uint32_t getPixel(int x, int y) {
  if (gpu.target == 0) {
    uint8_t r, g, b;
    getPixelHUB75(x, y, r, g, b);
    return (r << 16) | (g << 8) | b;
  } else {
    return getPixelOLED(x, y) ? 0xFFFFFF : 0x000000;
  }
}

// ============================================================
// Boot Animation Drawing Functions
// ============================================================

// Draw a simple Bresenham line (for boot animation - no AA needed)
// Uses setPixelOLEDInternal for OLED to apply only base orientation
static void bootDrawLine(int x0, int y0, int x1, int y1, uint8_t intensity, bool isOled) {
  int dx = abs(x1 - x0), sx = x0 < x1 ? 1 : -1;
  int dy = -abs(y1 - y0), sy = y0 < y1 ? 1 : -1;
  int err = dx + dy;
  
  while (true) {
    if (isOled) {
      if (intensity > 127) setPixelOLEDInternal(x0, y0, true);
    } else {
      setPixelHUB75(x0, y0, intensity, intensity, intensity);
    }
    if (x0 == x1 && y0 == y1) break;
    int e2 = 2 * err;
    if (e2 >= dy) { err += dy; x0 += sx; }
    if (e2 <= dx) { err += dx; y0 += sy; }
  }
}

// Draw a circle outline (for boot animation)
// Uses setPixelOLEDInternal for OLED to apply only base orientation
static void bootDrawCircle(int cx, int cy, int r, uint8_t intensity, bool isOled) {
  int x = r, y = 0;
  int err = 1 - r;
  
  while (x >= y) {
    if (isOled) {
      if (intensity > 127) {
        setPixelOLEDInternal(cx + x, cy + y, true); setPixelOLEDInternal(cx - x, cy + y, true);
        setPixelOLEDInternal(cx + x, cy - y, true); setPixelOLEDInternal(cx - x, cy - y, true);
        setPixelOLEDInternal(cx + y, cy + x, true); setPixelOLEDInternal(cx - y, cy + x, true);
        setPixelOLEDInternal(cx + y, cy - x, true); setPixelOLEDInternal(cx - y, cy - x, true);
      }
    } else {
      setPixelHUB75(cx + x, cy + y, intensity, intensity, intensity);
      setPixelHUB75(cx - x, cy + y, intensity, intensity, intensity);
      setPixelHUB75(cx + x, cy - y, intensity, intensity, intensity);
      setPixelHUB75(cx - x, cy - y, intensity, intensity, intensity);
      setPixelHUB75(cx + y, cy + x, intensity, intensity, intensity);
      setPixelHUB75(cx - y, cy + x, intensity, intensity, intensity);
      setPixelHUB75(cx + y, cy - x, intensity, intensity, intensity);
      setPixelHUB75(cx - y, cy - x, intensity, intensity, intensity);
    }
    y++;
    if (err < 0) {
      err += 2 * y + 1;
    } else {
      x--;
      err += 2 * (y - x + 1);
    }
  }
}

// Draw the logo on a display with given scale and offset
static void drawLogoScaled(float scale, float offsetX, float offsetY, uint8_t intensity, bool isOled) {
  // Draw main outline
  for (int i = 0; i < LOGO_OUTLINE_COUNT - 1; i++) {
    int x0 = (int)(LOGO_OUTLINE[i * 2] * scale + offsetX);
    int y0 = (int)(LOGO_OUTLINE[i * 2 + 1] * scale + offsetY);
    int x1 = (int)(LOGO_OUTLINE[(i + 1) * 2] * scale + offsetX);
    int y1 = (int)(LOGO_OUTLINE[(i + 1) * 2 + 1] * scale + offsetY);
    bootDrawLine(x0, y0, x1, y1, intensity, isOled);
  }
  // Close the outline
  {
    int i = LOGO_OUTLINE_COUNT - 1;
    int x0 = (int)(LOGO_OUTLINE[i * 2] * scale + offsetX);
    int y0 = (int)(LOGO_OUTLINE[i * 2 + 1] * scale + offsetY);
    int x1 = (int)(LOGO_OUTLINE[0] * scale + offsetX);
    int y1 = (int)(LOGO_OUTLINE[1] * scale + offsetY);
    bootDrawLine(x0, y0, x1, y1, intensity, isOled);
  }
  
  // Draw right decorative path
  for (int i = 0; i < LOGO_RIGHT_COUNT - 1; i++) {
    int x0 = (int)(LOGO_RIGHT[i * 2] * scale + offsetX);
    int y0 = (int)(LOGO_RIGHT[i * 2 + 1] * scale + offsetY);
    int x1 = (int)(LOGO_RIGHT[(i + 1) * 2] * scale + offsetX);
    int y1 = (int)(LOGO_RIGHT[(i + 1) * 2 + 1] * scale + offsetY);
    bootDrawLine(x0, y0, x1, y1, intensity, isOled);
  }
  
  // Draw inner circle
  int cx = (int)(LOGO_CIRCLE_X * scale + offsetX);
  int cy = (int)(LOGO_CIRCLE_Y * scale + offsetY);
  int cr = (int)(LOGO_CIRCLE_R * scale);
  if (cr > 0) bootDrawCircle(cx, cy, cr, intensity, isOled);
}

// Draw "NO SIGNAL" text (simplified pixel font)
// mirrorX: if true, draw text mirrored horizontally (for right panel pre-flip)
static void drawNoSignalText(int x, int y, uint8_t intensity, bool isOled, bool mirrorX = false) {
  // Simplified 5x7 font for "NO SIGNAL"
  // Each character is represented as 5 columns of 7 bits
  static const uint8_t FONT_N[] = {0x7F, 0x04, 0x08, 0x10, 0x7F};  // N
  static const uint8_t FONT_O[] = {0x3E, 0x41, 0x41, 0x41, 0x3E};  // O
  static const uint8_t FONT_S[] = {0x26, 0x49, 0x49, 0x49, 0x32};  // S (fixed: was horizontally mirrored)
  static const uint8_t FONT_I[] = {0x00, 0x41, 0x7F, 0x41, 0x00};  // I
  static const uint8_t FONT_G[] = {0x3E, 0x41, 0x49, 0x49, 0x3A};  // G
  static const uint8_t FONT_A[] = {0x7E, 0x09, 0x09, 0x09, 0x7E};  // A
  static const uint8_t FONT_L[] = {0x7F, 0x40, 0x40, 0x40, 0x40};  // L
  
  const uint8_t* letters[] = {FONT_N, FONT_O, nullptr, FONT_S, FONT_I, FONT_G, FONT_N, FONT_A, FONT_L};
  const int textWidth = 54;  // 9 chars * 6px spacing - 1
  
  int cx = x;
  for (int li = 0; li < 9; li++) {
    if (letters[li] == nullptr) {
      cx += 4;  // Space
      continue;
    }
    for (int col = 0; col < 5; col++) {
      uint8_t colData = letters[li][col];
      for (int row = 0; row < 7; row++) {
        if (colData & (1 << row)) {
          int drawX = cx + col;
          // If mirroring, flip X position relative to text start
          if (mirrorX) {
            drawX = x + (textWidth - 1) - (cx - x + col);
          }
          if (isOled) {
            if (intensity > 127) setPixelOLEDInternal(drawX, y + row, true);
          } else {
            setPixelHUB75(drawX, y + row, intensity, intensity, intensity);
          }
        }
      }
    }
    cx += 6;  // Character width + spacing
  }
}

// ============================================================
// PANEL DIAGNOSTIC TEST - CONFIGURABLE SETTINGS
// ============================================================
// Adjust these to find the correct panel configuration

// Panel 0 settings (left 64 pixels in buffer)
static bool PANEL0_MIRROR_X = false;  // Flip horizontally within panel
static bool PANEL0_MIRROR_Y = false;  // Flip vertically within panel
static bool PANEL0_SWAP = false;      // If true, panel 0 data goes to right side

// Panel 1 settings (right 64 pixels in buffer)
static bool PANEL1_MIRROR_X = true;   // Flip horizontally within panel
static bool PANEL1_MIRROR_Y = false;  // Flip vertically within panel

// Global settings
static bool GLOBAL_MIRROR_X = true;   // Mirror entire X axis before panel split
static bool GLOBAL_SWAP_PANELS = true; // Swap left/right panel positions

// RGB Channel order: 0=RGB, 1=RBG, 2=GRB, 3=GBR, 4=BRG, 5=BGR
static int RGB_ORDER = 1;  // Try RBG (swap G and B)

// Enable diagnostic test mode (set true to run test on boot)
static bool RUN_PANEL_TEST = false;  // VERIFIED: cyan square moves correctly with these settings

// Helper to set pixel (no RGB correction here - applied in presentHUB75Buffer)
static inline void setDiagPixel(int x, int y, uint8_t r, uint8_t g, uint8_t b) {
  if (x < 0 || x >= TOTAL_WIDTH || y < 0 || y >= TOTAL_HEIGHT) return;
  int idx = (y * TOTAL_WIDTH + x) * 3;
  
  // Write raw RGB - correction applied in presentHUB75Buffer
  hub75_buffer[idx + 0] = r;
  hub75_buffer[idx + 1] = g;
  hub75_buffer[idx + 2] = b;
}

// Present HUB75 buffer to display with configurable panel transforms
static void presentHUB75Buffer() {
  if (!hub75_ok || !hub75) return;
  
  // Update glitch state once per frame (if glitch overlay is enabled)
  // Glitch now works as an overlay on top of any shader
  bool glitchEnabled = g_glitchOverlayEnabled;
  if (glitchEnabled) {
    updateGlitchState();
  }
  
  // Pre-compute RGB channel indices based on RGB_ORDER
  // This moves the switch outside the pixel loops
  int rIdx = 0, gIdx = 1, bIdx = 2;
  switch (RGB_ORDER) {
    case 1: rIdx = 0; gIdx = 2; bIdx = 1; break;  // RBG
    case 2: rIdx = 1; gIdx = 0; bIdx = 2; break;  // GRB
    case 3: rIdx = 1; gIdx = 2; bIdx = 0; break;  // GBR
    case 4: rIdx = 2; gIdx = 0; bIdx = 1; break;  // BRG
    case 5: rIdx = 2; gIdx = 1; bIdx = 0; break;  // BGR
    default: break; // RGB (0)
  }
  
  // Fast path: no glitch effect
  if (!glitchEnabled || !g_glitchActive) {
    for (int y = 0; y < TOTAL_HEIGHT; y++) {
      for (int x = 0; x < TOTAL_WIDTH; x++) {
        // Start with buffer coordinates
        int bufX = GLOBAL_MIRROR_X ? (TOTAL_WIDTH - 1 - x) : x;
        int bufY = y;
        
        // Determine which panel this pixel belongs to (in buffer space)
        bool isRightPanel = (bufX >= PANEL_WIDTH);
        int panelX = isRightPanel ? (bufX - PANEL_WIDTH) : bufX;
        
        // Apply per-panel transforms
        int transformedPanelX = panelX;
        int transformedY = bufY;
        
        if (isRightPanel) {
          if (PANEL1_MIRROR_X) transformedPanelX = (PANEL_WIDTH - 1) - panelX;
          if (PANEL1_MIRROR_Y) transformedY = (TOTAL_HEIGHT - 1) - bufY;
        } else {
          if (PANEL0_MIRROR_X) transformedPanelX = (PANEL_WIDTH - 1) - panelX;
          if (PANEL0_MIRROR_Y) transformedY = (TOTAL_HEIGHT - 1) - bufY;
        }
        
        // Calculate display X position
        int displayX;
        if (GLOBAL_SWAP_PANELS) {
          displayX = isRightPanel ? transformedPanelX : (PANEL_WIDTH + transformedPanelX);
        } else {
          displayX = isRightPanel ? (PANEL_WIDTH + transformedPanelX) : transformedPanelX;
        }
        
        // Read from buffer (no glitch offset)
        int srcX = x;
        int idx;
        if (PANEL0_SWAP) {
          int readX = isRightPanel ? panelX : (PANEL_WIDTH + panelX);
          idx = (bufY * TOTAL_WIDTH + readX) * 3;
        } else {
          idx = (bufY * TOTAL_WIDTH + srcX) * 3;
        }
        
        uint8_t r = hub75_buffer[idx];
        uint8_t g = hub75_buffer[idx + 1];
        uint8_t b = hub75_buffer[idx + 2];
        
        // Apply RGB order using pre-computed indices
        uint8_t rgb[3] = {r, g, b};
        hub75->setPixel(displayX, transformedY, RGB(rgb[rIdx], rgb[gIdx], rgb[bIdx]));
      }
    }
  } else {
    // Slow path: glitch effect active
    for (int y = 0; y < TOTAL_HEIGHT; y++) {
      // Get glitch offset for this row
      int16_t glitchOffset = g_glitchRowOffsets[y];
      int16_t glitchChromaR = 0;
      int16_t glitchChromaB = 0;
      
      // Chromatic aberration: shift R and B channels relative to G
      if (g_glitchChromatic > 0 && glitchOffset != 0) {
        int16_t chromaAmount = 1 + (g_glitchChromatic * abs(glitchOffset) / 80);
        glitchChromaR = (glitchOffset > 0) ? -chromaAmount : chromaAmount;
        glitchChromaB = (glitchOffset > 0) ? chromaAmount : -chromaAmount;
      }
    
      for (int x = 0; x < TOTAL_WIDTH; x++) {
        int bufX = GLOBAL_MIRROR_X ? (TOTAL_WIDTH - 1 - x) : x;
        int bufY = y;
        
        bool isRightPanel = (bufX >= PANEL_WIDTH);
        int panelX = isRightPanel ? (bufX - PANEL_WIDTH) : bufX;
        
        int transformedPanelX = panelX;
        int transformedY = bufY;
        
        if (isRightPanel) {
          if (PANEL1_MIRROR_X) transformedPanelX = (PANEL_WIDTH - 1) - panelX;
          if (PANEL1_MIRROR_Y) transformedY = (TOTAL_HEIGHT - 1) - bufY;
        } else {
          if (PANEL0_MIRROR_X) transformedPanelX = (PANEL_WIDTH - 1) - panelX;
          if (PANEL0_MIRROR_Y) transformedY = (TOTAL_HEIGHT - 1) - bufY;
        }
        
        int displayX;
        if (GLOBAL_SWAP_PANELS) {
          displayX = isRightPanel ? transformedPanelX : (PANEL_WIDTH + transformedPanelX);
        } else {
          displayX = isRightPanel ? (PANEL_WIDTH + transformedPanelX) : transformedPanelX;
        }
        
        // Apply glitch offset to source X coordinate
        int srcX = x + glitchOffset;
        if (srcX < 0) srcX = 0;
        if (srcX >= TOTAL_WIDTH) srcX = TOTAL_WIDTH - 1;
        
        int idx;
        if (PANEL0_SWAP) {
          int readX = isRightPanel ? panelX : (PANEL_WIDTH + panelX);
          readX += glitchOffset;
          if (readX < 0) readX = 0;
          if (readX >= TOTAL_WIDTH) readX = TOTAL_WIDTH - 1;
          idx = (bufY * TOTAL_WIDTH + readX) * 3;
        } else {
          idx = (bufY * TOTAL_WIDTH + srcX) * 3;
        }
        
        // Read G channel (reference for chromatic aberration)
        uint8_t g_ch = hub75_buffer[idx + 1];
        
        // Read R with chromatic offset
        int srcXr = srcX + glitchChromaR;
        if (srcXr < 0) srcXr = 0;
        if (srcXr >= TOTAL_WIDTH) srcXr = TOTAL_WIDTH - 1;
        uint8_t r_ch = hub75_buffer[(bufY * TOTAL_WIDTH + srcXr) * 3];
        
        // Read B with chromatic offset
        int srcXb = srcX + glitchChromaB;
        if (srcXb < 0) srcXb = 0;
        if (srcXb >= TOTAL_WIDTH) srcXb = TOTAL_WIDTH - 1;
        uint8_t b_ch = hub75_buffer[(bufY * TOTAL_WIDTH + srcXb) * 3 + 2];
        
        // Apply RGB order
        uint8_t rgb[3] = {r_ch, g_ch, b_ch};
        hub75->setPixel(displayX, transformedY, RGB(rgb[rIdx], rgb[gIdx], rgb[bIdx]));
      }
    }
  }
  hub75->show();
}

// Draw panel diagnostic test pattern
// Red square: top-left (should appear at x=0-7, y=0-7)
// Blue square: bottom-right (should appear at x=120-127, y=24-31)
// Yellow square: center (should appear at x=60-67, y=12-19)
// Helper to draw a line using Bresenham's algorithm
static void drawDiagLine(int x0, int y0, int x1, int y1, uint8_t r, uint8_t g, uint8_t b) {
  int dx = abs(x1 - x0), sx = x0 < x1 ? 1 : -1;
  int dy = -abs(y1 - y0), sy = y0 < y1 ? 1 : -1;
  int err = dx + dy;
  while (true) {
    setDiagPixel(x0, y0, r, g, b);
    if (x0 == x1 && y0 == y1) break;
    int e2 = 2 * err;
    if (e2 >= dy) { err += dy; x0 += sx; }
    if (e2 <= dx) { err += dx; y0 += sy; }
  }
}

// Helper to draw a filled circle using midpoint algorithm
static void drawDiagCircle(int cx, int cy, int radius, uint8_t r, uint8_t g, uint8_t b) {
  for (int y = -radius; y <= radius; y++) {
    for (int x = -radius; x <= radius; x++) {
      if (x*x + y*y <= radius*radius) {
        setDiagPixel(cx + x, cy + y, r, g, b);
      }
    }
  }
}

// Helper to draw a filled rectangle
static void drawDiagRect(int x, int y, int w, int h, uint8_t r, uint8_t g, uint8_t b) {
  for (int py = y; py < y + h; py++) {
    for (int px = x; px < x + w; px++) {
      setDiagPixel(px, py, r, g, b);
    }
  }
}

// Diagnostic pattern for each panel: 4 corner squares + connecting lines + center shape
static void drawPanelDiagnostic() {
  // Clear buffer
  memset(hub75_buffer, 0, HUB75_BUFFER_SIZE);
  
  const int SQUARE_SIZE = 6;
  const int HALF_SQ = SQUARE_SIZE / 2;
  
  // For each panel (left=0, right=1)
  for (int panel = 0; panel < 2; panel++) {
    int panelX = panel * PANEL_WIDTH;  // 0 for left, 64 for right
    
    // Corner positions (relative to panel)
    // Top-left corner: (0, 0)
    // Top-right corner: (PANEL_WIDTH-1, 0)
    // Bottom-left corner: (0, TOTAL_HEIGHT-1)
    // Bottom-right corner: (PANEL_WIDTH-1, TOTAL_HEIGHT-1)
    
    int tlX = panelX + HALF_SQ;                      // Top-left center
    int tlY = HALF_SQ;
    int trX = panelX + PANEL_WIDTH - 1 - HALF_SQ;   // Top-right center
    int trY = HALF_SQ;
    int blX = panelX + HALF_SQ;                      // Bottom-left center
    int blY = TOTAL_HEIGHT - 1 - HALF_SQ;
    int brX = panelX + PANEL_WIDTH - 1 - HALF_SQ;   // Bottom-right center
    int brY = TOTAL_HEIGHT - 1 - HALF_SQ;
    
    // Draw 4 corner squares:
    // Top-right = RED
    drawDiagRect(trX - HALF_SQ, trY - HALF_SQ, SQUARE_SIZE, SQUARE_SIZE, 255, 0, 0);
    // Top-left = BLUE
    drawDiagRect(tlX - HALF_SQ, tlY - HALF_SQ, SQUARE_SIZE, SQUARE_SIZE, 0, 0, 255);
    // Bottom-left = GREEN
    drawDiagRect(blX - HALF_SQ, blY - HALF_SQ, SQUARE_SIZE, SQUARE_SIZE, 0, 255, 0);
    // Bottom-right = WHITE
    drawDiagRect(brX - HALF_SQ, brY - HALF_SQ, SQUARE_SIZE, SQUARE_SIZE, 255, 255, 255);
    
    // Draw connecting lines between square centers:
    // RED line: Red (top-right) to Blue (top-left) - top edge
    drawDiagLine(trX, trY, tlX, tlY, 255, 0, 0);
    // BLUE line: Blue (top-left) to Green (bottom-left) - left edge
    drawDiagLine(tlX, tlY, blX, blY, 0, 0, 255);
    // GREEN line: Green (bottom-left) to White (bottom-right) - bottom edge
    drawDiagLine(blX, blY, brX, brY, 0, 255, 0);
    // WHITE line: White (bottom-right) to Red (top-right) - right edge
    drawDiagLine(brX, brY, trX, trY, 255, 255, 255);
    
    // Center shape
    int centerX = panelX + PANEL_WIDTH / 2;
    int centerY = TOTAL_HEIGHT / 2;
    
    if (panel == 0) {
      // Left panel: draw a circle (outline)
      int radius = 8;
      for (int y = -radius; y <= radius; y++) {
        for (int x = -radius; x <= radius; x++) {
          int distSq = x*x + y*y;
          // Draw if on the circle edge (between inner and outer radius)
          if (distSq >= (radius-1)*(radius-1) && distSq <= radius*radius) {
            setDiagPixel(centerX + x, centerY + y, 255, 255, 0);  // YELLOW circle
          }
        }
      }
    } else {
      // Right panel: draw a square (outline)
      int halfSize = 8;
      // Top and bottom edges
      for (int x = -halfSize; x <= halfSize; x++) {
        setDiagPixel(centerX + x, centerY - halfSize, 255, 0, 255);  // MAGENTA
        setDiagPixel(centerX + x, centerY + halfSize, 255, 0, 255);
      }
      // Left and right edges
      for (int y = -halfSize; y <= halfSize; y++) {
        setDiagPixel(centerX - halfSize, centerY + y, 255, 0, 255);
        setDiagPixel(centerX + halfSize, centerY + y, 255, 0, 255);
      }
    }
  }
  
  // Draw panel divider line (between the two panels)
  for (int y = 0; y < TOTAL_HEIGHT; y++) {
    setDiagPixel(63, y, 128, 128, 128);  // Gray divider
    setDiagPixel(64, y, 128, 128, 128);
  }
  
  // Print current config to log
  ESP_LOGI(TAG, "=== PANEL DIAGNOSTIC ===");
  ESP_LOGI(TAG, "RGB_ORDER=%d (0=RGB,1=RBG,2=GRB,3=GBR,4=BRG,5=BGR)", RGB_ORDER);
  ESP_LOGI(TAG, "Panel0: MirrorX=%d MirrorY=%d Swap=%d", PANEL0_MIRROR_X, PANEL0_MIRROR_Y, PANEL0_SWAP);
  ESP_LOGI(TAG, "Panel1: MirrorX=%d MirrorY=%d", PANEL1_MIRROR_X, PANEL1_MIRROR_Y);
  ESP_LOGI(TAG, "Global: MirrorX=%d SwapPanels=%d", GLOBAL_MIRROR_X, GLOBAL_SWAP_PANELS);
  ESP_LOGI(TAG, "Expected: RED=top-left, BLUE=bottom-right, YELLOW=center");
  ESP_LOGI(TAG, "GREEN line = panel boundary (x=63/64)");
  ESP_LOGI(TAG, "WHITE logos centered on each panel");
  
  presentHUB75Buffer();
  
  // === OLED Display ===
  // Top section (y=0-47): Reference logos (how they SHOULD look)
  // Middle section (y=48): Divider line
  // Bottom section (y=49-80): HUB75 buffer replication 1:1 (32 rows)
  // Lower section (y=88-119): Second copy showing what HUB75 buffer looks like after transforms
  memset(oled_buffer, 0, OLED_BUFFER_SIZE);
  
  // Draw reference logos on OLED top area (y=8-40)
  // These are drawn directly without any panel transforms
  float oledLogoScale = 0.10f;
  float oledLogoW = LOGO_WIDTH * oledLogoScale;
  float oledLogoH = LOGO_HEIGHT * oledLogoScale;
  
  // Left reference logo (x=0-63, y=8-40)
  float oled_left_offsetX = (64 - oledLogoW) / 2.0f;
  float oled_left_offsetY = 8 + (32 - oledLogoH) / 2.0f;
  
  for (int i = 0; i < LOGO_OUTLINE_COUNT - 1; i++) {
    int x0 = (int)(LOGO_OUTLINE[i * 2] * oledLogoScale + oled_left_offsetX);
    int y0 = (int)(LOGO_OUTLINE[i * 2 + 1] * oledLogoScale + oled_left_offsetY);
    int x1 = (int)(LOGO_OUTLINE[(i + 1) * 2] * oledLogoScale + oled_left_offsetX);
    int y1 = (int)(LOGO_OUTLINE[(i + 1) * 2 + 1] * oledLogoScale + oled_left_offsetY);
    // Bresenham line for OLED
    int dx = abs(x1 - x0), sx = x0 < x1 ? 1 : -1;
    int dy = -abs(y1 - y0), sy = y0 < y1 ? 1 : -1;
    int err = dx + dy;
    while (true) {
      if (x0 >= 0 && x0 < OLED_WIDTH && y0 >= 0 && y0 < OLED_HEIGHT) {
        int byteIdx = (y0 / 8) * OLED_WIDTH + x0;
        int bitIdx = y0 % 8;
        oled_buffer[byteIdx] |= (1 << bitIdx);
      }
      if (x0 == x1 && y0 == y1) break;
      int e2 = 2 * err;
      if (e2 >= dy) { err += dy; x0 += sx; }
      if (e2 <= dx) { err += dx; y0 += sy; }
    }
  }
  
  // Right reference logo (x=64-127, y=8-40)
  float oled_right_offsetX = 64 + (64 - oledLogoW) / 2.0f;
  float oled_right_offsetY = 8 + (32 - oledLogoH) / 2.0f;
  
  for (int i = 0; i < LOGO_OUTLINE_COUNT - 1; i++) {
    int x0 = (int)(LOGO_OUTLINE[i * 2] * oledLogoScale + oled_right_offsetX);
    int y0 = (int)(LOGO_OUTLINE[i * 2 + 1] * oledLogoScale + oled_right_offsetY);
    int x1 = (int)(LOGO_OUTLINE[(i + 1) * 2] * oledLogoScale + oled_right_offsetX);
    int y1 = (int)(LOGO_OUTLINE[(i + 1) * 2 + 1] * oledLogoScale + oled_right_offsetY);
    int dx = abs(x1 - x0), sx = x0 < x1 ? 1 : -1;
    int dy = -abs(y1 - y0), sy = y0 < y1 ? 1 : -1;
    int err = dx + dy;
    while (true) {
      if (x0 >= 0 && x0 < OLED_WIDTH && y0 >= 0 && y0 < OLED_HEIGHT) {
        int byteIdx = (y0 / 8) * OLED_WIDTH + x0;
        int bitIdx = y0 % 8;
        oled_buffer[byteIdx] |= (1 << bitIdx);
      }
      if (x0 == x1 && y0 == y1) break;
      int e2 = 2 * err;
      if (e2 >= dy) { err += dy; x0 += sx; }
      if (e2 <= dx) { err += dx; y0 += sy; }
    }
  }
  
  // Draw horizontal line separating reference from replication (y=48)
  for (int x = 0; x < OLED_WIDTH; x++) {
    int byteIdx = (48 / 8) * OLED_WIDTH + x;
    int bitIdx = 48 % 8;
    oled_buffer[byteIdx] |= (1 << bitIdx);
  }
  
  // Draw vertical line at center (x=64) for reference area
  for (int y = 0; y < 48; y++) {
    int byteIdx = (y / 8) * OLED_WIDTH + 64;
    int bitIdx = y % 8;
    oled_buffer[byteIdx] |= (1 << bitIdx);
  }
  
  // HUB75 buffer replication 1:1 (y=49-80, which is 32 rows for 128x32)
  // This shows what's in the HUB75 buffer - mirrored V then H to match physical display
  int replicationY = 49;
  for (int y = 0; y < TOTAL_HEIGHT; y++) {
    for (int x = 0; x < TOTAL_WIDTH; x++) {
      // Mirror vertically (flip Y), then horizontally (flip X)
      int srcX = (TOTAL_WIDTH - 1) - x;   // Horizontal mirror
      int srcY = y;                        // No vertical flip - try just horizontal
      int idx = (srcY * TOTAL_WIDTH + srcX) * 3;
      uint8_t r = hub75_buffer[idx + 0];
      uint8_t g = hub75_buffer[idx + 1];
      uint8_t b = hub75_buffer[idx + 2];
      
      // Luminance threshold (lowered to catch pure blue which has lum=28)
      uint16_t lum = (77 * r + 150 * g + 29 * b) >> 8;
      if (lum >= 16) {
        int oledY = replicationY + y;
        if (oledY < OLED_HEIGHT) {
          int byteIdx = (oledY / 8) * OLED_WIDTH + x;
          int bitIdx = oledY % 8;
          oled_buffer[byteIdx] |= (1 << bitIdx);
        }
      }
    }
  }
  
  // Update OLED directly (task not running yet)
  if (oled_ok && oled) {
    memcpy(oled->getBuffer(), oled_buffer, OLED_BUFFER_SIZE);
    oled->updateDisplay();
  }
  
  ESP_LOGI(TAG, "OLED: Top=Reference logos, Bottom=Raw HUB75 buffer (1:1)");
}

// Calculate logo scale to fit within constraints:
// - Max 50% of screen width
// - Max 80% of screen height
// Returns scale factor and offsets for centering
static void calculateLogoFit(int screenW, int screenH, float& scale, float& offsetX, float& offsetY) {
  float maxW = screenW * 0.5f;   // 50% of width
  float maxH = screenH * 0.8f;   // 80% of height
  
  // Calculate scale to fit within both constraints
  float scaleW = maxW / LOGO_WIDTH;
  float scaleH = maxH / LOGO_HEIGHT;
  scale = (scaleW < scaleH) ? scaleW : scaleH;  // Use smaller scale
  
  // Calculate centered position
  float scaledW = LOGO_WIDTH * scale;
  float scaledH = LOGO_HEIGHT * scale;
  offsetX = (screenW - scaledW) / 2.0f;
  offsetY = (screenH - scaledH) / 2.0f;
}

// Update boot animation - returns true if still in boot/no-signal state
static bool updateBootAnimation() {
  int64_t now = esp_timer_get_time();
  
  switch (bootState) {
    case BootState::FADE_IN: {
      // If CPU connected during fade-in, skip directly to RUNNING
      if (cpuConnected) {
        bootState = BootState::RUNNING;
        ESP_LOGI(TAG, "Boot: CPU connected during fade-in, skipping to normal operation");
        return false;
      }
      
      int64_t elapsed = now - bootStartTime;
      float progress = (float)elapsed / (float)FADE_DURATION_US;
      if (progress >= 1.0f) progress = 1.0f;
      
      uint8_t intensity = (uint8_t)(progress * 255.0f);
      
      // Clear buffers
      memset(hub75_buffer, 0, HUB75_BUFFER_SIZE);
      memset(oled_buffer, 0, OLED_BUFFER_SIZE);
      
      // Draw logo on each HUB75 panel (2 panels, 64x32 each)
      float hub75_scale, hub75_offsetX, hub75_offsetY;
      calculateLogoFit(PANEL_WIDTH, PANEL_HEIGHT, hub75_scale, hub75_offsetX, hub75_offsetY);
      // Left panel (0-63)
      drawLogoScaled(hub75_scale, hub75_offsetX, hub75_offsetY, intensity, false);
      // Right panel (64-127)
      drawLogoScaled(hub75_scale, hub75_offsetX + PANEL_WIDTH, hub75_offsetY, intensity, false);
      
      // Draw logo on OLED (128x128) - single display
      float oled_scale, oled_offsetX, oled_offsetY;
      calculateLogoFit(OLED_WIDTH, OLED_HEIGHT, oled_scale, oled_offsetX, oled_offsetY);
      drawLogoScaled(oled_scale, oled_offsetX, oled_offsetY, intensity, true);
      
      // Present displays
      presentHUB75Buffer();
      presentOLEDBuffer();
      
      if (progress >= 1.0f) {
        bootState = BootState::HOLD;
        ESP_LOGI(TAG, "Boot: Fade-in complete, waiting for CPU...");
      }
      return true;
    }
    
    case BootState::HOLD: {
      // Check if CPU has connected - skip directly to RUNNING to avoid display conflict
      if (cpuConnected) {
        bootState = BootState::RUNNING;
        ESP_LOGI(TAG, "Boot: CPU connected, skipping to normal operation");
        return false;  // Immediately let CPU take control
      }
      
      // Timeout: if CPU doesn't connect within 5 seconds of boot, show NO SIGNAL
      int64_t holdElapsed = now - bootStartTime - FADE_DURATION_US;
      if (!cpuConnected && holdElapsed > 5000000) {  // 5 seconds after fade-in
        bootState = BootState::NO_SIGNAL;
        ESP_LOGW(TAG, "Boot: CPU connection timeout, showing No Signal");
      }
      
      // Keep displaying logo at full brightness
      memset(hub75_buffer, 0, HUB75_BUFFER_SIZE);
      memset(oled_buffer, 0, OLED_BUFFER_SIZE);
      
      // Draw logo on each HUB75 panel (2 panels, 64x32 each)
      float hub75_scale, hub75_offsetX, hub75_offsetY;
      calculateLogoFit(PANEL_WIDTH, PANEL_HEIGHT, hub75_scale, hub75_offsetX, hub75_offsetY);
      // Left panel (0-63)
      drawLogoScaled(hub75_scale, hub75_offsetX, hub75_offsetY, 255, false);
      // Right panel (64-127)
      drawLogoScaled(hub75_scale, hub75_offsetX + PANEL_WIDTH, hub75_offsetY, 255, false);
      
      // Draw logo on OLED (128x128) - single display
      float oled_scale, oled_offsetX, oled_offsetY;
      calculateLogoFit(OLED_WIDTH, OLED_HEIGHT, oled_scale, oled_offsetX, oled_offsetY);
      drawLogoScaled(oled_scale, oled_offsetX, oled_offsetY, 255, true);
      
      // Present displays
      presentHUB75Buffer();
      presentOLEDBuffer();
      return true;
    }
    
    case BootState::FADE_OUT: {
      int64_t elapsed = now - fadeOutStartTime;
      float progress = (float)elapsed / (float)FADE_DURATION_US;
      if (progress >= 1.0f) progress = 1.0f;
      
      uint8_t intensity = (uint8_t)((1.0f - progress) * 255.0f);
      
      // Clear buffers
      memset(hub75_buffer, 0, HUB75_BUFFER_SIZE);
      memset(oled_buffer, 0, OLED_BUFFER_SIZE);
      
      // Draw fading logo on each HUB75 panel (2 panels, 64x32 each)
      float hub75_scale, hub75_offsetX, hub75_offsetY;
      calculateLogoFit(PANEL_WIDTH, PANEL_HEIGHT, hub75_scale, hub75_offsetX, hub75_offsetY);
      // Left panel (0-63)
      drawLogoScaled(hub75_scale, hub75_offsetX, hub75_offsetY, intensity, false);
      // Right panel (64-127)
      drawLogoScaled(hub75_scale, hub75_offsetX + PANEL_WIDTH, hub75_offsetY, intensity, false);
      
      // Draw fading logo on OLED - single display
      float oled_scale, oled_offsetX, oled_offsetY;
      calculateLogoFit(OLED_WIDTH, OLED_HEIGHT, oled_scale, oled_offsetX, oled_offsetY);
      drawLogoScaled(oled_scale, oled_offsetX, oled_offsetY, intensity, true);
      
      // Present displays
      presentHUB75Buffer();
      presentOLEDBuffer();
      
      if (progress >= 1.0f) {
        bootState = BootState::RUNNING;
        ESP_LOGI(TAG, "Boot: Splash complete, running normally");
      }
      return true;
    }
    
    case BootState::RUNNING: {
      // Check for CPU timeout - only display commands reset this, not PINGs
      // If we've never received a display command (lastDisplayCommandTime == 0), 
      // use bootStartTime as the reference point
      int64_t refTime = (lastDisplayCommandTime > 0) ? lastDisplayCommandTime : bootStartTime;
      if ((now - refTime) > NO_SIGNAL_TIMEOUT_US) {
        bootState = BootState::NO_SIGNAL;
        cpuConnected = false;
        ESP_LOGW(TAG, "CPU disconnected (no display commands for %.1fs) - showing No Signal",
                 (float)(now - refTime) / 1000000.0f);
      }
      return false;  // Normal operation
    }
    
    case BootState::NO_SIGNAL: {
      // Swaying "NO SIGNAL" animation to prevent burn-in
      float t = (float)now / 1000000.0f;  // Time in seconds (proper float division)
      
      // Clear buffers
      memset(hub75_buffer, 0, HUB75_BUFFER_SIZE);
      memset(oled_buffer, 0, OLED_BUFFER_SIZE);
      
      // "NO SIGNAL" text dimensions: 9 chars * 6px = 54px wide, 7px tall
      const int textW = 54;
      const int textH = 7;
      
      // HUB75: Sway within bounds of each panel (64x32 each)
      int hub75_maxSwayX = (PANEL_WIDTH - textW) / 2 - 2;  // Leave 2px margin
      int hub75_maxSwayY = (PANEL_HEIGHT - textH) / 2 - 2;
      if (hub75_maxSwayX < 0) hub75_maxSwayX = 0;
      if (hub75_maxSwayY < 0) hub75_maxSwayY = 0;
      float hub75_swayX = sinf(t * 0.5f) * hub75_maxSwayX;
      float hub75_swayY = cosf(t * 0.3f) * hub75_maxSwayY;
      int hub75_textX = (PANEL_WIDTH - textW) / 2 + (int)hub75_swayX;
      int hub75_textY = (PANEL_HEIGHT - textH) / 2 + (int)hub75_swayY;
      // Panel configuration: GLOBAL_MIRROR_X=true, GLOBAL_SWAP_PANELS=true, PANEL1_MIRROR_X=true
      // blendPixelHUB75 no longer does internal mirroring, so we need to pre-mirror both texts
      // to compensate for the presentHUB75Buffer transform chain
      drawNoSignalText(hub75_textX, hub75_textY, 180, false, true);    // Buffer LEFT - pre-mirror
      drawNoSignalText(hub75_textX + PANEL_WIDTH, hub75_textY, 180, false, true);  // Buffer RIGHT - pre-mirror
      
      // OLED: Single display, larger sway range since screen is bigger
      int oled_maxSwayX = (OLED_WIDTH - textW) / 2 - 4;
      int oled_maxSwayY = (OLED_HEIGHT - textH) / 2 - 4;
      float oled_swayX = sinf(t * 0.5f) * oled_maxSwayX;
      float oled_swayY = cosf(t * 0.3f) * oled_maxSwayY;
      int oled_textX = (OLED_WIDTH - textW) / 2 + (int)oled_swayX;
      int oled_textY = (OLED_HEIGHT - textH) / 2 + (int)oled_swayY;
      drawNoSignalText(oled_textX, oled_textY, 255, true);
      
      // Present displays
      presentHUB75Buffer();
      presentOLEDBuffer();
      
      // Check if CPU reconnected
      if (cpuConnected) {
        bootState = BootState::RUNNING;
        ESP_LOGI(TAG, "CPU reconnected - resuming normal operation");
        return false;
      }
      
      vTaskDelay(pdMS_TO_TICKS(30));  // ~30 FPS for animation
      return true;
    }
  }
  return false;
}

// ============================================================
// Drawing Primitives (with Fast Anti-Aliasing)
// ============================================================

// Helper: Clamp float to 0-1 range
static inline float clamp01(float x) {
  return (x < 0.0f) ? 0.0f : (x > 1.0f) ? 1.0f : x;
}

// Helper: Fractional part
static inline float fract(float x) {
  return x - floorf(x);
}

// Fast anti-aliased line using Xiaolin Wu algorithm with float coordinates
// This walks along the line and only touches pixels near the line (O(length) not O(area))
static void drawLineAA(float x0, float y0, float x1, float y1, uint8_t r, uint8_t g, uint8_t b) {
  bool steep = fabsf(y1 - y0) > fabsf(x1 - x0);
  
  if (steep) {
    std::swap(x0, y0);
    std::swap(x1, y1);
  }
  if (x0 > x1) {
    std::swap(x0, x1);
    std::swap(y0, y1);
  }
  
  float dx = x1 - x0;
  float dy = y1 - y0;
  float gradient = (dx < 0.0001f) ? 1.0f : dy / dx;
  
  // First endpoint
  float xend = roundf(x0);
  float yend = y0 + gradient * (xend - x0);
  float xgap = 1.0f - fract(x0 + 0.5f);
  int xpxl1 = (int)xend;
  int ypxl1 = (int)floorf(yend);
  float frac1 = fract(yend);
  
  if (steep) {
    blendPixelHUB75(ypxl1, xpxl1, r, g, b, (uint8_t)((1.0f - frac1) * xgap * 255.0f));
    blendPixelHUB75(ypxl1 + 1, xpxl1, r, g, b, (uint8_t)(frac1 * xgap * 255.0f));
  } else {
    blendPixelHUB75(xpxl1, ypxl1, r, g, b, (uint8_t)((1.0f - frac1) * xgap * 255.0f));
    blendPixelHUB75(xpxl1, ypxl1 + 1, r, g, b, (uint8_t)(frac1 * xgap * 255.0f));
  }
  
  float intery = yend + gradient;
  
  // Second endpoint
  xend = roundf(x1);
  yend = y1 + gradient * (xend - x1);
  xgap = fract(x1 + 0.5f);
  int xpxl2 = (int)xend;
  int ypxl2 = (int)floorf(yend);
  float frac2 = fract(yend);
  
  if (steep) {
    blendPixelHUB75(ypxl2, xpxl2, r, g, b, (uint8_t)((1.0f - frac2) * xgap * 255.0f));
    blendPixelHUB75(ypxl2 + 1, xpxl2, r, g, b, (uint8_t)(frac2 * xgap * 255.0f));
  } else {
    blendPixelHUB75(xpxl2, ypxl2, r, g, b, (uint8_t)((1.0f - frac2) * xgap * 255.0f));
    blendPixelHUB75(xpxl2, ypxl2 + 1, r, g, b, (uint8_t)(frac2 * xgap * 255.0f));
  }
  
  // Main line body
  if (steep) {
    for (int x = xpxl1 + 1; x < xpxl2; x++) {
      int y = (int)floorf(intery);
      float f = fract(intery);
      blendPixelHUB75(y, x, r, g, b, (uint8_t)((1.0f - f) * 255.0f));
      blendPixelHUB75(y + 1, x, r, g, b, (uint8_t)(f * 255.0f));
      intery += gradient;
    }
  } else {
    for (int x = xpxl1 + 1; x < xpxl2; x++) {
      int y = (int)floorf(intery);
      float f = fract(intery);
      blendPixelHUB75(x, y, r, g, b, (uint8_t)((1.0f - f) * 255.0f));
      blendPixelHUB75(x, y + 1, r, g, b, (uint8_t)(f * 255.0f));
      intery += gradient;
    }
  }
}

// Non-AA Bresenham line (used for OLED or when AA disabled)
static void drawLineBasic(int x0, int y0, int x1, int y1, uint8_t r, uint8_t g, uint8_t b) {
  int dx = abs(x1 - x0);
  int dy = -abs(y1 - y0);
  int sx = x0 < x1 ? 1 : -1;
  int sy = y0 < y1 ? 1 : -1;
  int err = dx + dy;
  
  while (true) {
    setPixel(x0, y0, r, g, b);
    if (x0 == x1 && y0 == y1) break;
    int e2 = 2 * err;
    if (e2 >= dy) { err += dy; x0 += sx; }
    if (e2 <= dx) { err += dx; y0 += sy; }
  }
}

// Main line function with integer coords - uses AA for HUB75 when enabled
static void drawLine(int x0, int y0, int x1, int y1, uint8_t r, uint8_t g, uint8_t b) {
  if (aa_enabled && gpu.target == 0) {
    drawLineAA((float)x0, (float)y0, (float)x1, (float)y1, r, g, b);
  } else {
    drawLineBasic(x0, y0, x1, y1, r, g, b);
  }
}

// Float coordinate line - enables sub-pixel smooth movement
static void drawLineF(float x0, float y0, float x1, float y1, uint8_t r, uint8_t g, uint8_t b) {
  if (aa_enabled && gpu.target == 0) {
    drawLineAA(x0, y0, x1, y1, r, g, b);
  } else {
    drawLineBasic((int)roundf(x0), (int)roundf(y0), (int)roundf(x1), (int)roundf(y1), r, g, b);
  }
}

static void drawRect(int x, int y, int w, int h, uint8_t r, uint8_t g, uint8_t b) {
  drawLine(x, y, x + w - 1, y, r, g, b);
  drawLine(x + w - 1, y, x + w - 1, y + h - 1, r, g, b);
  drawLine(x + w - 1, y + h - 1, x, y + h - 1, r, g, b);
  drawLine(x, y + h - 1, x, y, r, g, b);
}

// Float coordinate rect
static void drawRectF(float x, float y, float w, float h, uint8_t r, uint8_t g, uint8_t b) {
  drawLineF(x, y, x + w, y, r, g, b);
  drawLineF(x + w, y, x + w, y + h, r, g, b);
  drawLineF(x + w, y + h, x, y + h, r, g, b);
  drawLineF(x, y + h, x, y, r, g, b);
}

static void fillRect(int x, int y, int w, int h, uint8_t r, uint8_t g, uint8_t b) {
  for (int py = y; py < y + h; py++) {
    for (int px = x; px < x + w; px++) {
      setPixel(px, py, r, g, b);
    }
  }
}

// Fast AA circle using midpoint algorithm with distance-based alpha
static void drawCircleAA(float cx, float cy, float radius, uint8_t r, uint8_t g, uint8_t b) {
  // Scan only pixels near the circle edge
  int ir = (int)ceilf(radius);
  int icx = (int)roundf(cx);
  int icy = (int)roundf(cy);
  
  for (int py = icy - ir - 1; py <= icy + ir + 1; py++) {
    if (py < 0 || py >= TOTAL_HEIGHT) continue;
    for (int px = icx - ir - 1; px <= icx + ir + 1; px++) {
      if (px < 0 || px >= TOTAL_WIDTH) continue;
      
      float dx = px + 0.5f - cx;
      float dy = py + 0.5f - cy;
      float dist = sqrtf(dx * dx + dy * dy);
      float diff = fabsf(dist - radius);
      
      // Only draw pixels within 1 pixel of the circle edge
      if (diff < 1.0f) {
        uint8_t alpha = (uint8_t)((1.0f - diff) * 255.0f);
        blendPixelHUB75(px, py, r, g, b, alpha);
      }
    }
  }
}

// Basic Bresenham circle (for OLED or when AA disabled)
static void drawCircleBasic(int cx, int cy, int radius, uint8_t r, uint8_t g, uint8_t b) {
  int x = radius;
  int y = 0;
  int err = 0;
  
  while (x >= y) {
    setPixel(cx + x, cy + y, r, g, b);
    setPixel(cx + y, cy + x, r, g, b);
    setPixel(cx - y, cy + x, r, g, b);
    setPixel(cx - x, cy + y, r, g, b);
    setPixel(cx - x, cy - y, r, g, b);
    setPixel(cx - y, cy - x, r, g, b);
    setPixel(cx + y, cy - x, r, g, b);
    setPixel(cx + x, cy - y, r, g, b);
    
    y++;
    err += 1 + 2 * y;
    if (2 * (err - x) + 1 > 0) {
      x--;
      err += 1 - 2 * x;
    }
  }
}

// Main circle function (integer coords)
static void drawCircle(int cx, int cy, int radius, uint8_t r, uint8_t g, uint8_t b) {
  if (aa_enabled && gpu.target == 0) {
    drawCircleAA((float)cx, (float)cy, (float)radius, r, g, b);
  } else {
    drawCircleBasic(cx, cy, radius, r, g, b);
  }
}

// Float coordinate circle - enables sub-pixel smooth movement
static void drawCircleF(float cx, float cy, float radius, uint8_t r, uint8_t g, uint8_t b) {
  if (aa_enabled && gpu.target == 0) {
    drawCircleAA(cx, cy, radius, r, g, b);
  } else {
    drawCircleBasic((int)roundf(cx), (int)roundf(cy), (int)roundf(radius), r, g, b);
  }
}

// Filled circle with AA edge
static void fillCircle(float cx, float cy, float radius, uint8_t r, uint8_t g, uint8_t b) {
  int minX = (int)floorf(cx - radius - 1);
  int maxX = (int)ceilf(cx + radius + 1);
  int minY = (int)floorf(cy - radius - 1);
  int maxY = (int)ceilf(cy + radius + 1);
  
  if (minX < 0) minX = 0;
  if (minY < 0) minY = 0;
  if (maxX >= TOTAL_WIDTH) maxX = TOTAL_WIDTH - 1;
  if (maxY >= TOTAL_HEIGHT) maxY = TOTAL_HEIGHT - 1;
  
  for (int py = minY; py <= maxY; py++) {
    for (int px = minX; px <= maxX; px++) {
      float dx = px + 0.5f - cx;
      float dy = py + 0.5f - cy;
      float dist = sqrtf(dx * dx + dy * dy);
      
      if (aa_enabled && gpu.target == 0) {
        // AA edge
        if (dist <= radius - 0.5f) {
          setPixelHUB75(px, py, r, g, b);
        } else if (dist < radius + 0.5f) {
          uint8_t alpha = (uint8_t)((radius + 0.5f - dist) * 255.0f);
          blendPixelHUB75(px, py, r, g, b, alpha);
        }
      } else {
        if (dist <= radius) {
          setPixel(px, py, r, g, b);
        }
      }
    }
  }
}

static void fillPolygon(int n, int16_t* vx, int16_t* vy, uint8_t r, uint8_t g, uint8_t b) {
  // Find bounding box
  int minY = vy[0], maxY = vy[0];
  for (int i = 1; i < n; i++) {
    if (vy[i] < minY) minY = vy[i];
    if (vy[i] > maxY) maxY = vy[i];
  }
  
  // Scanline fill
  for (int y = minY; y <= maxY; y++) {
    int nodes[32];
    int nodeCount = 0;
    
    int j = n - 1;
    for (int i = 0; i < n; i++) {
      if ((vy[i] < y && vy[j] >= y) || (vy[j] < y && vy[i] >= y)) {
        nodes[nodeCount++] = vx[i] + (y - vy[i]) * (vx[j] - vx[i]) / (vy[j] - vy[i]);
      }
      j = i;
    }
    
    // Sort nodes
    for (int i = 0; i < nodeCount - 1; i++) {
      for (int j = i + 1; j < nodeCount; j++) {
        if (nodes[i] > nodes[j]) {
          int tmp = nodes[i];
          nodes[i] = nodes[j];
          nodes[j] = tmp;
        }
      }
    }
    
    // Fill between pairs
    for (int i = 0; i < nodeCount; i += 2) {
      if (i + 1 < nodeCount) {
        for (int x = nodes[i]; x <= nodes[i + 1]; x++) {
          setPixel(x, y, r, g, b);
        }
      }
    }
  }
}

// Helper: Accumulate color to a pixel with weight (for splatting)
// Uses additive blending to accumulate contributions from multiple sprite pixels
static float splat_r[TOTAL_WIDTH * TOTAL_HEIGHT];
static float splat_g[TOTAL_WIDTH * TOTAL_HEIGHT];
static float splat_b[TOTAL_WIDTH * TOTAL_HEIGHT];
static float splat_w[TOTAL_WIDTH * TOTAL_HEIGHT];

// Helper: Track which panel each sprite is being drawn to (for splat isolation)
static int currentSpritePanel = -1;  // 0=left (x<64), 1=right (x>=64), -1=both

static inline void splatPixel(int x, int y, float r, float g, float b, float weight) {
  if (x < 0 || x >= TOTAL_WIDTH || y < 0 || y >= TOTAL_HEIGHT) return;
  
  // CRITICAL: Prevent cross-panel bleed from bilinear splatting
  // If sprite center is on left panel, don't splat to right panel and vice versa
  if (currentSpritePanel == 0 && x >= PANEL_WIDTH) return;   // Left sprite, don't bleed right
  if (currentSpritePanel == 1 && x < PANEL_WIDTH) return;    // Right sprite, don't bleed left
  
  int idx = y * TOTAL_WIDTH + x;
  splat_r[idx] += r * weight;
  splat_g[idx] += g * weight;
  splat_b[idx] += b * weight;
  splat_w[idx] += weight;
}

static inline void clearSplatBuffer() {
  memset(splat_r, 0, sizeof(splat_r));
  memset(splat_g, 0, sizeof(splat_g));
  memset(splat_b, 0, sizeof(splat_b));
  memset(splat_w, 0, sizeof(splat_w));
}

static inline void flushSplatBuffer(int minX, int minY, int maxX, int maxY) {
  for (int y = minY; y <= maxY; y++) {
    for (int x = minX; x <= maxX; x++) {
      if (x < 0 || x >= TOTAL_WIDTH || y < 0 || y >= TOTAL_HEIGHT) continue;
      int idx = y * TOTAL_WIDTH + x;
      if (splat_w[idx] > 0.001f) {
        // Normalize accumulated color by total weight
        uint8_t r = (uint8_t)fminf(255.0f, splat_r[idx] / splat_w[idx]);
        uint8_t g = (uint8_t)fminf(255.0f, splat_g[idx] / splat_w[idx]);
        uint8_t b = (uint8_t)fminf(255.0f, splat_b[idx] / splat_w[idx]);
        
        // Alpha based on coverage (clamped to 1.0)
        float coverage = fminf(1.0f, splat_w[idx]);
        uint8_t alpha = (uint8_t)(coverage * 255.0f);
        
        if (alpha > 250) {
          setPixelHUB75(x, y, r, g, b);
        } else if (alpha > 4) {
          blendPixelHUB75(x, y, r, g, b, alpha);
        }
      }
    }
  }
}

// Bilinear sample from RGB sprite (for supersampling)
static void sampleSpriteRGB(Sprite& s, float fx, float fy, uint8_t& r, uint8_t& g, uint8_t& b) {
  int x0 = (int)floorf(fx);
  int y0 = (int)floorf(fy);
  int x1 = x0 + 1;
  int y1 = y0 + 1;
  float dx = fx - x0;
  float dy = fy - y0;
  
  // Clamp to sprite bounds
  x0 = (x0 < 0) ? 0 : (x0 >= s.width) ? s.width - 1 : x0;
  y0 = (y0 < 0) ? 0 : (y0 >= s.height) ? s.height - 1 : y0;
  x1 = (x1 < 0) ? 0 : (x1 >= s.width) ? s.width - 1 : x1;
  y1 = (y1 < 0) ? 0 : (y1 >= s.height) ? s.height - 1 : y1;
  
  // Get four corner pixels
  int idx00 = (y0 * s.width + x0) * 3;
  int idx10 = (y0 * s.width + x1) * 3;
  int idx01 = (y1 * s.width + x0) * 3;
  int idx11 = (y1 * s.width + x1) * 3;
  
  // Bilinear interpolation
  float w00 = (1 - dx) * (1 - dy);
  float w10 = dx * (1 - dy);
  float w01 = (1 - dx) * dy;
  float w11 = dx * dy;
  
  r = (uint8_t)(s.data[idx00 + 0] * w00 + s.data[idx10 + 0] * w10 + 
                s.data[idx01 + 0] * w01 + s.data[idx11 + 0] * w11);
  g = (uint8_t)(s.data[idx00 + 1] * w00 + s.data[idx10 + 1] * w10 + 
                s.data[idx01 + 1] * w01 + s.data[idx11 + 1] * w11);
  b = (uint8_t)(s.data[idx00 + 2] * w00 + s.data[idx10 + 2] * w10 + 
                s.data[idx01 + 2] * w01 + s.data[idx11 + 2] * w11);
}

static void blitSprite(int id, int dx, int dy) {
  if (id < 0 || id >= MAX_SPRITES || !gpu.sprites[id].valid) return;
  
  Sprite& s = gpu.sprites[id];
  
  if (s.format == 0 && gpu.target == 0) {
    // RGB sprite to HUB75
    if (aa_enabled) {
      // Supersampled blit: 2x2 samples per output pixel
      for (int y = 0; y < s.height; y++) {
        for (int x = 0; x < s.width; x++) {
          uint16_t tr = 0, tg = 0, tb = 0;
          // Sample at 4 sub-pixel positions
          for (int sy = 0; sy < 2; sy++) {
            for (int sx = 0; sx < 2; sx++) {
              uint8_t sr, sg, sb;
              float fx = x + sx * 0.5f;
              float fy = y + sy * 0.5f;
              sampleSpriteRGB(s, fx, fy, sr, sg, sb);
              tr += sr; tg += sg; tb += sb;
            }
          }
          // Average the 4 samples
          uint8_t pr = tr >> 2;
          uint8_t pg = tg >> 2;
          uint8_t pb = tb >> 2;
          
          // Apply shader processing (invert, mask, effect)
          // Pass screen coordinates for gradient shader
          if (applyShaderToPixel(pr, pg, pb, 255, dx + x, dy + y)) {
            setPixelHUB75(dx + x, dy + y, pr, pg, pb);
          }
        }
      }
    } else {
      // Direct blit (no AA)
      for (int y = 0; y < s.height; y++) {
        for (int x = 0; x < s.width; x++) {
          int idx = (y * s.width + x) * 3;
          uint8_t r = s.data[idx];
          uint8_t g = s.data[idx + 1];
          uint8_t b = s.data[idx + 2];
          
          // Apply shader processing (invert, mask, effect)
          // Pass screen coordinates for gradient shader
          if (applyShaderToPixel(r, g, b, 255, dx + x, dy + y)) {
            setPixelHUB75(dx + x, dy + y, r, g, b);
          }
        }
      }
    }
  } else if (s.format == 1 && gpu.target == 1) {
    // Mono sprite to OLED
    for (int y = 0; y < s.height; y++) {
      for (int x = 0; x < s.width; x++) {
        int byte_idx = (y * ((s.width + 7) / 8)) + (x / 8);
        int bit = 7 - (x % 8);
        bool on = (s.data[byte_idx] >> bit) & 1;
        setPixelOLED(dx + x, dy + y, on);
      }
    }
  }
}

// Filled rectangle with AA edges (sub-pixel precision)
static void fillRectF(float x, float y, float w, float h, uint8_t r, uint8_t g, uint8_t b) {
  if (w <= 0 || h <= 0) return;
  
  // Compute bounds with 1 pixel margin for AA edges
  int minX = (int)floorf(x);
  int maxX = (int)ceilf(x + w);
  int minY = (int)floorf(y);
  int maxY = (int)ceilf(y + h);
  
  // Clamp to screen
  if (minX < 0) minX = 0;
  if (minY < 0) minY = 0;
  if (maxX >= TOTAL_WIDTH) maxX = TOTAL_WIDTH - 1;
  if (maxY >= TOTAL_HEIGHT) maxY = TOTAL_HEIGHT - 1;
  
  float x1 = x, y1 = y, x2 = x + w, y2 = y + h;
  
  for (int py = minY; py <= maxY; py++) {
    for (int px = minX; px <= maxX; px++) {
      // Calculate pixel center coverage for AA
      float pxc = px + 0.5f;
      float pyc = py + 0.5f;
      
      // Distance from each edge (positive = inside)
      float dLeft   = pxc - x1;
      float dRight  = x2 - pxc;
      float dTop    = pyc - y1;
      float dBottom = y2 - pyc;
      
      // Minimum distance to any edge (clamped to [-0.5, 0.5])
      float coverage = fminf(fminf(dLeft, dRight), fminf(dTop, dBottom));
      
      if (aa_enabled && gpu.target == 0) {
        if (coverage >= 0.5f) {
          // Fully inside
          setPixelHUB75(px, py, r, g, b);
        } else if (coverage > -0.5f) {
          // Partial coverage for AA edge
          uint8_t alpha = (uint8_t)((coverage + 0.5f) * 255.0f);
          blendPixelHUB75(px, py, r, g, b, alpha);
        }
      } else {
        // No AA: simple threshold
        if (coverage >= 0) {
          setPixel(px, py, r, g, b);
        }
      }
    }
  }
}

// Sprite blit with sub-pixel positioning using BILINEAR SPLATTING
// Each sprite pixel "splats" its color to the 4 screen pixels it overlaps
// This creates smooth sub-pixel movement with proper AA
// O(spritePixels) complexity - same efficient algorithm as blitSpriteRotated
static void blitSpriteF(int id, float dx, float dy) {
  if (id < 0 || id >= MAX_SPRITES || !gpu.sprites[id].valid) return;
  
  Sprite& s = gpu.sprites[id];
  
  if (s.format == 0 && gpu.target == 0) {
    if (aa_enabled) {
      // Efficient bilinear splatting - O(spritePixels) complexity
      // Same algorithm as blitSpriteRotated but without rotation
      
      // Calculate bounding box for splat buffer clear
      int pMinX = (int)floorf(dx);
      int pMaxX = (int)ceilf(dx + s.width) + 1;
      int pMinY = (int)floorf(dy);
      int pMaxY = (int)ceilf(dy + s.height) + 1;
      if (pMinX < 0) pMinX = 0;
      if (pMinY < 0) pMinY = 0;
      if (pMaxX >= TOTAL_WIDTH) pMaxX = TOTAL_WIDTH - 1;
      if (pMaxY >= TOTAL_HEIGHT) pMaxY = TOTAL_HEIGHT - 1;
      
      // Clear the splat buffer for the affected region
      for (int y = pMinY; y <= pMaxY; y++) {
        for (int x = pMinX; x <= pMaxX; x++) {
          int idx = y * TOTAL_WIDTH + x;
          splat_r[idx] = splat_g[idx] = splat_b[idx] = splat_w[idx] = 0;
        }
      }
      
      // For each sprite pixel, splat to 4 overlapping screen pixels
      for (int sy = 0; sy < s.height; sy++) {
        for (int sx = 0; sx < s.width; sx++) {
          // Get sprite pixel color
          int sidx = (sy * s.width + sx) * 3;
          uint8_t pr8 = s.data[sidx + 0];
          uint8_t pg8 = s.data[sidx + 1];
          uint8_t pb8 = s.data[sidx + 2];
          
          // Screen position of this sprite pixel (calculate first for gradient shader)
          float screenX = dx + sx;
          float screenY = dy + sy;
          
          // Apply shader processing (invert, mask, effect)
          // Pass screen coordinates for gradient shader
          if (!applyShaderToPixel(pr8, pg8, pb8, 255, (int16_t)screenX, (int16_t)screenY)) {
            continue;  // Pixel is transparent after shader processing
          }
          
          float pr = pr8;
          float pg = pg8;
          float pb = pb8;
          
          // Integer screen position and fractional offset
          int ix = (int)floorf(screenX);
          int iy = (int)floorf(screenY);
          float fx = screenX - ix;
          float fy = screenY - iy;
          
          // Bilinear splat weights
          float w00 = (1.0f - fx) * (1.0f - fy);
          float w10 = fx * (1.0f - fy);
          float w01 = (1.0f - fx) * fy;
          float w11 = fx * fy;
          
          // Splat to 4 overlapping screen pixels
          splatPixel(ix,     iy,     pr, pg, pb, w00);
          splatPixel(ix + 1, iy,     pr, pg, pb, w10);
          splatPixel(ix,     iy + 1, pr, pg, pb, w01);
          splatPixel(ix + 1, iy + 1, pr, pg, pb, w11);
        }
      }
      
      // Resolve splat buffer to screen
      for (int y = pMinY; y <= pMaxY; y++) {
        for (int x = pMinX; x <= pMaxX; x++) {
          int idx = y * TOTAL_WIDTH + x;
          if (splat_w[idx] > 0.001f) {
            uint8_t r = (uint8_t)fminf(255.0f, splat_r[idx] / splat_w[idx]);
            uint8_t g = (uint8_t)fminf(255.0f, splat_g[idx] / splat_w[idx]);
            uint8_t b = (uint8_t)fminf(255.0f, splat_b[idx] / splat_w[idx]);
            uint8_t alpha = (uint8_t)fminf(255.0f, splat_w[idx] * 255.0f);
            if (alpha > 250) {
              setPixelHUB75(x, y, r, g, b);
            } else if (alpha > 4) {
              blendPixelHUB75(x, y, r, g, b, alpha);
            }
          }
        }
      }
    } else {
      // No AA: Direct integer blit (nearest neighbor)
      int ix = (int)roundf(dx);
      int iy = (int)roundf(dy);
      for (int y = 0; y < s.height; y++) {
        for (int x = 0; x < s.width; x++) {
          int idx = (y * s.width + x) * 3;
          uint8_t r = s.data[idx];
          uint8_t g = s.data[idx + 1];
          uint8_t b = s.data[idx + 2];
          
          // Apply shader processing (invert, mask, effect)
          // Pass screen coordinates for gradient shader
          if (applyShaderToPixel(r, g, b, 255, ix + x, iy + y)) {
            setPixelHUB75(ix + x, iy + y, r, g, b);
          }
        }
      }
    }
  } else {
    // For OLED or non-RGB, fall back to integer blit
    blitSprite(id, (int)roundf(dx), (int)roundf(dy));
  }
}

// Sprite blit with rotation using BILINEAR SPLATTING
// Each sprite pixel is rotated and "splats" to overlapping screen pixels
// This creates smooth rotation AND sub-pixel movement with proper AA
static void blitSpriteRotated(int id, float dx, float dy, float angleDeg) {
  // Clear ENTIRE splat buffer at start to prevent any cross-sprite ghosting
  clearSplatBuffer();
  
  // Set panel isolation based on sprite center position to prevent bilinear bleed
  // Left panel: x=0-63, Right panel: x=64-127
  currentSpritePanel = (dx >= PANEL_WIDTH) ? 1 : 0;
  
  if (id < 0 || id >= MAX_SPRITES || !gpu.sprites[id].valid) {
    static int invalid_count = 0;
    if (++invalid_count <= 5) {
      ESP_LOGW(TAG, "blitSpriteRotated: invalid sprite id=%d valid=%d", id, 
               (id >= 0 && id < MAX_SPRITES) ? gpu.sprites[id].valid : -1);
    }
    currentSpritePanel = -1;  // Reset on invalid
    return;
  }
  
  Sprite& s = gpu.sprites[id];
  
  if (s.format != 0 || gpu.target != 0) {
    // For OLED or mono sprites, fall back to non-rotated blit
    blitSprite(id, (int)roundf(dx), (int)roundf(dy));
    currentSpritePanel = -1;  // Reset after
    return;
  }
  
  // Convert angle to radians
  float angleRad = angleDeg * (3.14159265f / 180.0f);
  float cosA = cosf(angleRad);
  float sinA = sinf(angleRad);
  
  // Sprite center (pivot point for rotation)
  float cx = s.width / 2.0f;
  float cy = s.height / 2.0f;
  
  // Calculate bounding box of rotated sprite
  float corners[4][2] = {
    {-cx, -cy},
    {s.width - cx, -cy},
    {s.width - cx, s.height - cy},
    {-cx, s.height - cy}
  };
  
  float minX = 9999, maxX = -9999, minY = 9999, maxY = -9999;
  for (int i = 0; i < 4; i++) {
    float rx = corners[i][0] * cosA - corners[i][1] * sinA + dx;
    float ry = corners[i][0] * sinA + corners[i][1] * cosA + dy;
    if (rx < minX) minX = rx;
    if (rx > maxX) maxX = rx;
    if (ry < minY) minY = ry;
    if (ry > maxY) maxY = ry;
  }
  
  // Screen bounds with margin
  int pMinX = (int)floorf(minX) - 1;
  int pMaxX = (int)ceilf(maxX) + 1;
  int pMinY = (int)floorf(minY) - 1;
  int pMaxY = (int)ceilf(maxY) + 1;
  if (pMinX < 0) pMinX = 0;
  if (pMinY < 0) pMinY = 0;
  if (pMaxX >= TOTAL_WIDTH) pMaxX = TOTAL_WIDTH - 1;
  if (pMaxY >= TOTAL_HEIGHT) pMaxY = TOTAL_HEIGHT - 1;
  
  // CRITICAL: Clamp bounding box to panel boundary to prevent cross-panel artifacts
  if (currentSpritePanel == 0) {
    // Left panel sprite - clamp max to panel boundary
    if (pMaxX >= PANEL_WIDTH) pMaxX = PANEL_WIDTH - 1;
  } else if (currentSpritePanel == 1) {
    // Right panel sprite - clamp min to panel boundary
    if (pMinX < PANEL_WIDTH) pMinX = PANEL_WIDTH;
  }
  
  if (aa_enabled) {
    // BILINEAR SPLATTING with rotation
    // Clear the splat buffer for the affected region
    for (int y = pMinY; y <= pMaxY; y++) {
      for (int x = pMinX; x <= pMaxX; x++) {
        int idx = y * TOTAL_WIDTH + x;
        splat_r[idx] = splat_g[idx] = splat_b[idx] = splat_w[idx] = 0;
      }
    }
    
    // For each sprite pixel, rotate and splat to screen
    for (int sy = 0; sy < s.height; sy++) {
      for (int sx = 0; sx < s.width; sx++) {
        // Get sprite pixel color
        int sidx = (sy * s.width + sx) * 3;
        uint8_t pr8 = s.data[sidx + 0];
        uint8_t pg8 = s.data[sidx + 1];
        uint8_t pb8 = s.data[sidx + 2];
        
        // Position relative to sprite center
        float relX = sx - cx + 0.5f;  // +0.5 for pixel center
        float relY = sy - cy + 0.5f;
        
        // Rotate around center and translate to screen position
        float screenX = relX * cosA - relY * sinA + dx;
        float screenY = relX * sinA + relY * cosA + dy;
        
        // Apply shader processing (invert, mask, effect)
        // Pass screen coordinates for gradient shader
        if (!applyShaderToPixel(pr8, pg8, pb8, 255, (int16_t)screenX, (int16_t)screenY)) {
          continue;  // Pixel is transparent after shader processing
        }
        
        float pr = pr8;
        float pg = pg8;
        float pb = pb8;
        
        // Integer screen position and fractional offset
        int ix = (int)floorf(screenX);
        int iy = (int)floorf(screenY);
        float fx = screenX - ix;
        float fy = screenY - iy;
        
        // Bilinear splat weights
        float w00 = (1.0f - fx) * (1.0f - fy);
        float w10 = fx * (1.0f - fy);
        float w01 = (1.0f - fx) * fy;
        float w11 = fx * fy;
        
        // Splat to 4 overlapping screen pixels
        splatPixel(ix,     iy,     pr, pg, pb, w00);
        splatPixel(ix + 1, iy,     pr, pg, pb, w10);
        splatPixel(ix,     iy + 1, pr, pg, pb, w01);
        splatPixel(ix + 1, iy + 1, pr, pg, pb, w11);
      }
    }
    
    // Flush accumulated colors to screen
    flushSplatBuffer(pMinX, pMinY, pMaxX, pMaxY);
    
  } else {
    // No AA: Inverse mapping with nearest neighbor
    for (int py = pMinY; py <= pMaxY; py++) {
      for (int px = pMinX; px <= pMaxX; px++) {
        // Apply panel isolation for non-AA mode too
        if (currentSpritePanel == 0 && px >= PANEL_WIDTH) continue;
        if (currentSpritePanel == 1 && px < PANEL_WIDTH) continue;
        
        float screenX = (float)px - dx;
        float screenY = (float)py - dy;
        
        // Inverse rotation
        float spriteX = screenX * cosA + screenY * sinA + cx;
        float spriteY = -screenX * sinA + screenY * cosA + cy;
        
        if (spriteX >= 0 && spriteX < s.width && spriteY >= 0 && spriteY < s.height) {
          int sx = (int)spriteX;
          int sy = (int)spriteY;
          int idx = (sy * s.width + sx) * 3;
          uint8_t r = s.data[idx];
          uint8_t g = s.data[idx + 1];
          uint8_t b = s.data[idx + 2];
          
          // Apply shader processing (invert, mask, effect)
          // Pass screen coordinates for gradient shader
          if (applyShaderToPixel(r, g, b, 255, px, py)) {
            setPixelHUB75(px, py, r, g, b);
          }
        }
      }
    }
  }
  
  // Reset panel isolation after sprite draw
  currentSpritePanel = -1;
}

// ============================================================
// Blits a sprite with rotation AND scaling
// scale: 1.0 = 100%, 0.5 = 50%, 2.0 = 200%
// ============================================================
static void blitSpriteRotatedScaled(int id, float dx, float dy, float angleDeg, float scale) {
  // Clear ENTIRE splat buffer at start to prevent any cross-sprite ghosting
  clearSplatBuffer();
  
  // Set panel isolation based on sprite center position to prevent bilinear bleed
  currentSpritePanel = (dx >= PANEL_WIDTH) ? 1 : 0;
  
  if (id < 0 || id >= MAX_SPRITES || !gpu.sprites[id].valid) {
    static int invalid_count = 0;
    if (++invalid_count <= 5) {
      ESP_LOGW(TAG, "blitSpriteRotatedScaled: invalid sprite id=%d valid=%d", id, 
               (id >= 0 && id < MAX_SPRITES) ? gpu.sprites[id].valid : -1);
    }
    currentSpritePanel = -1;
    return;
  }
  
  Sprite& s = gpu.sprites[id];
  
  if (s.format != 0 || gpu.target != 0) {
    blitSprite(id, (int)roundf(dx), (int)roundf(dy));
    currentSpritePanel = -1;
    return;
  }
  
  // Clamp scale to reasonable range
  if (scale < 0.1f) scale = 0.1f;
  if (scale > 4.0f) scale = 4.0f;
  
  // Convert angle to radians
  float angleRad = angleDeg * (3.14159265f / 180.0f);
  float cosA = cosf(angleRad);
  float sinA = sinf(angleRad);
  
  // Sprite center (pivot point for rotation)
  float cx = s.width / 2.0f;
  float cy = s.height / 2.0f;
  
  // Scaled dimensions for bounding box calculation
  float scaledWidth = s.width * scale;
  float scaledHeight = s.height * scale;
  float scaledCx = scaledWidth / 2.0f;
  float scaledCy = scaledHeight / 2.0f;
  
  // Calculate bounding box of rotated AND scaled sprite
  float corners[4][2] = {
    {-scaledCx, -scaledCy},
    {scaledWidth - scaledCx, -scaledCy},
    {scaledWidth - scaledCx, scaledHeight - scaledCy},
    {-scaledCx, scaledHeight - scaledCy}
  };
  
  float minX = 9999, maxX = -9999, minY = 9999, maxY = -9999;
  for (int i = 0; i < 4; i++) {
    float rx = corners[i][0] * cosA - corners[i][1] * sinA + dx;
    float ry = corners[i][0] * sinA + corners[i][1] * cosA + dy;
    if (rx < minX) minX = rx;
    if (rx > maxX) maxX = rx;
    if (ry < minY) minY = ry;
    if (ry > maxY) maxY = ry;
  }
  
  // Screen bounds with margin
  int pMinX = (int)floorf(minX) - 1;
  int pMaxX = (int)ceilf(maxX) + 1;
  int pMinY = (int)floorf(minY) - 1;
  int pMaxY = (int)ceilf(maxY) + 1;
  if (pMinX < 0) pMinX = 0;
  if (pMinY < 0) pMinY = 0;
  if (pMaxX >= TOTAL_WIDTH) pMaxX = TOTAL_WIDTH - 1;
  if (pMaxY >= TOTAL_HEIGHT) pMaxY = TOTAL_HEIGHT - 1;
  
  // Clamp bounding box to panel boundary
  if (currentSpritePanel == 0) {
    if (pMaxX >= PANEL_WIDTH) pMaxX = PANEL_WIDTH - 1;
  } else if (currentSpritePanel == 1) {
    if (pMinX < PANEL_WIDTH) pMinX = PANEL_WIDTH;
  }
  
  if (aa_enabled) {
    // BILINEAR SPLATTING with rotation and scaling
    for (int y = pMinY; y <= pMaxY; y++) {
      for (int x = pMinX; x <= pMaxX; x++) {
        int idx = y * TOTAL_WIDTH + x;
        splat_r[idx] = splat_g[idx] = splat_b[idx] = splat_w[idx] = 0;
      }
    }
    
    // Inverse scale factor for sampling
    float invScale = 1.0f / scale;
    
    // For each sprite pixel, rotate, scale, and splat to screen
    for (int sy = 0; sy < s.height; sy++) {
      for (int sx = 0; sx < s.width; sx++) {
        int sidx = (sy * s.width + sx) * 3;
        uint8_t pr8 = s.data[sidx + 0];
        uint8_t pg8 = s.data[sidx + 1];
        uint8_t pb8 = s.data[sidx + 2];
        
        // Position relative to sprite center
        float relX = (sx - cx + 0.5f) * scale;  // Apply scale
        float relY = (sy - cy + 0.5f) * scale;
        
        // Rotate around center and translate to screen position
        float screenX = relX * cosA - relY * sinA + dx;
        float screenY = relX * sinA + relY * cosA + dy;
        
        // Apply shader processing (invert, mask, effect)
        // Pass screen coordinates for gradient shader
        if (!applyShaderToPixel(pr8, pg8, pb8, 255, (int16_t)screenX, (int16_t)screenY)) {
          continue;  // Pixel is transparent after shader processing
        }
        
        float pr = pr8;
        float pg = pg8;
        float pb = pb8;
        
        // Integer screen position and fractional offset
        int ix = (int)floorf(screenX);
        int iy = (int)floorf(screenY);
        float fx = screenX - ix;
        float fy = screenY - iy;
        
        // Bilinear splat weights (scaled for coverage)
        float coverage = scale * scale;
        float w00 = (1.0f - fx) * (1.0f - fy) * coverage;
        float w10 = fx * (1.0f - fy) * coverage;
        float w01 = (1.0f - fx) * fy * coverage;
        float w11 = fx * fy * coverage;
        
        splatPixel(ix,     iy,     pr, pg, pb, w00);
        splatPixel(ix + 1, iy,     pr, pg, pb, w10);
        splatPixel(ix,     iy + 1, pr, pg, pb, w01);
        splatPixel(ix + 1, iy + 1, pr, pg, pb, w11);
      }
    }
    
    flushSplatBuffer(pMinX, pMinY, pMaxX, pMaxY);
    
  } else {
    // No AA: Inverse mapping with nearest neighbor
    float invScale = 1.0f / scale;
    
    for (int py = pMinY; py <= pMaxY; py++) {
      for (int px = pMinX; px <= pMaxX; px++) {
        if (currentSpritePanel == 0 && px >= PANEL_WIDTH) continue;
        if (currentSpritePanel == 1 && px < PANEL_WIDTH) continue;
        
        float screenX = (float)px - dx;
        float screenY = (float)py - dy;
        
        // Inverse rotation, then inverse scale
        float rotatedX = screenX * cosA + screenY * sinA;
        float rotatedY = -screenX * sinA + screenY * cosA;
        
        float spriteX = rotatedX * invScale + cx;
        float spriteY = rotatedY * invScale + cy;
        
        if (spriteX >= 0 && spriteX < s.width && spriteY >= 0 && spriteY < s.height) {
          int sx = (int)spriteX;
          int sy = (int)spriteY;
          int idx = (sy * s.width + sx) * 3;
          uint8_t r = s.data[idx];
          uint8_t g = s.data[idx + 1];
          uint8_t b = s.data[idx + 2];
          
          // Apply shader processing (invert, mask, effect)
          // Pass screen coordinates for gradient shader
          if (applyShaderToPixel(r, g, b, 255, px, py)) {
            setPixelHUB75(px, py, r, g, b);
          }
        }
      }
    }
  }
  
  currentSpritePanel = -1;
}

// ============================================================
// Blits a sprite with rotation, scaling, AND horizontal/vertical flip
// flipX: mirror horizontally (around vertical axis)
// flipY: mirror vertically (around horizontal axis)
// ============================================================
static void blitSpriteRotatedScaledFlip(int id, float dx, float dy, float angleDeg, float scale, bool flipX, bool flipY) {
  // Clear ENTIRE splat buffer at start to prevent any cross-sprite ghosting
  clearSplatBuffer();
  
  // Set panel isolation based on sprite center position to prevent bilinear bleed
  currentSpritePanel = (dx >= PANEL_WIDTH) ? 1 : 0;
  
  if (id < 0 || id >= MAX_SPRITES || !gpu.sprites[id].valid) {
    static int invalid_count = 0;
    if (++invalid_count <= 5) {
      ESP_LOGW(TAG, "blitSpriteRotatedScaledFlip: invalid sprite id=%d valid=%d", id, 
               (id >= 0 && id < MAX_SPRITES) ? gpu.sprites[id].valid : -1);
    }
    currentSpritePanel = -1;
    return;
  }
  
  Sprite& s = gpu.sprites[id];
  
  if (s.format != 0 || gpu.target != 0) {
    blitSprite(id, (int)roundf(dx), (int)roundf(dy));
    currentSpritePanel = -1;
    return;
  }
  
  // Clamp scale to reasonable range
  if (scale < 0.1f) scale = 0.1f;
  if (scale > 4.0f) scale = 4.0f;
  
  // Convert angle to radians
  float angleRad = angleDeg * (3.14159265f / 180.0f);
  float cosA = cosf(angleRad);
  float sinA = sinf(angleRad);
  
  // Sprite center (pivot point for rotation)
  float cx = s.width / 2.0f;
  float cy = s.height / 2.0f;
  
  // Scaled dimensions for bounding box calculation
  float scaledWidth = s.width * scale;
  float scaledHeight = s.height * scale;
  float scaledCx = scaledWidth / 2.0f;
  float scaledCy = scaledHeight / 2.0f;
  
  // Calculate bounding box of rotated AND scaled sprite
  float corners[4][2] = {
    {-scaledCx, -scaledCy},
    {scaledWidth - scaledCx, -scaledCy},
    {scaledWidth - scaledCx, scaledHeight - scaledCy},
    {-scaledCx, scaledHeight - scaledCy}
  };
  
  float minX = 9999, maxX = -9999, minY = 9999, maxY = -9999;
  for (int i = 0; i < 4; i++) {
    float rx = corners[i][0] * cosA - corners[i][1] * sinA + dx;
    float ry = corners[i][0] * sinA + corners[i][1] * cosA + dy;
    if (rx < minX) minX = rx;
    if (rx > maxX) maxX = rx;
    if (ry < minY) minY = ry;
    if (ry > maxY) maxY = ry;
  }
  
  // Screen bounds with margin
  int pMinX = (int)floorf(minX) - 1;
  int pMaxX = (int)ceilf(maxX) + 1;
  int pMinY = (int)floorf(minY) - 1;
  int pMaxY = (int)ceilf(maxY) + 1;
  if (pMinX < 0) pMinX = 0;
  if (pMinY < 0) pMinY = 0;
  if (pMaxX >= TOTAL_WIDTH) pMaxX = TOTAL_WIDTH - 1;
  if (pMaxY >= TOTAL_HEIGHT) pMaxY = TOTAL_HEIGHT - 1;
  
  // Clamp bounding box to panel boundary
  if (currentSpritePanel == 0) {
    if (pMaxX >= PANEL_WIDTH) pMaxX = PANEL_WIDTH - 1;
  } else if (currentSpritePanel == 1) {
    if (pMinX < PANEL_WIDTH) pMinX = PANEL_WIDTH;
  }
  
  if (aa_enabled) {
    // BILINEAR SPLATTING with rotation, scaling, and flip
    for (int y = pMinY; y <= pMaxY; y++) {
      for (int x = pMinX; x <= pMaxX; x++) {
        int idx = y * TOTAL_WIDTH + x;
        splat_r[idx] = splat_g[idx] = splat_b[idx] = splat_w[idx] = 0;
      }
    }
    
    // Inverse scale factor for sampling
    float invScale = 1.0f / scale;
    
    // For each sprite pixel, rotate, scale, and splat to screen
    for (int sy = 0; sy < s.height; sy++) {
      for (int sx = 0; sx < s.width; sx++) {
        // Apply flip when reading from source
        int srcX = flipX ? (s.width - 1 - sx) : sx;
        int srcY = flipY ? (s.height - 1 - sy) : sy;
        
        int sidx = (srcY * s.width + srcX) * 3;
        uint8_t pr8 = s.data[sidx + 0];
        uint8_t pg8 = s.data[sidx + 1];
        uint8_t pb8 = s.data[sidx + 2];
        
        // Position relative to sprite center (use original sx/sy for positioning)
        float relX = (sx - cx + 0.5f) * scale;
        float relY = (sy - cy + 0.5f) * scale;
        
        // Rotate around center and translate to screen position
        float screenX = relX * cosA - relY * sinA + dx;
        float screenY = relX * sinA + relY * cosA + dy;
        
        // Apply shader processing (invert, mask, effect)
        // Pass screen coordinates for gradient shader
        if (!applyShaderToPixel(pr8, pg8, pb8, 255, (int16_t)screenX, (int16_t)screenY)) {
          continue;  // Pixel is transparent after shader processing
        }
        
        float pr = pr8;
        float pg = pg8;
        float pb = pb8;
        
        // Integer screen position and fractional offset
        int ix = (int)floorf(screenX);
        int iy = (int)floorf(screenY);
        float fx = screenX - ix;
        float fy = screenY - iy;
        
        // Bilinear splat weights (scaled for coverage)
        float coverage = scale * scale;
        float w00 = (1.0f - fx) * (1.0f - fy) * coverage;
        float w10 = fx * (1.0f - fy) * coverage;
        float w01 = (1.0f - fx) * fy * coverage;
        float w11 = fx * fy * coverage;
        
        splatPixel(ix,     iy,     pr, pg, pb, w00);
        splatPixel(ix + 1, iy,     pr, pg, pb, w10);
        splatPixel(ix,     iy + 1, pr, pg, pb, w01);
        splatPixel(ix + 1, iy + 1, pr, pg, pb, w11);
      }
    }
    
    flushSplatBuffer(pMinX, pMinY, pMaxX, pMaxY);
    
  } else {
    // No AA: Inverse mapping with nearest neighbor
    float invScale = 1.0f / scale;
    
    for (int py = pMinY; py <= pMaxY; py++) {
      for (int px = pMinX; px <= pMaxX; px++) {
        if (currentSpritePanel == 0 && px >= PANEL_WIDTH) continue;
        if (currentSpritePanel == 1 && px < PANEL_WIDTH) continue;
        
        float screenX = (float)px - dx;
        float screenY = (float)py - dy;
        
        // Inverse rotation, then inverse scale
        float rotatedX = screenX * cosA + screenY * sinA;
        float rotatedY = -screenX * sinA + screenY * cosA;
        
        float spriteX = rotatedX * invScale + cx;
        float spriteY = rotatedY * invScale + cy;
        
        if (spriteX >= 0 && spriteX < s.width && spriteY >= 0 && spriteY < s.height) {
          int sx = (int)spriteX;
          int sy = (int)spriteY;
          
          // Apply flip when reading from source
          int srcX = flipX ? (s.width - 1 - sx) : sx;
          int srcY = flipY ? (s.height - 1 - sy) : sy;
          
          int idx = (srcY * s.width + srcX) * 3;
          uint8_t pr = s.data[idx];
          uint8_t pg = s.data[idx + 1];
          uint8_t pb = s.data[idx + 2];
          
          // Apply shader processing (invert, mask, effect)
          // Pass screen coordinates for gradient shader
          if (applyShaderToPixel(pr, pg, pb, 255, px, py)) {
            setPixelHUB75(px, py, pr, pg, pb);
          }
        }
      }
    }
  }
  
  currentSpritePanel = -1;
}

// ============================================================
// Simple PRNG
// ============================================================
static uint16_t gpuRand() {
  gpu.randSeed = gpu.randSeed * 1103515245 + 12345;
  return (gpu.randSeed >> 16) & 0xFFFF;
}

// ============================================================
// Shader Bytecode Interpreter
// ============================================================
static void executeShader(int slot) {
  if (slot < 0 || slot >= MAX_SHADERS || !gpu.shaders[slot].valid) return;
  
  Shader& shader = gpu.shaders[slot];
  uint8_t* code = shader.bytecode;
  uint16_t pc = 0;
  int maxInstructions = 100000;  // Prevent infinite loops
  
  // Reset registers and loop stack
  memset(gpu.regs, 0, sizeof(gpu.regs));
  gpu.loopSP = 0;
  
  while (pc < shader.length && maxInstructions-- > 0) {
    Op op = (Op)code[pc++];
    
    switch (op) {
      case Op::NOP:
        break;
        
      case Op::HALT:
        return;
        
      case Op::SET: {
        uint8_t rd = code[pc++];
        int16_t imm = (int16_t)(code[pc] | (code[pc + 1] << 8));
        pc += 2;
        if (rd < MAX_REGISTERS) gpu.regs[rd] = imm;
        break;
      }
      
      case Op::MOV: {
        uint8_t rd = code[pc++];
        uint8_t rs = code[pc++];
        if (rd < MAX_REGISTERS && rs < MAX_REGISTERS) gpu.regs[rd] = gpu.regs[rs];
        break;
      }
      
      case Op::LOAD: {
        uint8_t rd = code[pc++];
        uint8_t var = code[pc++];
        if (rd < MAX_REGISTERS && var < MAX_VARIABLES) gpu.regs[rd] = gpu.variables[var];
        break;
      }
      
      case Op::STORE: {
        uint8_t var = code[pc++];
        uint8_t rs = code[pc++];
        if (var < MAX_VARIABLES && rs < MAX_REGISTERS) gpu.variables[var] = gpu.regs[rs];
        break;
      }
      
      case Op::ADD: {
        uint8_t rd = code[pc++], ra = code[pc++], rb = code[pc++];
        if (rd < MAX_REGISTERS) gpu.regs[rd] = gpu.regs[ra] + gpu.regs[rb];
        break;
      }
      
      case Op::SUB: {
        uint8_t rd = code[pc++], ra = code[pc++], rb = code[pc++];
        if (rd < MAX_REGISTERS) gpu.regs[rd] = gpu.regs[ra] - gpu.regs[rb];
        break;
      }
      
      case Op::MUL: {
        uint8_t rd = code[pc++], ra = code[pc++], rb = code[pc++];
        if (rd < MAX_REGISTERS) gpu.regs[rd] = (gpu.regs[ra] * gpu.regs[rb]) >> 8;
        break;
      }
      
      case Op::DIV: {
        uint8_t rd = code[pc++], ra = code[pc++], rb = code[pc++];
        if (rd < MAX_REGISTERS && gpu.regs[rb] != 0) gpu.regs[rd] = gpu.regs[ra] / gpu.regs[rb];
        break;
      }
      
      case Op::MOD: {
        uint8_t rd = code[pc++], ra = code[pc++], rb = code[pc++];
        if (rd < MAX_REGISTERS && gpu.regs[rb] != 0) gpu.regs[rd] = gpu.regs[ra] % gpu.regs[rb];
        break;
      }
      
      case Op::NEG: {
        uint8_t rd = code[pc++], rs = code[pc++];
        if (rd < MAX_REGISTERS) gpu.regs[rd] = -gpu.regs[rs];
        break;
      }
      
      case Op::ABS: {
        uint8_t rd = code[pc++], rs = code[pc++];
        if (rd < MAX_REGISTERS) gpu.regs[rd] = gpu.regs[rs] < 0 ? -gpu.regs[rs] : gpu.regs[rs];
        break;
      }
      
      case Op::MIN: {
        uint8_t rd = code[pc++], ra = code[pc++], rb = code[pc++];
        if (rd < MAX_REGISTERS) gpu.regs[rd] = gpu.regs[ra] < gpu.regs[rb] ? gpu.regs[ra] : gpu.regs[rb];
        break;
      }
      
      case Op::MAX: {
        uint8_t rd = code[pc++], ra = code[pc++], rb = code[pc++];
        if (rd < MAX_REGISTERS) gpu.regs[rd] = gpu.regs[ra] > gpu.regs[rb] ? gpu.regs[ra] : gpu.regs[rb];
        break;
      }
      
      case Op::AND: {
        uint8_t rd = code[pc++], ra = code[pc++], rb = code[pc++];
        if (rd < MAX_REGISTERS) gpu.regs[rd] = gpu.regs[ra] & gpu.regs[rb];
        break;
      }
      
      case Op::OR: {
        uint8_t rd = code[pc++], ra = code[pc++], rb = code[pc++];
        if (rd < MAX_REGISTERS) gpu.regs[rd] = gpu.regs[ra] | gpu.regs[rb];
        break;
      }
      
      case Op::XOR: {
        uint8_t rd = code[pc++], ra = code[pc++], rb = code[pc++];
        if (rd < MAX_REGISTERS) gpu.regs[rd] = gpu.regs[ra] ^ gpu.regs[rb];
        break;
      }
      
      case Op::NOT: {
        uint8_t rd = code[pc++], rs = code[pc++];
        if (rd < MAX_REGISTERS) gpu.regs[rd] = ~gpu.regs[rs];
        break;
      }
      
      case Op::SHL: {
        uint8_t rd = code[pc++], rs = code[pc++], imm = code[pc++];
        if (rd < MAX_REGISTERS) gpu.regs[rd] = gpu.regs[rs] << imm;
        break;
      }
      
      case Op::SHR: {
        uint8_t rd = code[pc++], rs = code[pc++], imm = code[pc++];
        if (rd < MAX_REGISTERS) gpu.regs[rd] = gpu.regs[rs] >> imm;
        break;
      }
      
      case Op::SIN: {
        uint8_t rd = code[pc++], rs = code[pc++];
        if (rd < MAX_REGISTERS) gpu.regs[rd] = SIN_LUT[gpu.regs[rs] & 255];
        break;
      }
      
      case Op::COS: {
        uint8_t rd = code[pc++], rs = code[pc++];
        if (rd < MAX_REGISTERS) gpu.regs[rd] = COS_LUT[gpu.regs[rs] & 255];
        break;
      }
      
      case Op::SQRT: {
        uint8_t rd = code[pc++], rs = code[pc++];
        if (rd < MAX_REGISTERS) gpu.regs[rd] = SQRT_LUT[gpu.regs[rs] & 255];
        break;
      }
      
      case Op::SETPX: {
        uint8_t xr = code[pc++], yr = code[pc++];
        uint8_t rr = code[pc++], gr = code[pc++], br = code[pc++];
        setPixel(gpu.regs[xr], gpu.regs[yr], gpu.regs[rr], gpu.regs[gr], gpu.regs[br]);
        break;
      }
      
      case Op::GETPX: {
        uint8_t rd = code[pc++], xr = code[pc++], yr = code[pc++];
        if (rd < MAX_REGISTERS) gpu.regs[rd] = getPixel(gpu.regs[xr], gpu.regs[yr]) & 0xFFFF;
        break;
      }
      
      case Op::FILL: {
        uint8_t xr = code[pc++], yr = code[pc++], wr = code[pc++], hr = code[pc++];
        uint8_t rr = code[pc++], gr = code[pc++], br = code[pc++];
        fillRect(gpu.regs[xr], gpu.regs[yr], gpu.regs[wr], gpu.regs[hr],
                 gpu.regs[rr], gpu.regs[gr], gpu.regs[br]);
        break;
      }
      
      case Op::LINE: {
        uint8_t x1r = code[pc++], y1r = code[pc++], x2r = code[pc++], y2r = code[pc++];
        uint8_t rr = code[pc++], gr = code[pc++], br = code[pc++];
        drawLine(gpu.regs[x1r], gpu.regs[y1r], gpu.regs[x2r], gpu.regs[y2r],
                 gpu.regs[rr], gpu.regs[gr], gpu.regs[br]);
        break;
      }
      
      case Op::RECT: {
        uint8_t xr = code[pc++], yr = code[pc++], wr = code[pc++], hr = code[pc++];
        uint8_t rr = code[pc++], gr = code[pc++], br = code[pc++];
        drawRect(gpu.regs[xr], gpu.regs[yr], gpu.regs[wr], gpu.regs[hr],
                 gpu.regs[rr], gpu.regs[gr], gpu.regs[br]);
        break;
      }
      
      case Op::CIRCLE: {
        uint8_t cxr = code[pc++], cyr = code[pc++], radr = code[pc++];
        uint8_t rr = code[pc++], gr = code[pc++], br = code[pc++];
        drawCircle(gpu.regs[cxr], gpu.regs[cyr], gpu.regs[radr],
                   gpu.regs[rr], gpu.regs[gr], gpu.regs[br]);
        break;
      }
      
      case Op::POLY: {
        uint8_t nr = code[pc++], var_start = code[pc++];
        uint8_t rr = code[pc++], gr = code[pc++], br = code[pc++];
        int n = gpu.regs[nr];
        if (n > 0 && n <= 16) {
          int16_t vx[16], vy[16];
          for (int i = 0; i < n; i++) {
            vx[i] = gpu.variables[var_start + i * 2];
            vy[i] = gpu.variables[var_start + i * 2 + 1];
          }
          fillPolygon(n, vx, vy, gpu.regs[rr], gpu.regs[gr], gpu.regs[br]);
        }
        break;
      }
      
      case Op::SPRITE: {
        uint8_t idr = code[pc++], xr = code[pc++], yr = code[pc++];
        blitSprite(gpu.regs[idr], gpu.regs[xr], gpu.regs[yr]);
        break;
      }
      
      case Op::CLEAR: {
        uint8_t rr = code[pc++], gr = code[pc++], br = code[pc++];
        if (gpu.target == 0) {
          uint8_t r = gpu.regs[rr], g = gpu.regs[gr], b = gpu.regs[br];
          for (int i = 0; i < TOTAL_WIDTH * TOTAL_HEIGHT; i++) {
            hub75_buffer[i * 3 + 0] = r;
            hub75_buffer[i * 3 + 1] = g;
            hub75_buffer[i * 3 + 2] = b;
          }
        } else {
          uint8_t val = (gpu.regs[rr] + gpu.regs[gr] + gpu.regs[br]) > 384 ? 0xFF : 0x00;
          memset(oled_buffer, val, OLED_BUFFER_SIZE);
        }
        break;
      }
      
      case Op::LOOP: {
        uint8_t count_reg = code[pc++];
        if (gpu.loopSP < MAX_STACK) {
          gpu.loopStack[gpu.loopSP].pc = pc;
          gpu.loopStack[gpu.loopSP].counter = gpu.regs[count_reg];
          gpu.loopSP++;
        }
        break;
      }
      
      case Op::ENDL: {
        if (gpu.loopSP > 0) {
          gpu.loopStack[gpu.loopSP - 1].counter--;
          if (gpu.loopStack[gpu.loopSP - 1].counter > 0) {
            pc = gpu.loopStack[gpu.loopSP - 1].pc;
          } else {
            gpu.loopSP--;
          }
        }
        break;
      }
      
      case Op::JMP: {
        int16_t offset = (int16_t)(code[pc] | (code[pc + 1] << 8));
        pc += 2;
        pc += offset;
        break;
      }
      
      case Op::JZ: {
        uint8_t rs = code[pc++];
        int16_t offset = (int16_t)(code[pc] | (code[pc + 1] << 8));
        pc += 2;
        if (gpu.regs[rs] == 0) pc += offset;
        break;
      }
      
      case Op::JNZ: {
        uint8_t rs = code[pc++];
        int16_t offset = (int16_t)(code[pc] | (code[pc + 1] << 8));
        pc += 2;
        if (gpu.regs[rs] != 0) pc += offset;
        break;
      }
      
      case Op::JGT: {
        uint8_t rs = code[pc++];
        int16_t offset = (int16_t)(code[pc] | (code[pc + 1] << 8));
        pc += 2;
        if (gpu.regs[rs] > 0) pc += offset;
        break;
      }
      
      case Op::JLT: {
        uint8_t rs = code[pc++];
        int16_t offset = (int16_t)(code[pc] | (code[pc + 1] << 8));
        pc += 2;
        if (gpu.regs[rs] < 0) pc += offset;
        break;
      }
      
      case Op::GETX: {
        uint8_t rd = code[pc++];
        if (rd < MAX_REGISTERS) gpu.regs[rd] = gpu.px;
        break;
      }
      
      case Op::GETY: {
        uint8_t rd = code[pc++];
        if (rd < MAX_REGISTERS) gpu.regs[rd] = gpu.py;
        break;
      }
      
      case Op::GETW: {
        uint8_t rd = code[pc++];
        if (rd < MAX_REGISTERS) gpu.regs[rd] = (gpu.target == 0) ? TOTAL_WIDTH : OLED_WIDTH;
        break;
      }
      
      case Op::GETH: {
        uint8_t rd = code[pc++];
        if (rd < MAX_REGISTERS) gpu.regs[rd] = (gpu.target == 0) ? TOTAL_HEIGHT : OLED_HEIGHT;
        break;
      }
      
      case Op::TIME: {
        uint8_t rd = code[pc++];
        if (rd < MAX_REGISTERS) {
          uint32_t ms = (esp_timer_get_time() - gpu.startTime) / 1000;
          gpu.regs[rd] = ms & 0xFFFF;
        }
        break;
      }
      
      case Op::RAND: {
        uint8_t rd = code[pc++];
        if (rd < MAX_REGISTERS) gpu.regs[rd] = gpuRand();
        break;
      }
      
      default:
        // Unknown opcode - skip
        break;
    }
  }
}

// ============================================================
// Command Protocol from CPU
// ============================================================
#pragma pack(push, 1)
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
