Cyberspecies/Synth-Head/Software/Testing_N_Experimentation/Alpha_Release_Stack/src/CPU_FrameworkAPI_SandSim.cpp

/*****************************************************************
 * CPU_FrameworkAPI_SandSim.cpp - 2D Falling Sand Simulation
 * 
 * A cellular automaton sand simulation that demonstrates:
 * - GPU communication with optimized batch rendering
 * - Real-time particle physics simulation
 * - Multiple particle types (sand, water, stone, fire)
 * - Clean, composable GPU API wrapper
 * - IMU-based gravity control (tilt to change gravity direction!)
 * - Environmental sensor integration (BME280 temperature/humidity/pressure)
 * - GPS location tracking
 * - Microphone audio input for sound-reactive particles!
 * 
 * Controls:
 *   A = Cycle particle type
 *   B = Spawn particles
 *   C = Clear screen
 *   D = Toggle IMU gravity control
 *   TILT = Change gravity direction (when IMU enabled)
 * 
 * Hardware:
 *   - CPU: ESP32-S3 (ESP-IDF)
 *   - GPU: ESP32-S3 with HUB75 (128x32) + OLED (128x128)
 *   - UART: TX=GPIO12, RX=GPIO11 @ 10 Mbps
 *   - IMU: ICM20948 on I2C (SDA=9, SCL=10)
 *   - Environmental: BME280 on I2C (addr=0x76)
 *   - GPS: NEO-8M on UART2 (TX=43, RX=44)
 *   - Microphone: INMP441 on I2S
 *****************************************************************/

#include <cstdio>
#include <cstdint>
#include <cstring>
#include <cmath>
#include <cstdlib>
#include "freertos/FreeRTOS.h"
#include "freertos/task.h"
#include "driver/uart.h"
#include "driver/gpio.h"
#include "driver/i2c.h"
#include "driver/i2s_std.h"
#include "esp_log.h"
#include "esp_timer.h"

static const char* TAG = "SAND_SIM";

// ============================================================
// Configuration
// ============================================================

// UART
#define GPU_UART_NUM    UART_NUM_1
#define GPU_UART_TX     GPIO_NUM_12
#define GPU_UART_RX     GPIO_NUM_11
#define GPU_BAUD        10000000

// Display dimensions
#define HUB75_W         128
#define HUB75_H         32
#define OLED_W          128
#define OLED_H          128

// Buttons (directly poll GPIO - faster than ADC)
#define BTN_A_PIN       GPIO_NUM_5
#define BTN_B_PIN       GPIO_NUM_6
#define BTN_C_PIN       GPIO_NUM_7
#define BTN_D_PIN       GPIO_NUM_15

// I2C for IMU
#define I2C_SDA_PIN     GPIO_NUM_9
#define I2C_SCL_PIN     GPIO_NUM_10
#define IMU_I2C_ADDR    0x68
#define BME280_I2C_ADDR 0x76

// GPS UART (UART2)
#define GPS_UART_NUM    UART_NUM_2
#define GPS_UART_TX     GPIO_NUM_43
#define GPS_UART_RX     GPIO_NUM_44
#define GPS_BAUD        9600

// I2S Microphone (INMP441)
#define MIC_I2S_NUM     I2S_NUM_0
#define MIC_WS_PIN      GPIO_NUM_42
#define MIC_BCK_PIN     GPIO_NUM_40
#define MIC_SD_PIN      GPIO_NUM_2
#define MIC_LR_SEL_PIN  GPIO_NUM_41

// Simulation grid (1:1 with HUB75 pixels)
#define GRID_W          HUB75_W
#define GRID_H          HUB75_H

// IMU gravity control thresholds
#define GRAVITY_TILT_THRESHOLD  0.3f   // Minimum tilt to change gravity direction
#define GRAVITY_DEAD_ZONE       0.1f   // Dead zone for "no gravity" state

// ============================================================
// GPU Command Protocol
// ============================================================

enum class Cmd : uint8_t {
  NOP             = 0x00,
  DRAW_PIXEL      = 0x40,
  DRAW_LINE       = 0x41,
  DRAW_RECT       = 0x42,
  DRAW_FILL       = 0x43,
  DRAW_CIRCLE     = 0x44,
  CLEAR           = 0x47,
  SET_TARGET      = 0x50,
  PRESENT         = 0x51,
  OLED_CLEAR      = 0x60,
  OLED_LINE       = 0x61,
  OLED_FILL       = 0x63,
  OLED_CIRCLE     = 0x64,
  OLED_PRESENT    = 0x65,
  PING            = 0xF0,
  RESET           = 0xFF,
};

// ============================================================
// Color Helper
// ============================================================

struct Color {
  uint8_t r, g, b;
  
  constexpr Color() : r(0), g(0), b(0) {}
  constexpr Color(uint8_t r, uint8_t g, uint8_t b) : r(r), g(g), b(b) {}
  
  // Predefined colors
  static constexpr Color black()   { return Color(0, 0, 0); }
  static constexpr Color white()   { return Color(255, 255, 255); }
  static constexpr Color red()     { return Color(255, 0, 0); }
  static constexpr Color green()   { return Color(0, 255, 0); }
  static constexpr Color blue()    { return Color(0, 0, 255); }
  static constexpr Color yellow()  { return Color(255, 255, 0); }
  static constexpr Color cyan()    { return Color(0, 255, 255); }
  static constexpr Color magenta() { return Color(255, 0, 255); }
  static constexpr Color orange()  { return Color(255, 128, 0); }
  
  // Create from HSV (h: 0-360, s: 0-100, v: 0-100)
  static Color fromHSV(int h, int s, int v) {
    h = h % 360;
    float fs = s / 100.0f;
    float fv = v / 100.0f;
    float c = fv * fs;
    float x = c * (1.0f - fabsf(fmodf(h / 60.0f, 2.0f) - 1.0f));
    float m = fv - c;
    float r, g, b;
    if (h < 60)      { r = c; g = x; b = 0; }
    else if (h < 120) { r = x; g = c; b = 0; }
    else if (h < 180) { r = 0; g = c; b = x; }
    else if (h < 240) { r = 0; g = x; b = c; }
    else if (h < 300) { r = x; g = 0; b = c; }
    else              { r = c; g = 0; b = x; }
    return Color((uint8_t)((r + m) * 255), (uint8_t)((g + m) * 255), (uint8_t)((b + m) * 255));
  }
  
  // Blend with another color
  Color blend(const Color& other, float t) const {
    return Color(
      (uint8_t)(r + (other.r - r) * t),
      (uint8_t)(g + (other.g - g) * t),
      (uint8_t)(b + (other.b - b) * t)
    );
  }
  
  // Darken/brighten
  Color darken(float factor) const {
    return Color((uint8_t)(r * factor), (uint8_t)(g * factor), (uint8_t)(b * factor));
  }
  
  bool operator==(const Color& o) const { return r == o.r && g == o.g && b == o.b; }
  bool operator!=(const Color& o) const { return !(*this == o); }
};

// ============================================================
// GPU Display Driver - Clean, Composable API
// ============================================================

class GpuDisplay {
private:
  bool initialized_ = false;
  
  void send(Cmd cmd, const uint8_t* data = nullptr, uint16_t len = 0) {
    uint8_t header[5] = {
      0xAA, 0x55,
      static_cast<uint8_t>(cmd),
      static_cast<uint8_t>(len & 0xFF),
      static_cast<uint8_t>((len >> 8) & 0xFF)
    };
    uart_write_bytes(GPU_UART_NUM, header, 5);
    if (len > 0 && data) {
      uart_write_bytes(GPU_UART_NUM, data, len);
    }
    uart_wait_tx_done(GPU_UART_NUM, pdMS_TO_TICKS(10));
  }
  
  // Pack int16 to bytes (little endian)
  static void pack16(uint8_t* buf, int16_t val) {
    buf[0] = val & 0xFF;
    buf[1] = (val >> 8) & 0xFF;
  }

public:
  // ---- Initialization ----
  bool init() {
    uart_config_t cfg = {
      .baud_rate = GPU_BAUD,
      .data_bits = UART_DATA_8_BITS,
      .parity = UART_PARITY_DISABLE,
      .stop_bits = UART_STOP_BITS_1,
      .flow_ctrl = UART_HW_FLOWCTRL_DISABLE,
      .rx_flow_ctrl_thresh = 0,
      .source_clk = UART_SCLK_DEFAULT,
      .flags = { .allow_pd = 0, .backup_before_sleep = 0 }
    };
    
    // IMPORTANT: driver_install BEFORE param_config!
    esp_err_t err = uart_driver_install(GPU_UART_NUM, 4096, 4096, 0, nullptr, 0);
    if (err != ESP_OK) {
      ESP_LOGE(TAG, "UART driver install failed: %d", err);
      return false;
    }
    
    err = uart_param_config(GPU_UART_NUM, &cfg);
    if (err != ESP_OK) {
      ESP_LOGE(TAG, "UART param config failed: %d", err);
      return false;
    }
    
    err = uart_set_pin(GPU_UART_NUM, GPU_UART_TX, GPU_UART_RX, -1, -1);
    if (err != ESP_OK) {
      ESP_LOGE(TAG, "UART set pin failed: %d", err);
      return false;
    }
    
    ESP_LOGI(TAG, "GPU UART OK: TX=%d, RX=%d, %d baud", GPU_UART_TX, GPU_UART_RX, GPU_BAUD);
    initialized_ = true;
    
    // Handshake with GPU
    vTaskDelay(pdMS_TO_TICKS(100));
    ping();
    vTaskDelay(pdMS_TO_TICKS(50));
    reset();
    vTaskDelay(pdMS_TO_TICKS(100));
    
    return true;
  }
  
  // ---- System Commands ----
  void ping() { send(Cmd::PING); }
  void reset() { send(Cmd::RESET); }
  
  // ---- HUB75 Display (128x32 RGB) ----
  
  void hub75_clear(Color c = Color::black()) {
    uint8_t data[3] = {c.r, c.g, c.b};
    send(Cmd::SET_TARGET, (const uint8_t*)"\x00", 1);
    send(Cmd::CLEAR, data, 3);
  }
  
  void hub75_present() {
    send(Cmd::SET_TARGET, (const uint8_t*)"\x00", 1);
    send(Cmd::PRESENT);
  }
  
  void hub75_pixel(int16_t x, int16_t y, Color c) {
    if (x < 0 || x >= HUB75_W || y < 0 || y >= HUB75_H) return;
    uint8_t data[7];
    pack16(&data[0], x);
    pack16(&data[2], y);
    data[4] = c.r; data[5] = c.g; data[6] = c.b;
    send(Cmd::SET_TARGET, (const uint8_t*)"\x00", 1);
    send(Cmd::DRAW_PIXEL, data, 7);
  }
  
  void hub75_line(int16_t x1, int16_t y1, int16_t x2, int16_t y2, Color c) {
    uint8_t data[11];
    pack16(&data[0], x1);
    pack16(&data[2], y1);
    pack16(&data[4], x2);
    pack16(&data[6], y2);
    data[8] = c.r; data[9] = c.g; data[10] = c.b;
    send(Cmd::SET_TARGET, (const uint8_t*)"\x00", 1);
    send(Cmd::DRAW_LINE, data, 11);
  }
  
  void hub75_rect(int16_t x, int16_t y, int16_t w, int16_t h, Color c) {
    uint8_t data[11];
    pack16(&data[0], x);
    pack16(&data[2], y);
    pack16(&data[4], w);
    pack16(&data[6], h);
    data[8] = c.r; data[9] = c.g; data[10] = c.b;
    send(Cmd::SET_TARGET, (const uint8_t*)"\x00", 1);
    send(Cmd::DRAW_RECT, data, 11);
  }
  
  void hub75_fill(int16_t x, int16_t y, int16_t w, int16_t h, Color c) {
    uint8_t data[11];
    pack16(&data[0], x);
    pack16(&data[2], y);
    pack16(&data[4], w);
    pack16(&data[6], h);
    data[8] = c.r; data[9] = c.g; data[10] = c.b;
    send(Cmd::SET_TARGET, (const uint8_t*)"\x00", 1);
    send(Cmd::DRAW_FILL, data, 11);
  }
  
  void hub75_circle(int16_t cx, int16_t cy, int16_t r, Color c) {
    uint8_t data[9];
    pack16(&data[0], cx);
    pack16(&data[2], cy);
    pack16(&data[4], r);
    data[6] = c.r; data[7] = c.g; data[8] = c.b;
    send(Cmd::SET_TARGET, (const uint8_t*)"\x00", 1);
    send(Cmd::DRAW_CIRCLE, data, 9);
  }
  
  // ---- OLED Display (128x128 Monochrome) ----
  
  void oled_clear() {
    send(Cmd::OLED_CLEAR);
  }
  
  void oled_present() {
    send(Cmd::OLED_PRESENT);
  }
  
  void oled_line(int16_t x1, int16_t y1, int16_t x2, int16_t y2, bool on = true) {
    uint8_t data[9];
    pack16(&data[0], x1);
    pack16(&data[2], y1);
    pack16(&data[4], x2);
    pack16(&data[6], y2);
    data[8] = on ? 1 : 0;
    send(Cmd::OLED_LINE, data, 9);
  }
  
  void oled_fill(int16_t x, int16_t y, int16_t w, int16_t h, bool on = true) {
    uint8_t data[9];
    pack16(&data[0], x);
    pack16(&data[2], y);
    pack16(&data[4], w);
    pack16(&data[6], h);
    data[8] = on ? 1 : 0;
    send(Cmd::OLED_FILL, data, 9);
  }
  
  void oled_circle(int16_t cx, int16_t cy, int16_t r, bool on = true) {
    uint8_t data[7];
    pack16(&data[0], cx);
    pack16(&data[2], cy);
    pack16(&data[4], r);
    data[6] = on ? 1 : 0;
    send(Cmd::OLED_CIRCLE, data, 7);
  }
  
  // ---- Batch Pixel Drawing (optimized for many particles) ----
  // Note: Due to UART overhead, we'll send pixels in batches
  
  void hub75_pixels_begin() {
    send(Cmd::SET_TARGET, (const uint8_t*)"\x00", 1);
  }
  
  void hub75_pixel_raw(int16_t x, int16_t y, Color c) {
    if (x < 0 || x >= HUB75_W || y < 0 || y >= HUB75_H) return;
    uint8_t data[7];
    pack16(&data[0], x);
    pack16(&data[2], y);
    data[4] = c.r; data[5] = c.g; data[6] = c.b;
    send(Cmd::DRAW_PIXEL, data, 7);
  }
};

// Global GPU instance
static GpuDisplay gpu;

// ============================================================
// Particle Types
// ============================================================

enum class ParticleType : uint8_t {
  EMPTY = 0,
  SAND,
  WATER,
  STONE,
  FIRE,
  WOOD,
  OIL,
  COUNT
};

// Particle colors (with slight variation)
static Color getParticleColor(ParticleType type, int variation = 0) {
  switch (type) {
    case ParticleType::SAND:   return Color(220 - variation*3, 180 - variation*2, 80 + variation*2);
    case ParticleType::WATER:  return Color(30 + variation*2, 100 + variation*3, 200 + variation*2);
    case ParticleType::STONE:  return Color(100 + variation*2, 100 + variation*2, 110 + variation*2);
    case ParticleType::FIRE:   return Color(255, 100 + variation*10, variation*5);
    case ParticleType::WOOD:   return Color(139 - variation*3, 90 - variation*2, 43 + variation);
    case ParticleType::OIL:    return Color(60 + variation, 50 + variation, 30 + variation);
    default:                   return Color::black();
  }
}

static const char* getParticleName(ParticleType type) {
  switch (type) {
    case ParticleType::SAND:   return "SAND";
    case ParticleType::WATER:  return "WATER";
    case ParticleType::STONE:  return "STONE";
    case ParticleType::FIRE:   return "FIRE";
    case ParticleType::WOOD:   return "WOOD";
    case ParticleType::OIL:    return "OIL";
    default:                   return "EMPTY";
  }
}

// ============================================================
// Simulation Grid
// ============================================================

struct Particle {
  ParticleType type = ParticleType::EMPTY;
  uint8_t variation = 0;   // Color variation
  uint8_t lifetime = 255;  // For fire
  bool updated = false;    // Already processed this frame
};

// ============================================================
// Sensor Data Structures (defined early for use in SandSimulation)
// ============================================================

struct ImuData {
  float accelX, accelY, accelZ;
  float gyroX, gyroY, gyroZ;
  float temperature;
  bool valid;
};

struct EnvironmentalData {
  float temperature;    // °C
  float humidity;       // %RH
  float pressure;       // hPa
  float altitude;       // meters (calculated from pressure)
  bool valid;
};

struct GpsData {
  float latitude;       // degrees (positive = N, negative = S)
  float longitude;      // degrees (positive = E, negative = W)
  float altitude;       // meters above sea level
  float speed;          // km/h
  float course;         // degrees
  int satellites;       // number of satellites in view
  int hour, minute, second;  // UTC time
  int day, month, year;      // UTC date
  bool hasfix;          // true if GPS has a valid fix
  bool valid;           // true if data was read successfully
};

struct AudioData {
  int32_t level;      // Raw audio level (absolute amplitude)
  float levelDb;      // Level in dB (rough estimate)
  float peakLevel;    // Peak level (for VU meter)
  bool valid;
};

struct AllSensorData {
  ImuData imu;
  EnvironmentalData env;
  GpsData gps;
  AudioData audio;
};
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
