Cyberspecies/Synth-Head/Software/Testing_N_Experimentation/Alpha_Release_Stack/scenes/scene_schema.yaml

# ============================================================
# ARCOS Scene Schema Definition
# ============================================================
# This file defines how scene YAML files are structured and
# how they should be rendered in the web UI.
#
# UI Control Types:
#   dropdown   - Select from predefined options
#   slider     - Numeric slider (float or int)
#   toggle     - Boolean on/off switch
#   color      - RGB color picker
#   text       - Text input field
#   number     - Numeric input (no slider)
#   readonly   - Display only, not editable
#   file       - File/sprite selector
#   group      - Contains nested fields
#   list       - Dynamic list of items
#
# Each field can have:
#   _ui:        Control type (required for UI generation)
#   _label:     Display name (defaults to field key)
#   _desc:      Tooltip/help text
#   _options:   For dropdown - list of {label, value}
#   _min:       Minimum value (slider/number)
#   _max:       Maximum value (slider/number)  
#   _step:      Step increment (slider/number)
#   _unit:      Unit suffix (px, %, ms, etc.)
#   _default:   Default value
#   _readonly:  Make field read-only
#   _visible:   Show/hide field (default true)
#   _category:  Group category name
# ============================================================

Schema:
  version: "1.0"
  name: "Scene Configuration"
  description: "Standard scene format for ARCOS display system"

# ============================================================
# GLOBAL SETTINGS SECTION
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
